witalis3/UA3REO-DDC-Transceiver/Schematic/Wolf-2/Altium_Designer/W2-M_BOARD/Registr.xlsx

Регистр на схеме | Общий БИТ № | Назначение | При = 0 | При = 1
U19 | 0 | Резерв
 | 1 | VHF_TX | Передача ТХ от 2m и выше
 | 2 | FM BAND | Включение FM диапазона |  | Управление ФНЧ
 | 3 | LNA | Включение LNA |  | HFAMP_B0 | HFAMP_B1 | HFAMP_B2 | HFAMP_B3 | BAND ФНЧ
 | 4 | 2.4G BAND | Включение диапазона 2.4G |  | 0 | 0 | 0 | 0 | 40m
 | 5 | 1.2G BAND | Включение диапазона 1.2G |  | 1 | 0 | 0 | 0 | 20m
 | 6 | 430 BAND | Включение диапазона 430 |  | 0 | 1 | 0 | 0 | 15m
 | 7 | 144 BAND | Включение диапазона 144 |  | 1 | 1 | 0 | 0 | 10m
U20 | 8 | HFAMP_B0 | Управление ФНЧ |  | 0 | 0 | 1 | 0 | 6m
 | 9 | HFAMP_B1 |  |  | 1 | 0 | 1 | 0 | 80m
 | 10 | HFAMP_B2 |  |  | 0 | 1 | 1 | 0 | 160m
 | 11 | HFAMP_B3 |  |  | 1 | 1 | 1 | 1 | Выключены
 | 12 | HF TX | Передача ТХ ниже 60МГц
 | 13 | Резерв
 | 14 | Резерв
 | 15 | FAN | Управление вентилятором | Выключен
U21 | 16 | ANT | Включение ANT2
 | 17 | TUNE T | Включение TUNE_T
 | 18 | Резерв | Резерв
 | 19 | Резерв
 | 20 | Резерв
 | 21 | Резерв
 | 22 | Резерв
 | 23 | Резерв
U23 | 24 | Резерв
 | 25 | EXT BAND0 | Внешнее управление УМ и т.д.
 | 26 | EXT BAND1
 | 27 | EXT BAND2
 | 28 | EXT BAND3
 | 29 | EXT TX |  | Всегда при TX
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
