witalis3/UA3REO-DDC-Transceiver/Schematic/Wolf-2/Altium_Designer/W2-HF_AMP/HFAmp_DN_v02.png

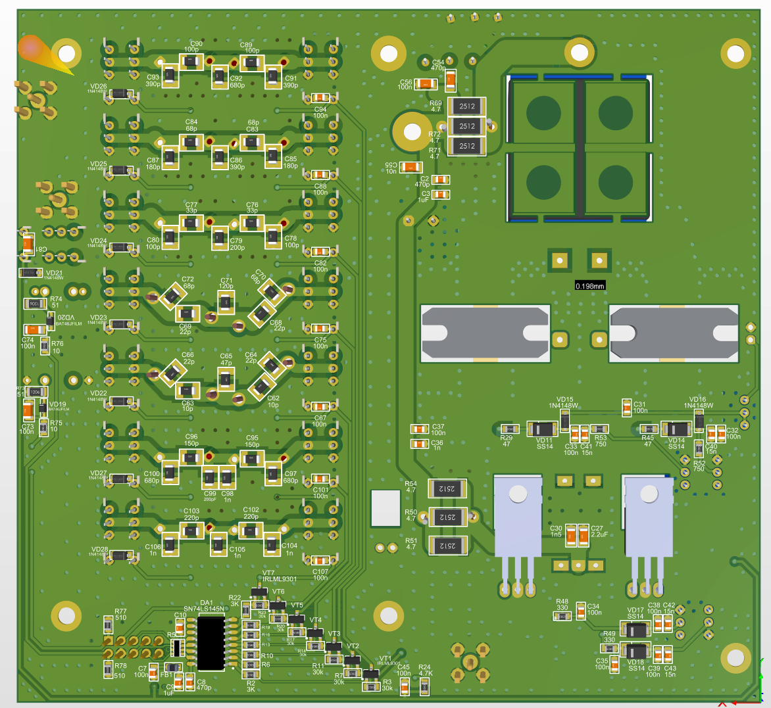
Schematic/Wolf-2/Altium_Designer/W2-HF_AMP/HFAmp_DN_v02.png
