witalis3/UA3REO-DDC-Transceiver/Schematic/Wolf-2/Altium_Designer/W2-Tuner_7x7/Tuner_UP_v01.png

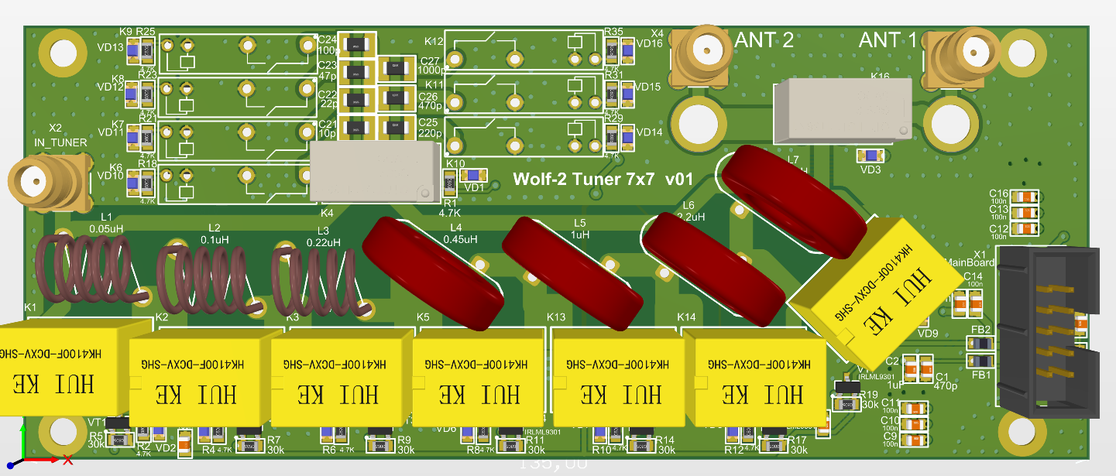
Schematic/Wolf-2/Altium_Designer/W2-Tuner_7x7/Tuner_UP_v01.png
