witalis3/UA3REO-DDC-Transceiver/Schematic/Wolf/Addons/PCB MIC MH-48/pcb4.jpg

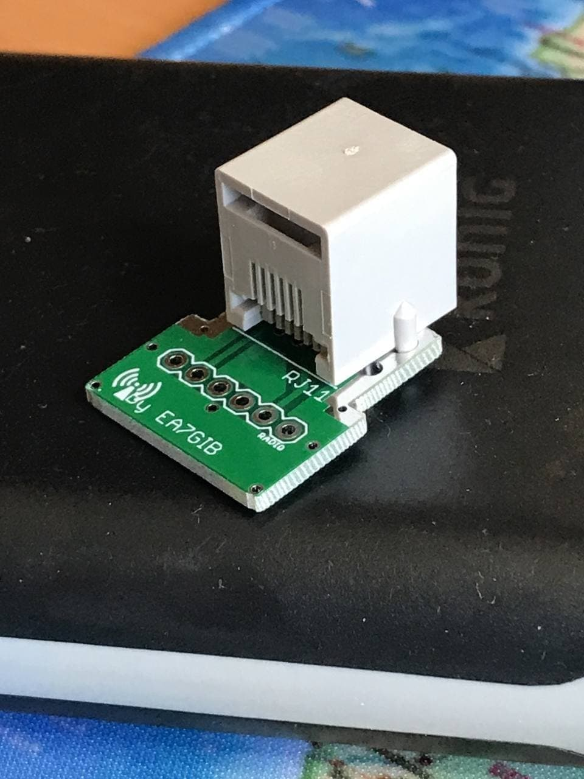
Schematic/Wolf/Addons/PCB MIC MH-48/pcb4.jpg
