witalis3/UA3REO-DDC-Transceiver/Schematic/Wolf/Assembly/SCHEMATIC-RF-UNIT-BIG-RU4PN-rev5.5_DN.png

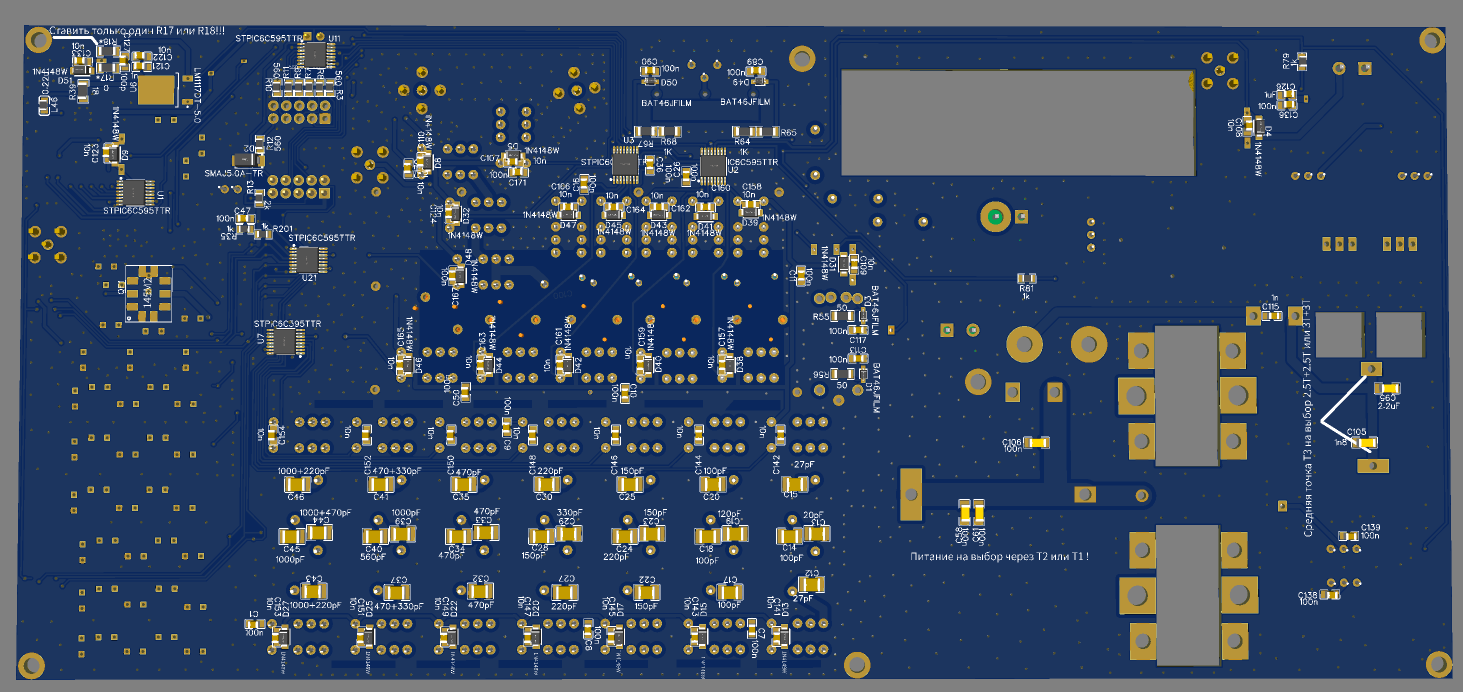
Schematic/Wolf/Assembly/SCHEMATIC-RF-UNIT-BIG-RU4PN-rev5.5_DN.png
