witalis3/UA3REO-DDC-Transceiver/Schematic/Wolf/CASE/3'2/FrontPanel/image.jpg

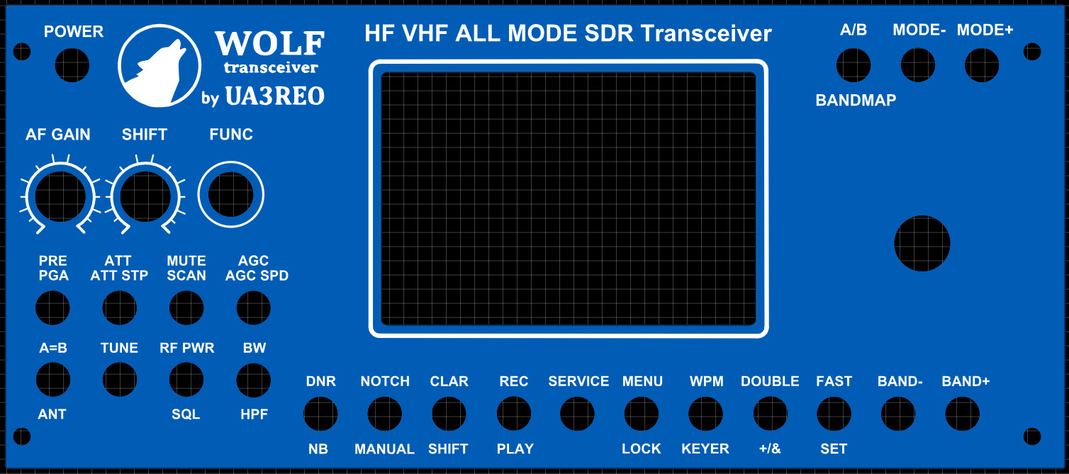
Schematic/Wolf/CASE/3'2/FrontPanel/image.jpg
