witalis3/UA3REO-DDC-Transceiver/Schematic/Wolf/BOM/BOM-RF-UNIT-BIG-rev5.xlsx

Comment | Description | Designator | Footprint | Quantity
 | Capacitor NP0 HiVolt | C96, C97, C98, C99, C100 | CAP_1206 | 5
0 | RES_0805 | R49, R50, R65, R67 | RES_0805 | 4
0.1uH | Inductor | L35 | IND_FERRITE_CORE_1 | 1
0.22uH | Inductor | L36 | IND_FERRITE_CORE_1 | 1
0.45uH | Inductor | L39 | IND_FERRITE_CORE_1 | 1
1:1 | 1:1 | T5 | TRANSF_ACORE2 | 1
1k | RES_0805 | R5, R6, R35, R42, R43, R64, R68 | RES_0805 | 7
1k | RES_0805 | R31, R33, R57, R69, R70, R71, R72 | RESC2013X60X40NL20T25 | 7
1n | CAP_0805 | C112, C115, C120 | CAP_0805 | 3
1n | CAP_0805 | C122 | 6-0805_M | 1
1n | CAP_1206 | C94, C104 | CAP_1206 | 2
1n8 | CAP_1206 | C105 | CAP_1206 | 1
1N4148 | 1N4148 | D4, D5, D6, D8, D9, D10, D11, D12, D13, D14, D15, D16, D17, D19, D20, D21, D22, D24, D25, D26, D27, D28, D29, D30, D31, D32, D38, D39, D40, D41, D42, D43, D44, D45, D46, D47, D48 | SS14 | 37
1uF | CAP_0805 | C62, C63, C79, C83, C126, C128 | CAP_0805 | 6
1uH | Inductor | L7, L8, L9, L41 | IND_FERRITE_CORE_1 | 4
1.2k | RES_0805 | R53 | RES_0805 | 1
1.2n 500V | CAP_1206 | C57 | CAP_1206 | 1
1.6uH | Inductor | L13, L14, L15, L16, L17, L18 | IND_FERRITE_CORE_1 | 6
2k | RES_0805 | R13 | RES_0805 | 1
2p | Capacitor NP0 HiVolt | C2, C3 | CAP_1206 | 2
2.2k | RES_0805 | R77, R78 | RES_0805 | 2
2.2n | Capacitor NP0 HiVolt | C48, C49 | CAP_1206 | 2
2.2p | Capacitor NP0 HiVolt | C7, C8 | CAP_1206 | 2
2.2uF | CAP_1206 | C95 | CAP_1206 | 1
2.2uH | Inductor | L42 | IND_FERRITE_CORE_1 | 1
2.7k | RES_0805 | R37 | RES_0805 | 1
2.7uH | Inductor | L19, L20, L21 | IND_FERRITE_CORE_1 | 3
4.7 | RES_1206 | R38, R47, R74, R76 | RES_1206 | 4
4.7n | CAP_0805 | C70, C75 | CAP_0805 | 2
4.7n | Capacitor NP0 HiVolt, CAP_1206 | C50, C53, C54 | CAP_1206 | 3
5p | Capacitor NP0 HiVolt | C4, C5, C6 | CAP_1206 | 3
5.1p | Capacitor NP0 HiVolt | C12, C13 | CAP_1206 | 2
6.5-30p | TZC3P300A110 | C65, C66 | 5025[2010] | 2
6.8k | RES_0805 | R32 | RES_0805 | 1
6.8n | Capacitor NP0 HiVolt | C1, C51 | CAP_1206 | 2
6.8uH | Inductor | L22, L23, L24 | IND_FERRITE_CORE_1 | 3
8.2nH | IND_0805 | L32, L33, L34 | IND_0805 | 3
10k | RES_1206 | R73 | RES_1206 | 1
10n | CAP_0805 | C121 | 6-0805_M | 1
10n | CAP_1206 | C69, C92, C102 | CAP_1206 | 3
10p | Capacitor | C84 | B32620A0682J000 | 1
10p | Capacitor NP0 HiVolt | C10 | CAP_1206 | 1
10uF 25V | CAPAE_5.3x5.3h6.1 | C129 | CAPAE_5.3x5.3h6.1 | 1
10uH | Inductor | L30, L43 | IND_FERRITE_CORE | 2
11uH | Inductor | L25, L26, L27 | IND_FERRITE_CORE_1 | 3
12p | Capacitor NP0 HiVolt | C9, C11 | CAP_1206 | 2
13.8V | JX2 | J8 | 1986717-2 | 1
15n | CAP_1206 | C81, C111 | CAP_1206 | 2
18 | RES_1206 | R39 | RES_1206 | 1
20 | RES_1206 | R23, R61 | RES_1206 | 2
22 2W | CFR200J100R | R1, R2 | RES-2W | 2
22nH | IND_0805 | L48 | IND_0805 | 1
22p | Capacitor | C85 | B32620A0682J000 | 1
22p | Capacitor NP0 HiVolt | C14, C15, C16, C17, C18, C22, C23 | CAP_1206 | 7
22uF | CAPAE_6.6x6.6h5.4 | C74, C77 | CAPAE_6.6x6.6h5.4 | 2
27pF | CAP_0805 | C55 | CAP_0805 | 1
30k | RES_0805 | R4, R41, R45, R48, R75 | RES_0805 | 5
33p | Capacitor NP0 HiVolt | C20 | CAP_1206 | 1
39p | Capacitor NP0 HiVolt | C19, C21 | CAP_1206 | 2
47p | Capacitor | C86 | B32620A0682J000 | 1
47p | Capacitor NP0 HiVolt | C25 | CAP_1206 | 1
47uF 25V | CAPAE_6.6x6.6h5.4 | C119 | CAPAE_6.6x6.6h5.4 | 1
50 | RES_1206 | R55, R56 | RES_1206 | 2
56 | RES_0805 | R15, R16, R26, R27, R44 | RES_0805 | 5
56p | Capacitor NP0 HiVolt | C24, C26, C27, C28, C32, C33 | CAP_1206 | 6
82p | Capacitor NP0 HiVolt | C30, C37, C39 | CAP_1206 | 3
100 | RES_0805 | R28, R29, R51 | RES_0805 | 3
100 | RES_1206 | R34 | RES_1206 | 1
100n | CAP_0805 | C38, C59, C64, C67, C71, C76, C78, C80, C82, C89, C90, C107, C108, C109, C110, C113, C114, C116, C117, C118, C123, C124, C125, C130, C133, C134, C135, C136, C137, C138, C139, C140, C141, C142, C143, C144, C145, C146, C147, C148, C149, C150, C151, C152, C153, C154, C155, C156, C157, C158, C159, C160, C161, C162, C163, C164, C165, C166, C167, C168, C169, C170, C171 | CAP_0805 | 63
100n | CAP_0805 | C131 | 6-0805_M | 1
100n | CAP_1206 | C58, C61, C106 | CAP_1206 | 3
100p | CAP_0805 | C72 | CAP_0805 | 1
100p | CAP_0805 | C127, C132 | 6-0805_M | 2
100p | Capacitor | C87 | B32620A0682J000 | 1
100p | Capacitor NP0 HiVolt, CAP_1206 | C29, C31, C91, C93, C103 | CAP_1206 | 5
100pF 500V | CAP_1206 | C52, C56 | CAP_1206 | 2
120p | CAP_0805 | C68, C73 | CAP_0805 | 2
120p | Capacitor NP0 HiVolt | C35 | CAP_1206 | 1
150p | Capacitor NP0 HiVolt | C34, C36 | CAP_1206 | 2
158uH | Inductor | L28, L29, L40 | IND_FERRITE_CORE_1 | 3
180p | Capacitor NP0 HiVolt | C41, C43, C44 | CAP_1206 | 3
200 | RES_0805 | R52 | RES_0805 | 1
200nH | Inductor | L1, L2, L3 | IND_FERRITE_CORE_1 | 3
200p | CAP_1206 | C101 | CAP_1206 | 1
200pF 500V | CAP_1206 | C60 | CAP_1206 | 1
220nH | IND_1206 | L31, L46 | IND_1206 | 2
220p | Capacitor | C88 | B32620A0682J000 | 1
220p | Capacitor NP0 HiVolt | C40, C42 | CAP_1206 | 2
300 | RES_1206 | R24, R25, R62, R63 | RES_1206 | 4
390p | Capacitor NP0 HiVolt | C46 | CAP_1206 | 1
430 | RES_1206 | R59, R60 | RES_1206 | 2
470 | RES_1206 | R22 | RES_1206 | 1
470p | Capacitor NP0 HiVolt | C45, C47 | CAP_1206 | 2
510 | RES_0805 | R36, R54 | RES_0805 | 2
560 | RES_0805 | R3, R7, R8, R9, R10, R11, R12 | RES_0805 | 7
620 | RES_0805 | R58 | RES_0805 | 1
680nH | Inductor | L4, L5, L6 | IND_FERRITE_CORE_1 | 3
750 | RES_1206 | R21 | RES_1206 | 1
820nH | Inductor | L10, L11, L12 | IND_FERRITE_CORE_1 | 3
2027-07-SM-RPLF | Undefined or Miscellaneous | U13 | 200307SMRPLF | 1
51022-0200 | 51022-0200 | FAN_OUT | 51022-0200 | 1
ADC | SMA | J2 | 31-5431 | 1
ADG918BRMZ | Integrated Circuit | U8, U10 | SOP65P490X110-8N | 2
ADJ-1k | 306J | R30, R40, R46 | 306J | 3
ADJ-10k | 3296W-1-103LF | R19, R20 | 3296W-1 | 2
ADJ-100 | 306J | R66 | 306J | 1
ANT1 | SMA | J1 | 31-5431 | 1
ANT2 | SMA | J5 | 31-5431 | 1
Axicom IM06 | Axicom IM06 | U4, U12 | IM06GR | 2
BAT46JFILM | Diode | D1, D3, D49, D50 | SOD2513X117N | 4
BAV99 | BAV99 | D7 | SOT23 | 1
BLM21 | BLM21 | FB1 | IND_0805 | 2
BSS123 | N-Channel Logic Level Enhancement Mode Field Effect Transistor, 1.7 V, -55 to 150 degC, 3-Pin SOT-23, RoHS, Tape and Reel | Q12 | FAIR-SOT23-3_V | 1
DAC | SMA | J9 | 31-5431 | 1
EXTERNAL | 2*5 PIN | J3 | 90131-0126 | 1
G6S-2-DC12 | Relay or Contactor | K1, K2, K3, K4, K5, K6, K7, K8, K9, K10, K11, K12, K13, K14, K15, K16, K17, K18, K19, K20, K21, K22, K23, K24, K25, K26, K27, K28, K29, K30, K31, K32, K33, K34, K35 | G6S2DC12 | 35
HiCurrent 13.8V | JX2 | J6, J7 | 1986717-2 | 2
IRLML9301 | MOSFET | Q2, Q7, Q10, Q11 | SOT23 | 4
KTY81/120 | Integrated Circuit | R14 | TO254P420X460X770-2P | 1
LM1117DT-5.0 | Integrated Circuit | U6 | TO228P991X238-3N | 1
LT1117IST-5.0 | LT1117IST-5.0 | U19 | LT1117IST-ADJ | 1
LT1117IST-ADJ | LT1117IST-ADJ | U5, U20 | LT1117IST-ADJ | 2
MOTHERBOARD | 2*5 PIN | J4 | 90131-0126 | 1
PE4302 | Integrated Circuit | U9 | QFN50P400X400X90-21N | 1
PGA-103+ / SPF5189Z | PGA-103+ / SPF5189Z | Q4 | SOT89 | 1
RA80H1415M1 | RA80H1415M1 | Q8 | RA80H1415M1 | 1
RD01MUS1 | RD01MUS1 | Q9 | SOT89 | 1
RD16HHF1 | RD16HHF1 | Q1, Q3 | RD16_V2 | 2
RD100HHF1 | RD100HHF1 | Q5, Q6 | RD100_V2 | 2
SMAJ5.0A-TR | Diode | D2 | SMBJ36CATR | 1
SS14 | SS14 | D18, D23, D35, D36, D37 | SS14 | 5
STPIC6C595TTR | Integrated Circuit | U1, U2, U3, U7, U11 | SOP65P640X120-16N | 5
SWR_TANDEM_MATCH | SWR_TANDEM_MATCH | TSWR | SWR_TANDEM_MATCH | 1
SWR_VHF | SWR_VHF | T6 | SWR_VHF | 1
TRANSF_HF1 | TRANSF_HF1 | T2 | TRANSF_HF1 | 1
TRANSF_HF2 | TRANSF_HF2 | T1 | TRANSF_HF2-3 | 1
TRANSF_HF3 | TRANSF_HF3 | T3 | TRANSF_HF3 | 1
