witalis3/UA3REO-DDC-Transceiver/Schematic/Wolf/CASE/VFO/VFO38WithExt.stl

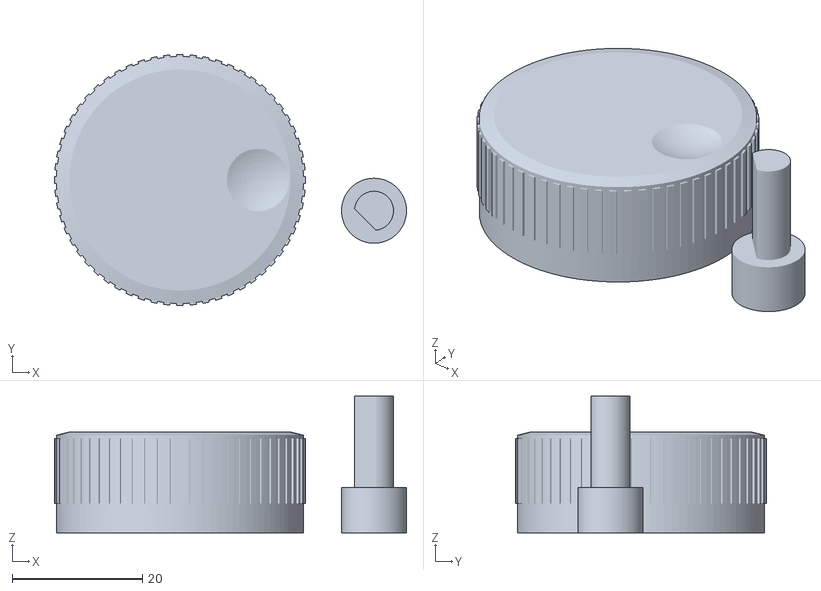
[picture p36: CAD file, 2021-11-08]
Schematic/Wolf/CASE/VFO/VFO38WithExt.stl
54.1 x 38.6 x 21.0
