witalis3/UA3REO-DDC-Transceiver/Schematic/Wolf-X1/Addons/20mm_Sec_Encoder.stl

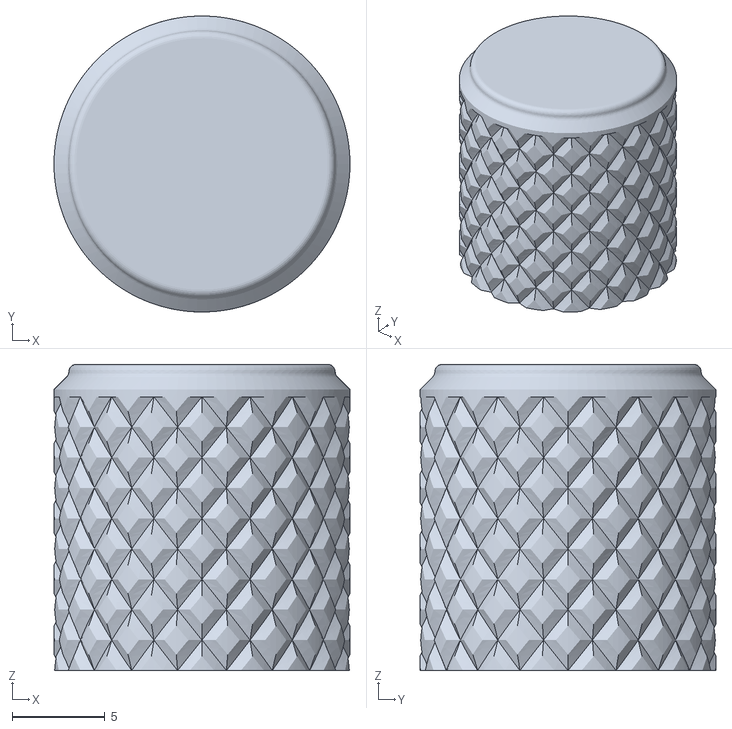
[picture p37: CAD file, 2022-07-16]
Schematic/Wolf-X1/Addons/20mm_Sec_Encoder.stl
16.0 x 16.0 x 16.6
