witalis3/UA3REO-DDC-Transceiver/Schematic/Wolf/CASE/3'2/3DPrinter/case/case_cooller.SLDPRT

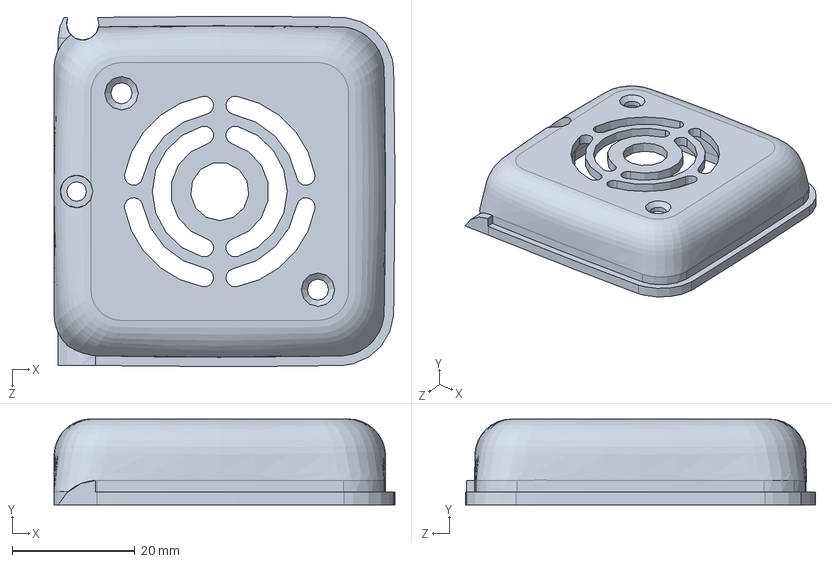
[picture p38: CAD file, 2020-11-11]
Schematic/Wolf/CASE/3'2/3DPrinter/case/case_cooller.SLDPRT
55.5 x 14.0 x 57.1 mm
