witalis3/UA3REO-DDC-Transceiver/Schematic/Wolf/CASE/3'2/3DPrinter/Potenciómetro.stp

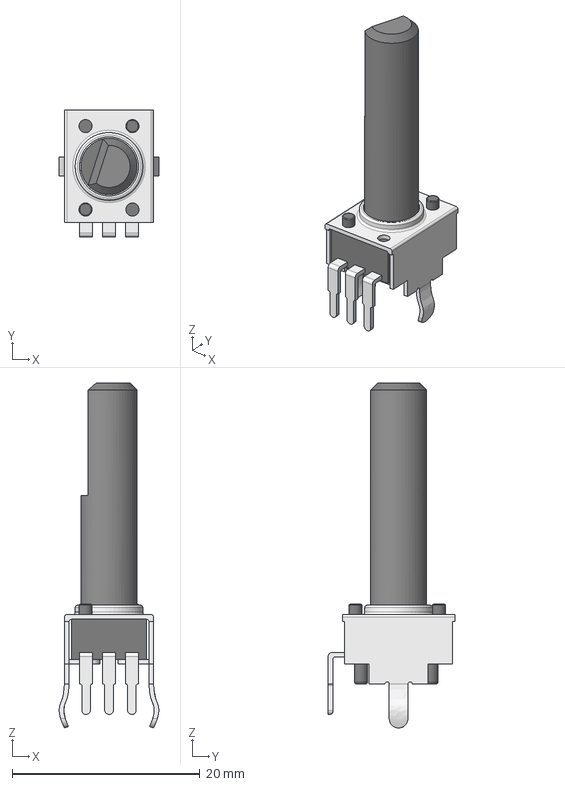
[picture p39: CAD file, 2021-01-28]
Schematic/Wolf/CASE/3'2/3DPrinter/Potenciómetro.stp
10.6 x 13.5 x 36.8 mm
