witalis3/UA3REO-DDC-Transceiver/Schematic/Wolf/CASE/7/Panel/верхняя планка волк7_2.stl

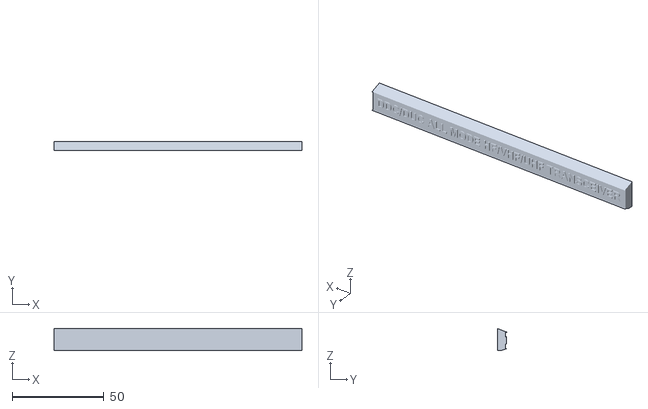
[picture p40: CAD file, 2023-04-02]
Schematic/Wolf/CASE/7/Panel/верхняя планка волк7_2.stl
135.0 x 5.00 x 12.0
