witalis3/UA3REO-DDC-Transceiver/Schematic/Wolf/CASE/VFO/ExtEncoder.stl

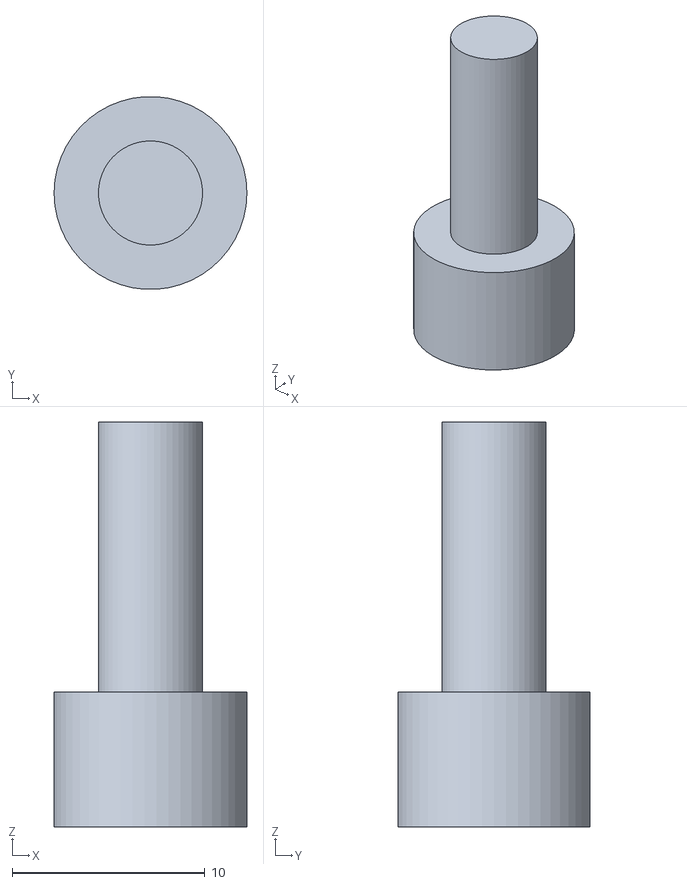
[picture p41: CAD file, 2021-11-08]
Schematic/Wolf/CASE/VFO/ExtEncoder.stl
10.0 x 9.98 x 21.0
