witalis3/UA3REO-DDC-Transceiver/Schematic/Wolf/CASE/3'2/3DPrinter/case/encoder_mount_front.SLDPRT

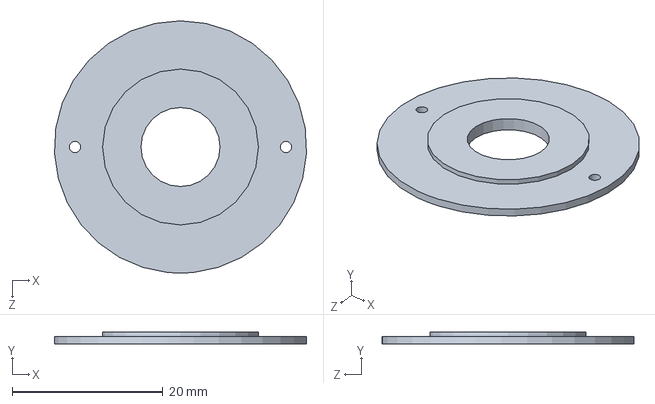
[picture p44: CAD file, 2020-11-11]
Schematic/Wolf/CASE/3'2/3DPrinter/case/encoder_mount_front.SLDPRT
33.5 x 1.65 x 33.5 mm
