witalis3/UA3REO-DDC-Transceiver/Schematic/Wolf/CASE/3'2/3DPrinter/pl-259_jack.stp

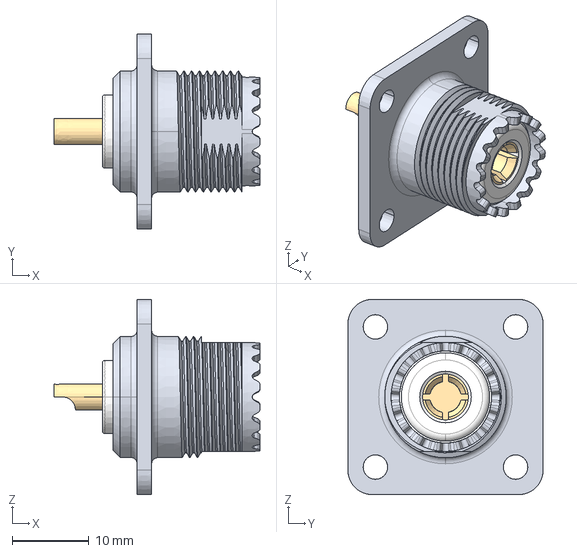
[picture p45: CAD file, 2021-01-28]
Schematic/Wolf/CASE/3'2/3DPrinter/pl-259_jack.stp
26.8 x 25.4 x 25.4 mm
