witalis3/UA3REO-DDC-Transceiver/Schematic/Wolf/CASE/7/Panel/рамка_низ_7_пр.stl

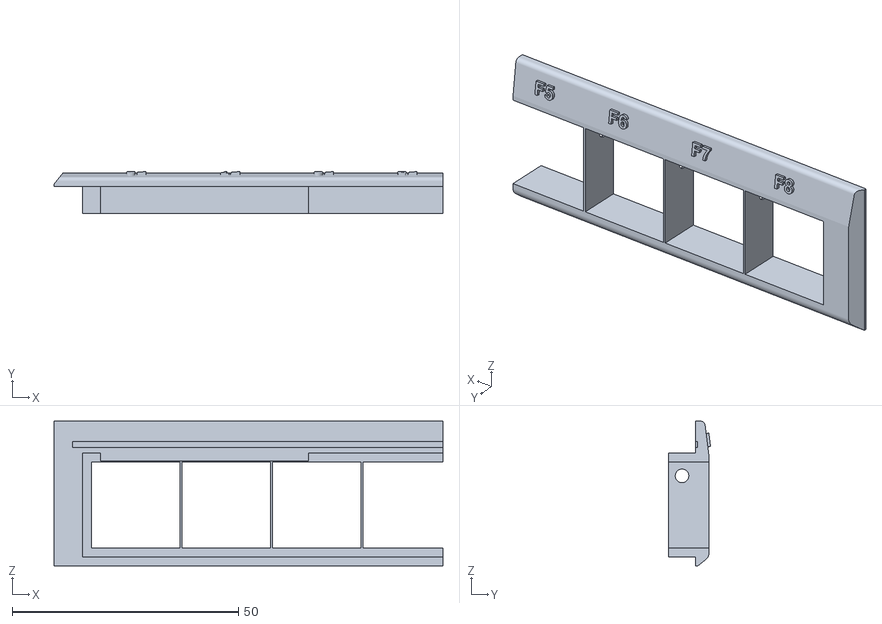
[picture p46: CAD file, 2023-04-02]
Schematic/Wolf/CASE/7/Panel/рамка_низ_7_пр.stl
86.0 x 9.31 x 32.0
