witalis3/UA3REO-DDC-Transceiver/Schematic/Wolf/CASE/3'2/3DPrinter/case/shuttle_knob_cap.SLDPRT

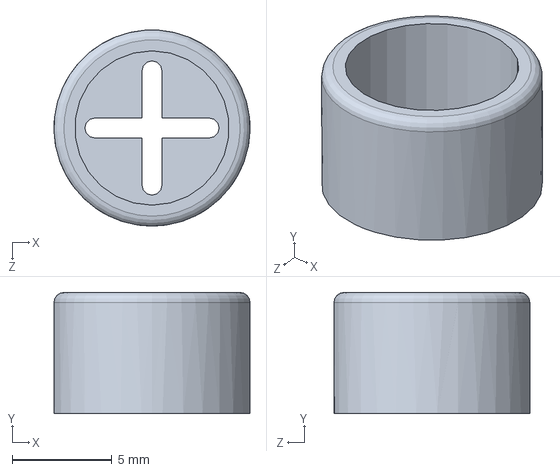
[picture p47: CAD file, 2020-11-11]
Schematic/Wolf/CASE/3'2/3DPrinter/case/shuttle_knob_cap.SLDPRT
9.84 x 6.08 x 9.85 mm
