witalis3/UA3REO-DDC-Transceiver/Schematic/Wolf/CASE/3'2/3DPrinter/GX16-8.stp

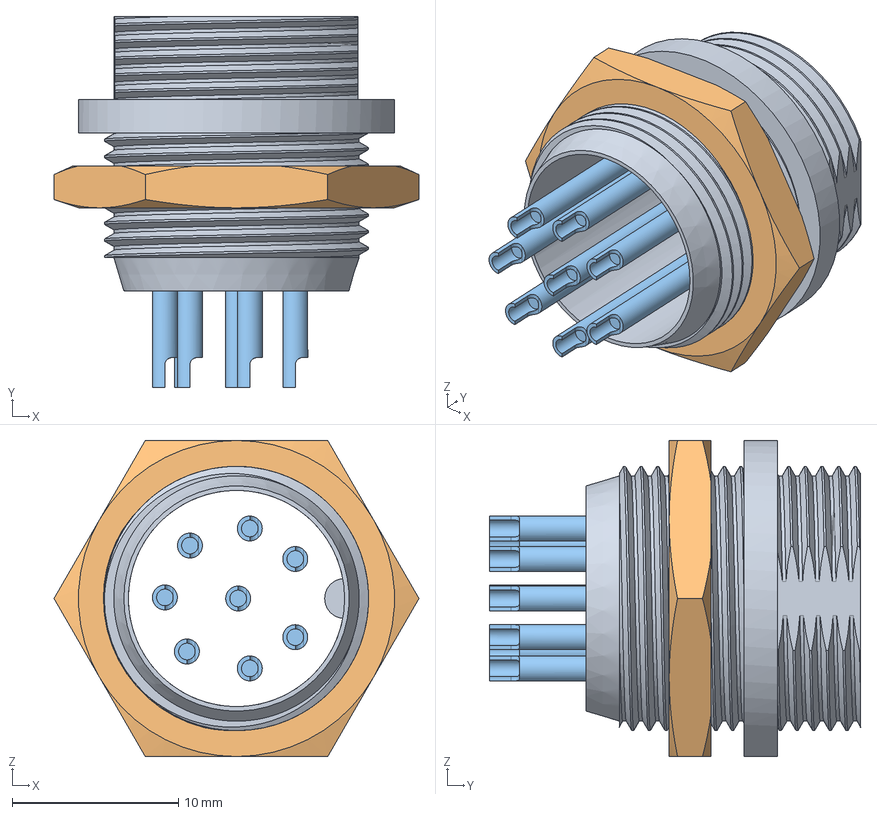
[picture p48: CAD file, 2021-01-28]
Schematic/Wolf/CASE/3'2/3DPrinter/GX16-8.stp
21.9 x 22.3 x 19.0 mm
