witalis3/UA3REO-DDC-Transceiver/Schematic/Wolf/CASE/7/Panel/рамка_низ_7_л.stl

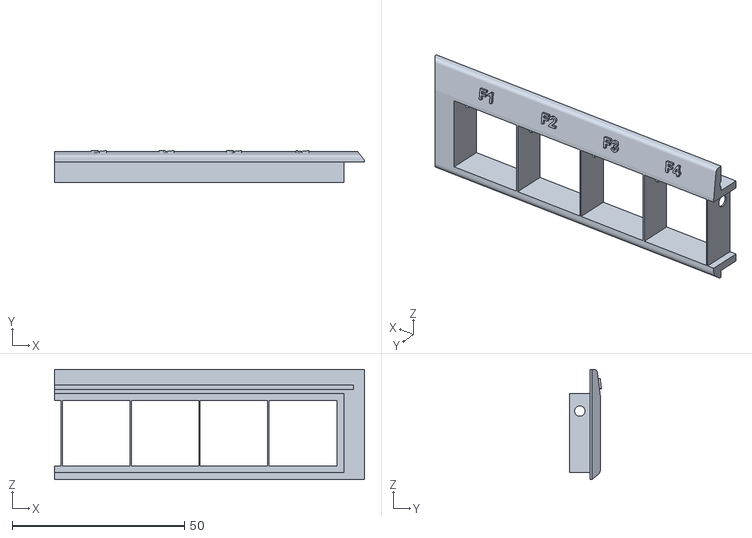
[picture p49: CAD file, 2023-04-02]
Schematic/Wolf/CASE/7/Panel/рамка_низ_7_л.stl
90.0 x 9.31 x 32.0
