witalis3/UA3REO-DDC-Transceiver/Schematic/Wolf/CASE/3'2/3DPrinter/40x40x10 DC Fan.SLDPRT

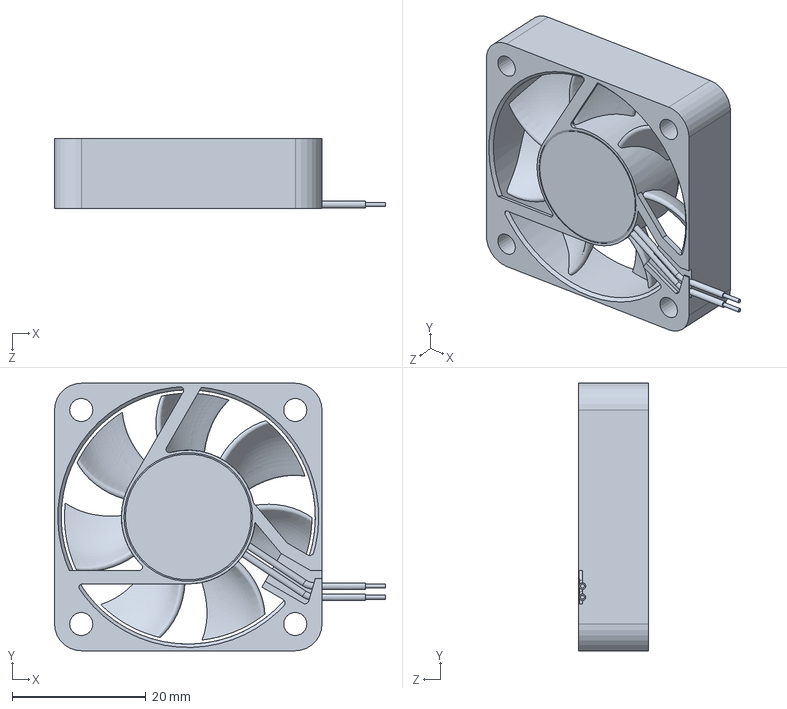
[picture p50: CAD file, 2020-11-11]
Schematic/Wolf/CASE/3'2/3DPrinter/40x40x10 DC Fan.SLDPRT
49.5 x 40.0 x 10.5 mm
