witalis3/UA3REO-DDC-Transceiver/Schematic/Wolf/CASE/3'2/3DPrinter/case/shuttle_knob.SLDPRT

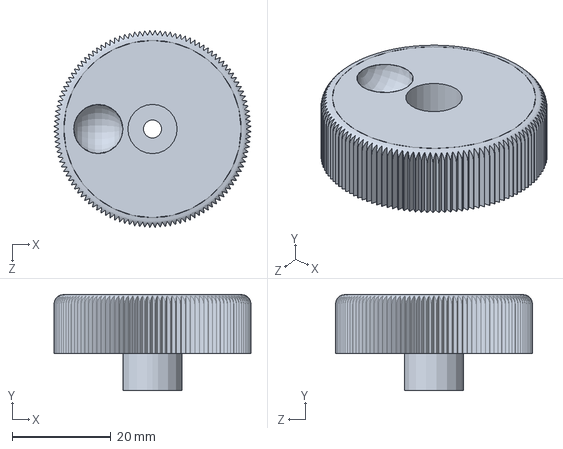
[picture p51: CAD file, 2020-11-11]
Schematic/Wolf/CASE/3'2/3DPrinter/case/shuttle_knob.SLDPRT
40.0 x 19.5 x 40.0 mm
