witalis3/UA3REO-DDC-Transceiver/Schematic/Wolf/CASE/7/Panel/кнопка_низ_7_новая.stl

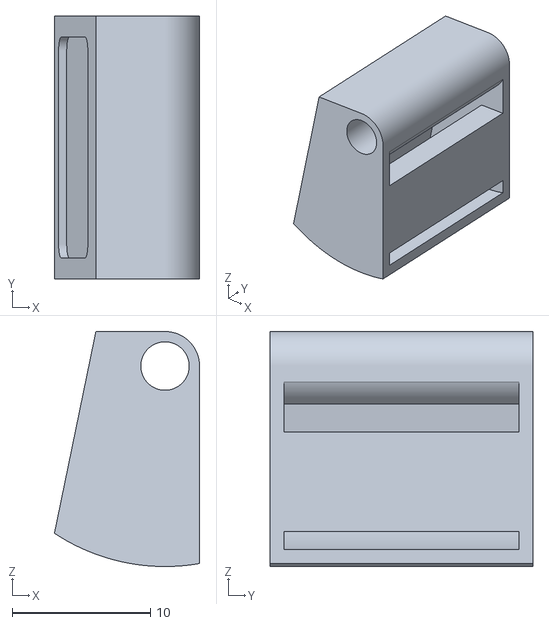
[picture p53: CAD file, 2023-04-02]
Schematic/Wolf/CASE/7/Panel/кнопка_низ_7_новая.stl
10.5 x 19.0 x 17.0
