witalis3/UA3REO-DDC-Transceiver/Schematic/Wolf/CASE/3'2/3DPrinter/FRONT.SLDPRT

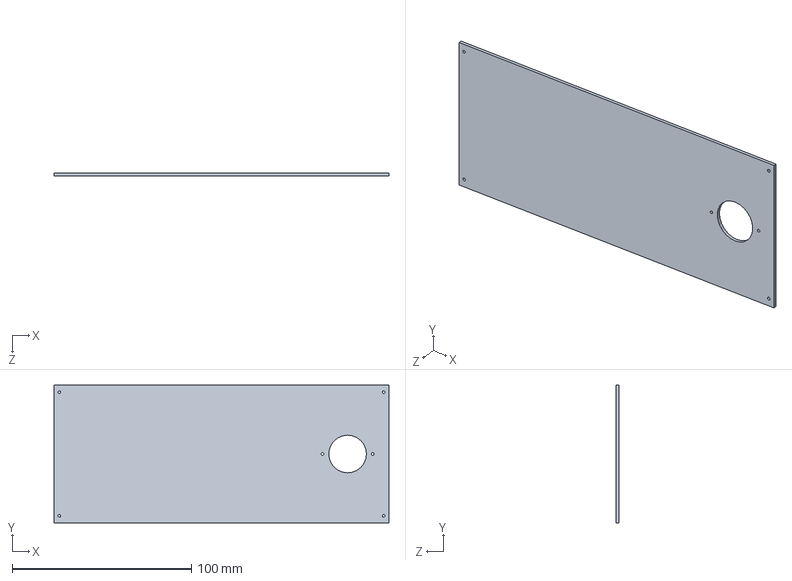
[picture p54: CAD file, 2020-11-11]
Schematic/Wolf/CASE/3'2/3DPrinter/FRONT.SLDPRT
187.0 x 77.0 x 1.60 mm
