witalis3/UA3REO-DDC-Transceiver/Schematic/Wolf/CASE/7/Panel/кнопка верх_7.stl

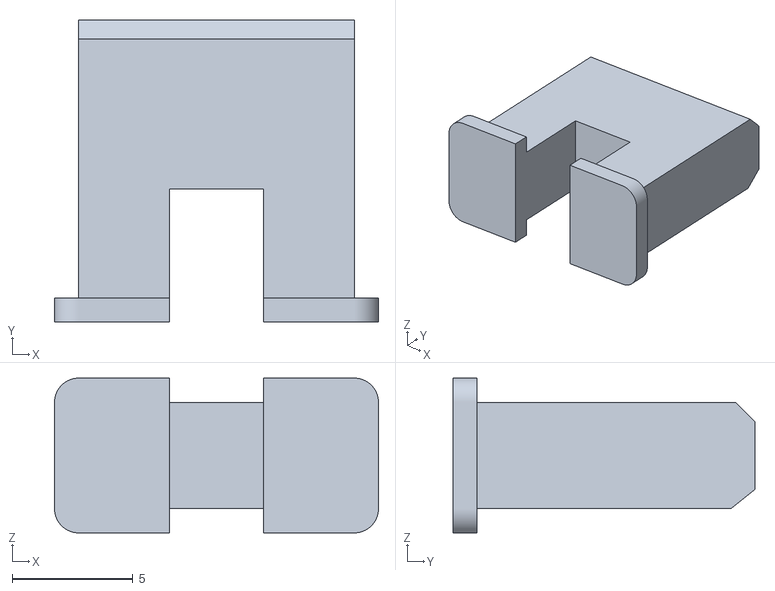
[picture p57: CAD file, 2023-04-02]
Schematic/Wolf/CASE/7/Panel/кнопка верх_7.stl
13.4 x 12.5 x 6.40
