witalis3/UA3REO-DDC-Transceiver/Schematic/Wolf/CASE/3'2/3DPrinter/speaker.SLDPRT

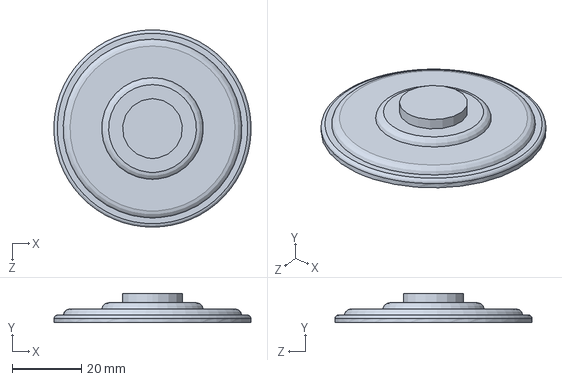
[picture p59: CAD file, 2020-11-11]
Schematic/Wolf/CASE/3'2/3DPrinter/speaker.SLDPRT
56.9 x 8.51 x 57.0 mm
