witalis3/UA3REO-DDC-Transceiver/Schematic/Wolf/CASE/3'2/3DPrinter/case/button.SLDPRT

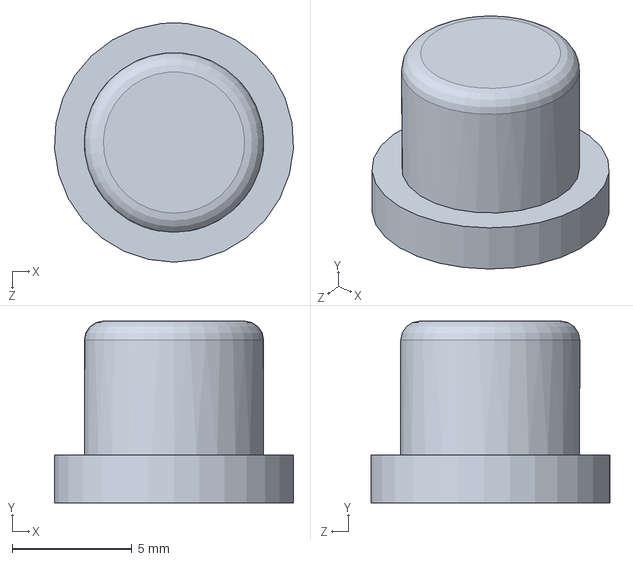
[picture p60: CAD file, 2020-11-11]
Schematic/Wolf/CASE/3'2/3DPrinter/case/button.SLDPRT
9.99 x 7.60 x 10.0 mm
