witalis3/UA3REO-DDC-Transceiver/Schematic/Wolf/CASE/3'2/3DPrinter/tactileswitch-long.SLDPRT

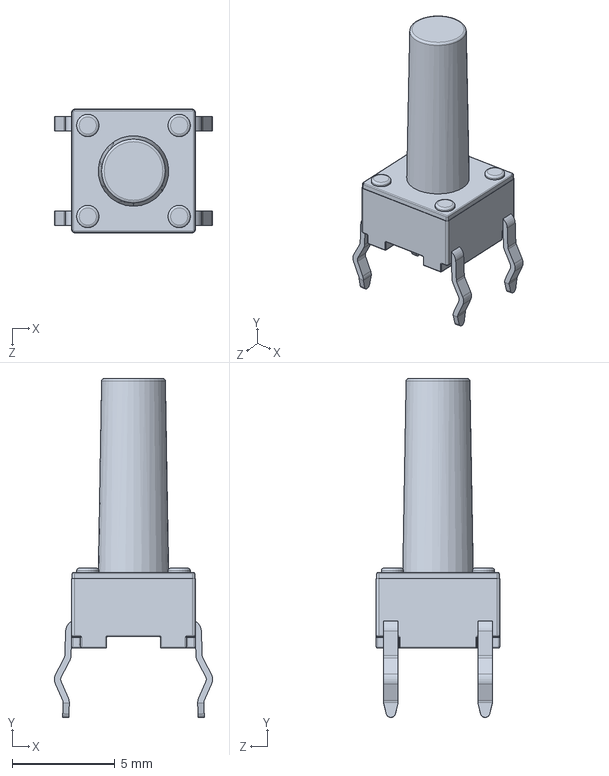
[picture p61: CAD file, 2020-11-11]
Schematic/Wolf/CASE/3'2/3DPrinter/tactileswitch-long.SLDPRT
7.69 x 16.5 x 6.01 mm
