witalis3/UA3REO-DDC-Transceiver/Schematic/Wolf/CASE/3'2/3DPrinter/case/case_back_2.SLDPRT

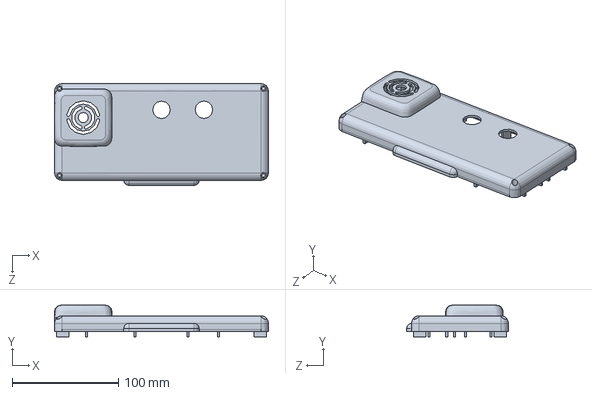
[picture p62: CAD file, 2020-11-11]
Schematic/Wolf/CASE/3'2/3DPrinter/case/case_back_2.SLDPRT
201.0 x 29.7 x 95.7 mm
