witalis3/UA3REO-DDC-Transceiver/Schematic/Wolf/CASE/3'2/3DPrinter/beam_long.SLDPRT

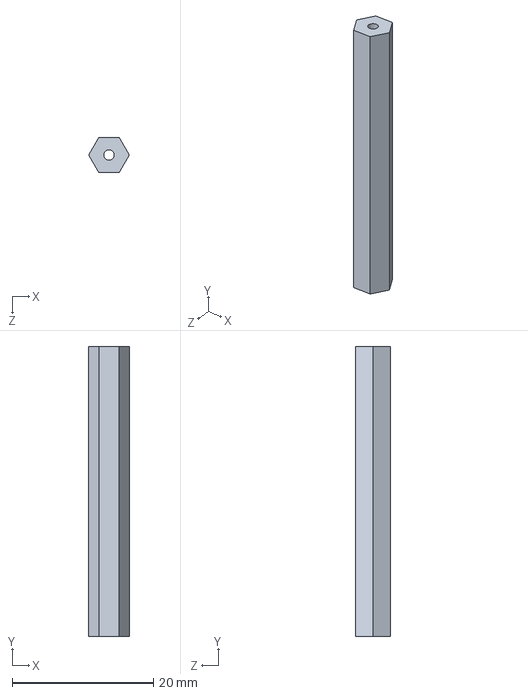
[picture p64: CAD file, 2020-11-11]
Schematic/Wolf/CASE/3'2/3DPrinter/beam_long.SLDPRT
5.77 x 41.1 x 5.00 mm
