witalis3/UA3REO-DDC-Transceiver/Schematic/Wolf/CASE/3'2/3DPrinter/case/case_speaker.SLDPRT

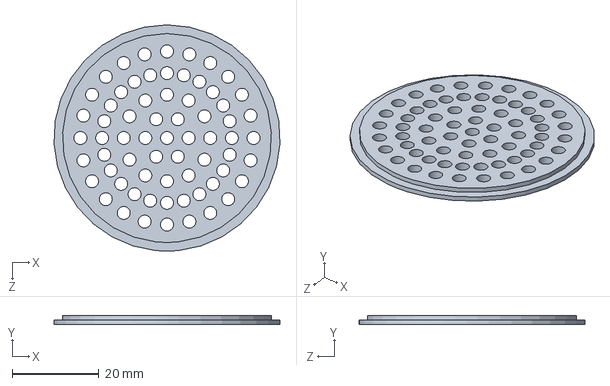
[picture p65: CAD file, 2020-11-11]
Schematic/Wolf/CASE/3'2/3DPrinter/case/case_speaker.SLDPRT
52.2 x 2.00 x 52.3 mm
