witalis3/UA3REO-DDC-Transceiver/Schematic/Wolf/CASE/3'2/3DPrinter/Mini USB.SLDPRT

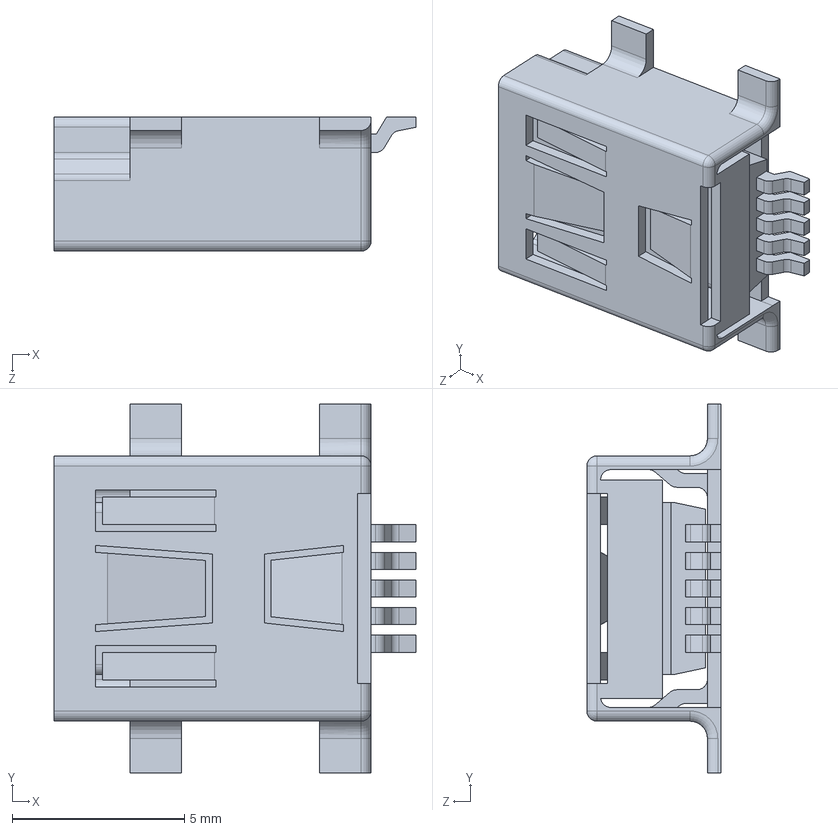
[picture p68: CAD file, 2020-11-11]
Schematic/Wolf/CASE/3'2/3DPrinter/Mini USB.SLDPRT
10.5 x 10.7 x 3.90 mm
