witalis3/UA3REO-DDC-Transceiver/Schematic/Wolf/CASE/3'2/3DPrinter/Encoder_Axis.SLDPRT

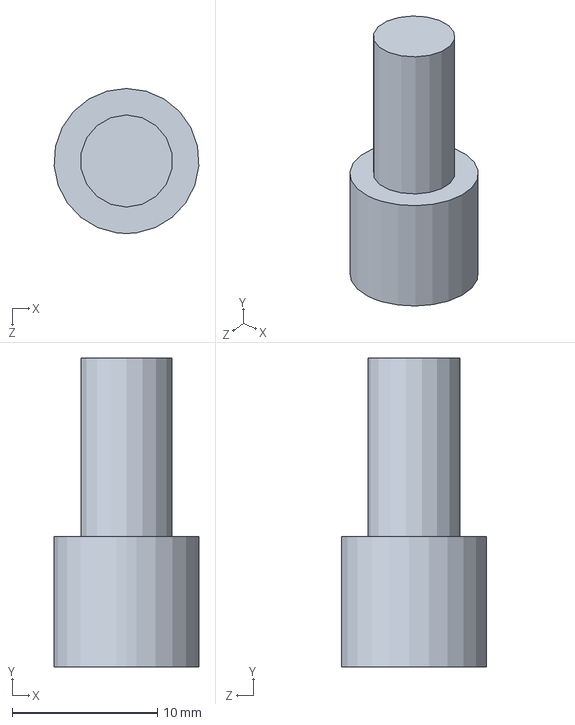
[picture p70: CAD file, 2020-11-11]
Schematic/Wolf/CASE/3'2/3DPrinter/Encoder_Axis.SLDPRT
9.98 x 21.3 x 10.0 mm
