witalis3/UA3REO-DDC-Transceiver/Schematic/Wolf/CASE/3'2/3DPrinter/Rotary Encoder.SLDPRT

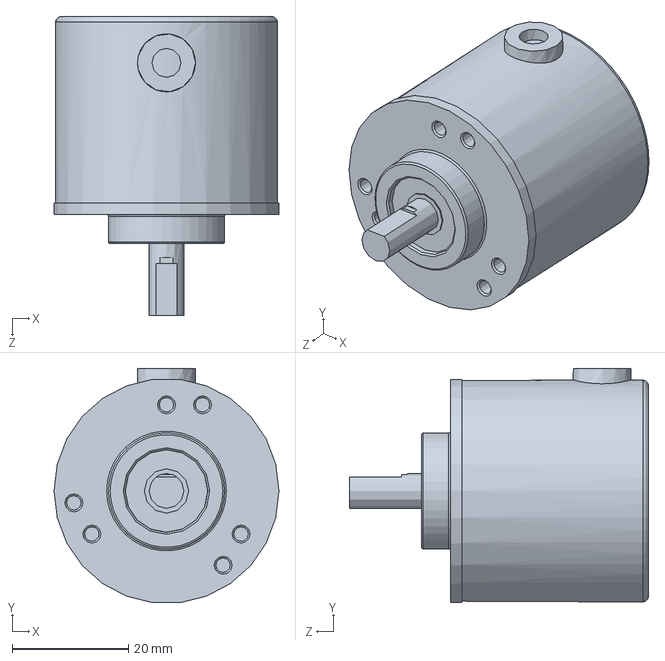
[picture p71: CAD file, 2020-05-22]
Schematic/Wolf/CASE/3'2/3DPrinter/Rotary Encoder.SLDPRT
38.7 x 40.3 x 51.5 mm
