witalis3/UA3REO-DDC-Transceiver/Stuff/Manuals/Front-Panel.xlsx

POWER
 |  |  |  |  | FRONT-3'2 |  |  |  |  |  |  | A/B BANDMAP | MODE- | MODE+
AF GAIN | SHIFT/GAIN | ENC 2
PRE PGA | ATT ATT STEP | MUTE SCAN | AGC AGC SPEED |  |  |  |  |  |  |  |  |  | MAIN ENCODER
A=B ANT | TUNE | RF POWER SQUELCH | BW HPF
 |  |  |  | DNR NB | NOTCH MANUAL | CLAR SHIFT | REC PLAY | SERVICES | MENU LOCK | WPM KEYER | DOUBLE + / & | FAST FAST SETT | BAND- | BAND+
POWER |  | FRONT-7 |  |  |  |  |  |  |  |  |  | SHIFT/GAIN | ENC 2 | AF GAIN
AUDIO 1 |  |  |  |  |  |  |  |  |  |  |  | A/B A=B | MODE+ MODE- | BAND+ BAND-
AUDIO 2
AUDIO 3
 |  |  |  |  |  |  |  |  |  |  |  |  | MAIN ENCODER
TANGENT
 |  | F1 | F2 | F3 | F4 | F5 | F6 | F7 | F8
