witalis3/UA3REO-DDC-Transceiver/Schematic/Wolf/Altium_Designer/RF-UNIT-QRP_20W/!AdditionalInfo/Consumption_Measurements.xlsx

Vin [V] | 13
TX Current Consumption without the RF Unit Board [A] | 0.4
RX Total Current Consumption [A] | 0.771
Band | Output Power (after the LPF) [W] | TX Total Consumption [A] | TX RF Unit Board Consumption [A] | RF_AMP Efficiency [-]
80m | 18.1 | 3.01 | 2.61 | 0.5334512231
40m | 20.4 | 3.83 | 3.43 | 0.457501682
30m | 19.9 | 3.14 | 2.74 | 0.5586749017
20m | 18.9 | 3.45 | 3.05 | 0.4766708701
17m | 20 | 3.25 | 2.85 | 0.5398110661
15m | 19.8 | 3.89 | 3.49 | 0.4364117258
10m | 14 | 2.99 | 2.59 | 0.4158004158
6m | 12.2 | 3.17 | 2.77 | 0.3387947792
2m | 7.1 | 2.74 | 2.34 | 0.2333990796
