witalis3/UA3REO-DDC-Transceiver/Schematic/Wolf-Lite/Scheme/Front-Unit-v2.2.pdf

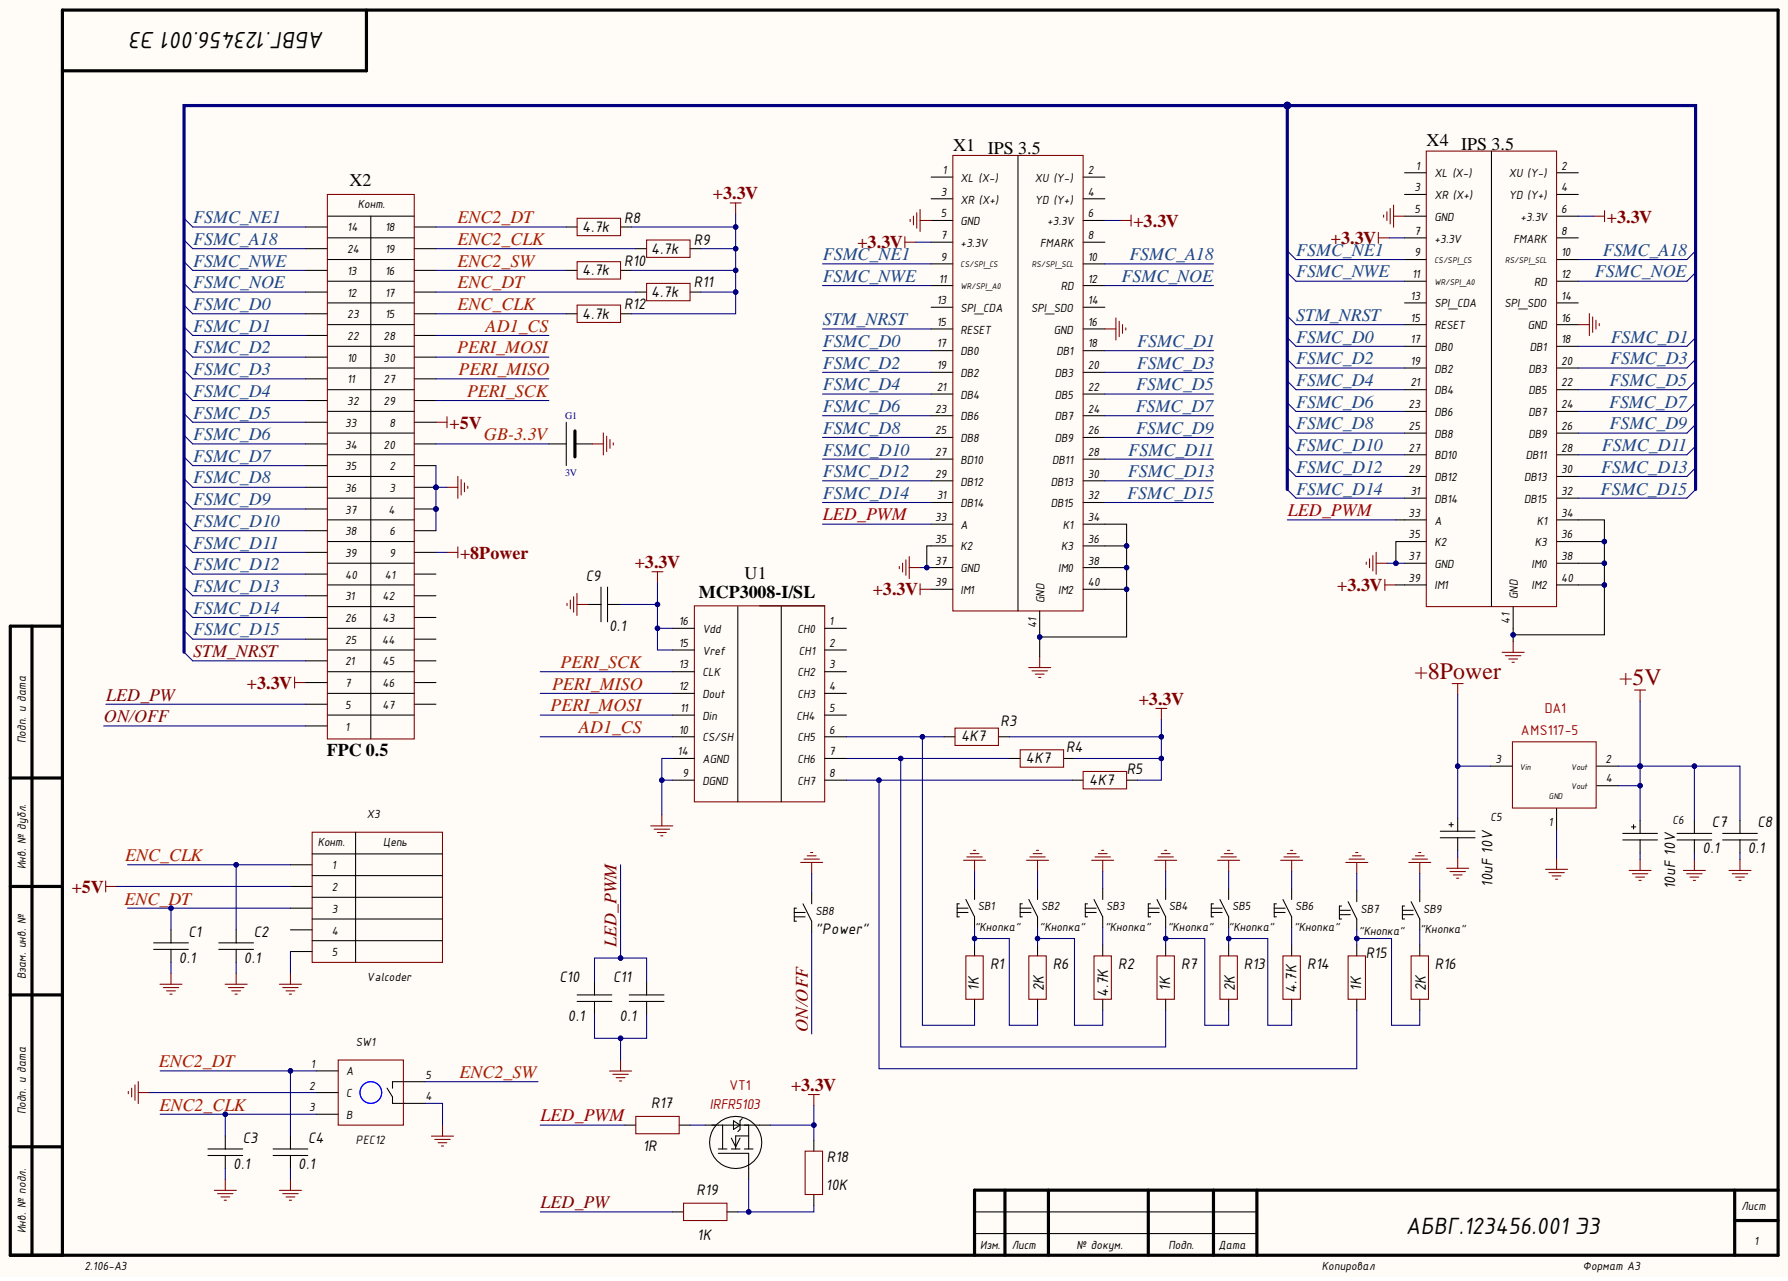
[picture p214: page 1]

Инв. № подл. Инв. № дубл. Подп. и дата Взам. инв. № Подп. и дата

Конт. | Цепь

Comment | Description | Designator | Footprint | LibRef | Quantity
0.1 | | C1, C2, C3, C4, C7, C8, C9, C10, C11 | CH0805C | Capacitor | 9
10uF 10V | | C5, C6 | TANTAL_B | TantalCap | 2
AMS117-5 | | DA1 | SOT223 | AMS117 | 1
3V | | G1 | BAT: CH224-2032 | POWER_BAT | 1
1K | | R1, R7, R15, R19 | CH0805R | Resistor | 4
4.7K | | R2, R8, R9, R10, R11, R12, R14 | CH0805R | Resistor | 7
4K7 | | R3, R4, R5 | CH0805R | Resistor | 3
2K | | R6, R13, R16 | CH0805R | Resistor | 3
1R | | R17 | CH0805R | Resistor | 1
10K | | R18 | CH0805R | Resistor | 1
"Кнопка" | 6x6mm | SB1, SB2, SB3, SB4, SB5, SB6, SB7, SB9 | BUT: 5X5 | Tactile switches | 8
"Power" | 6x6mm | SB8 | BUT: 5X5 | Tactile switches | 1
PEC12 | Encoder | SW1 | Valkoder-m2 | PEC12 | 1
MCP3008-I/SL | | U1 | 16-SOIC | MCP3008-I/SL | 1
IRFR5103 | | VT1 | SOT23_132 | N-KANAL | 1
IPS 3.5 | | X1 | FPC-40P 0.5mm | LCD-IPS 3.5 | 1
FPC 0.5 | | X2 | CON: PBD2x20 | FPC-45-0.5 | 1
Valcoder | | X3 | CON: PLS-5 | 5-Connector | 1
IPS 3.5 | | X4 | IPS 3.5 ILI9481 | LCD-IPS 3.5 | 1
