witalis3/UA3REO-DDC-Transceiver/Schematic/Wolf/Altium_Designer/RF-UNIT-QRP_20W/!AdditionalInfo/Heatsink_QRP++.pdf

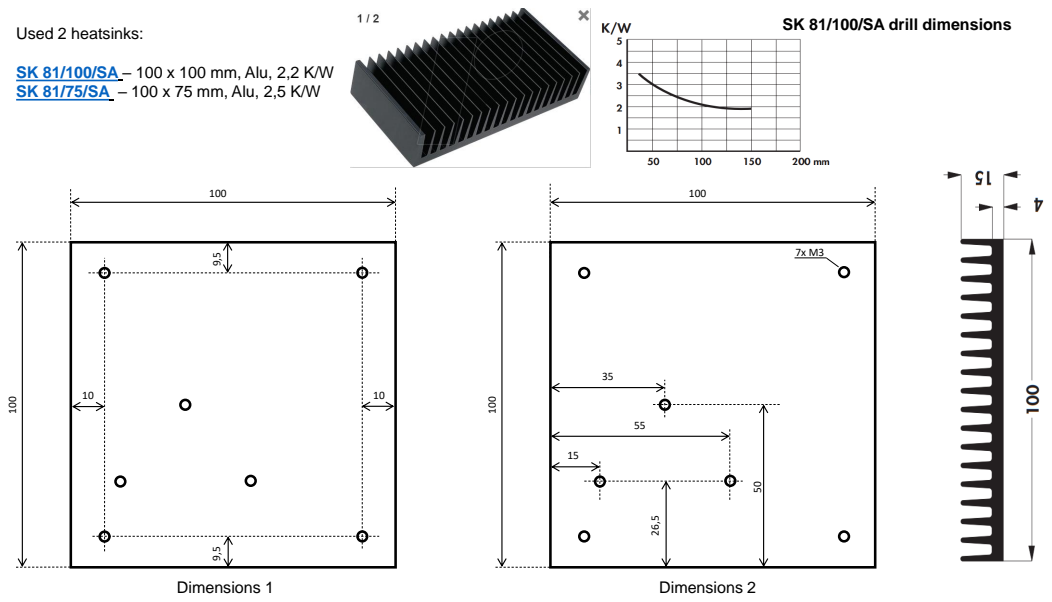
[picture p219: page 1]
Used 2 heatsinks:; Dimensions 1; Dimensions 2

SK 81/100/SA drill dimensions

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

SK 81/75/SA drill dimensions

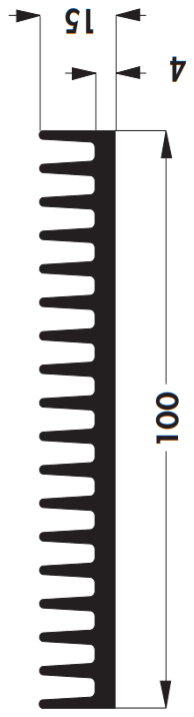
[picture p220: figure]
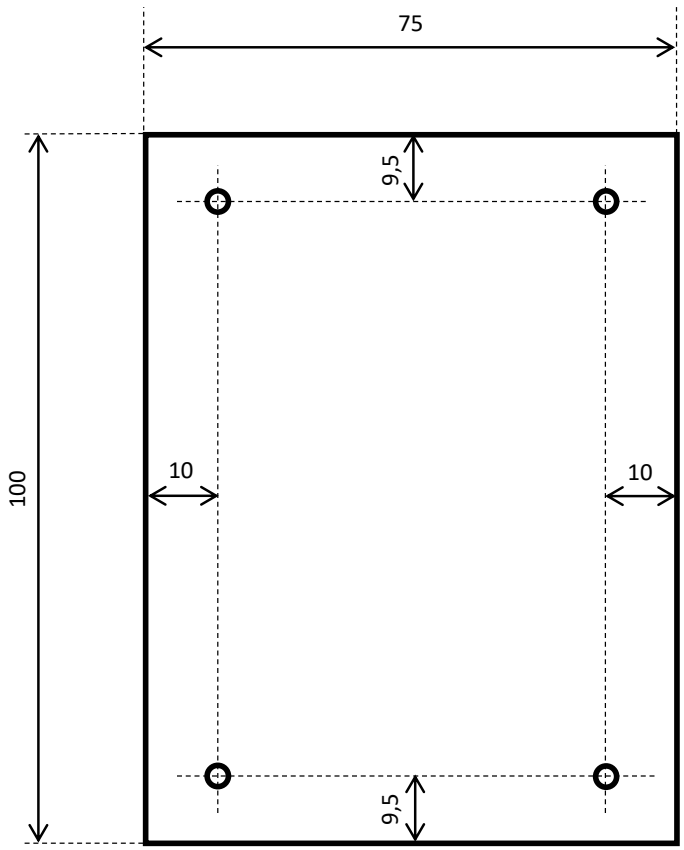
[picture p221: figure]
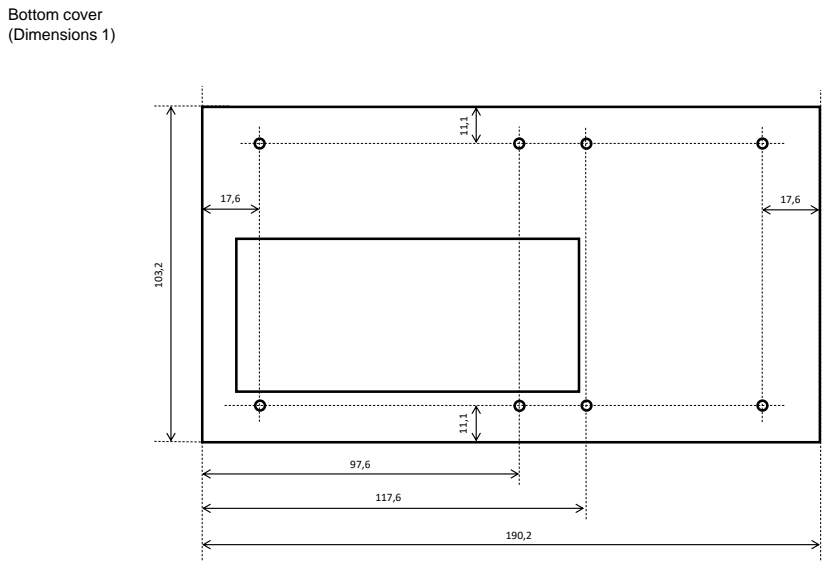
[picture p222: page 3]
Bottom cover (Dimensions 1)

Bottom cover
(Dimensions 2)

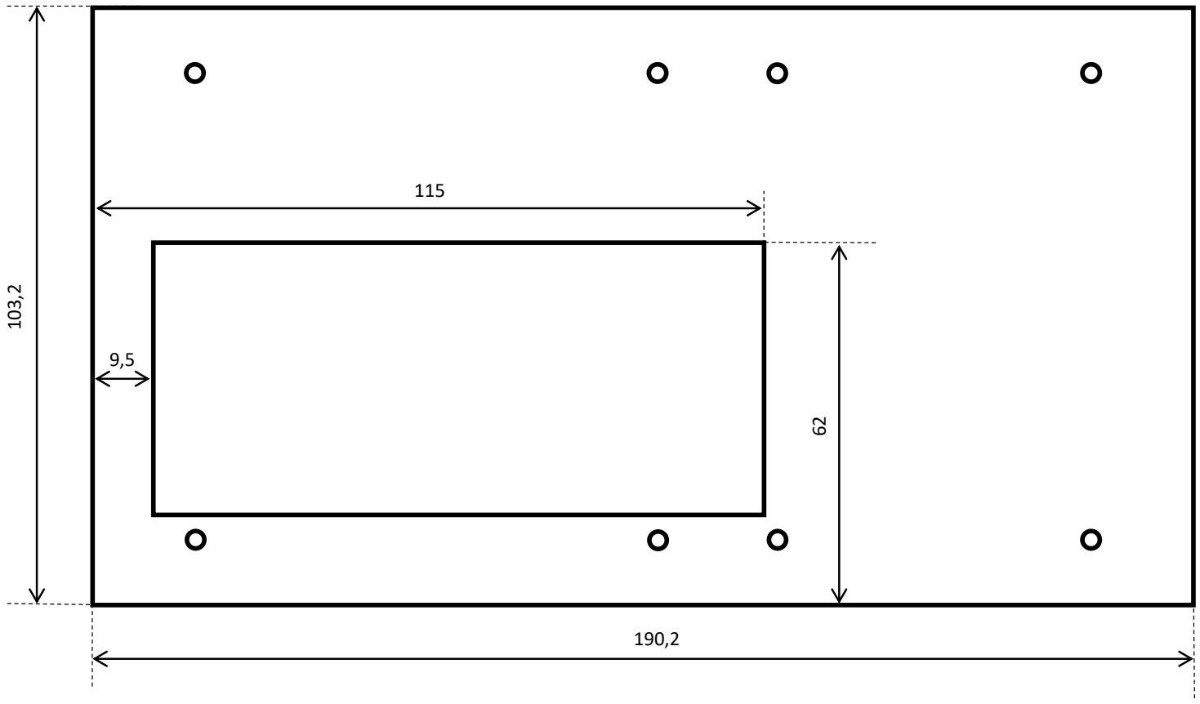
[picture p223: figure]
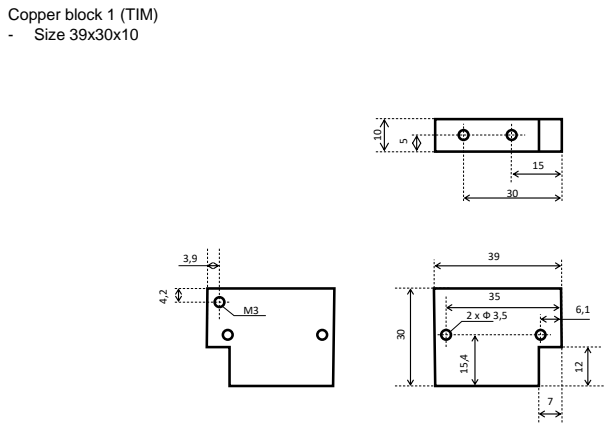
[picture p224: page 5]

Copper block 1 (TIM)
- Size 39x30x10

Copper block 1 (TIM)
- Size 39x20x8

8

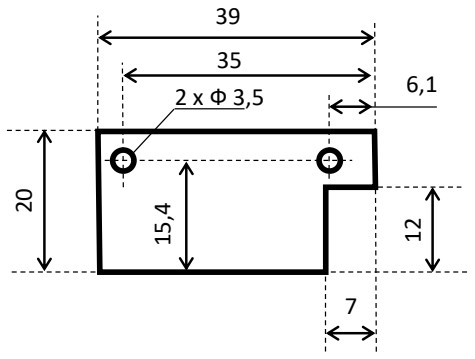
[picture p225: figure]
