witalis3/UA3REO-DDC-Transceiver/Schematic/Wolf/Addons/AD8307_Add_on_v3/_Print/AD8307_Add_on_v3.pdf

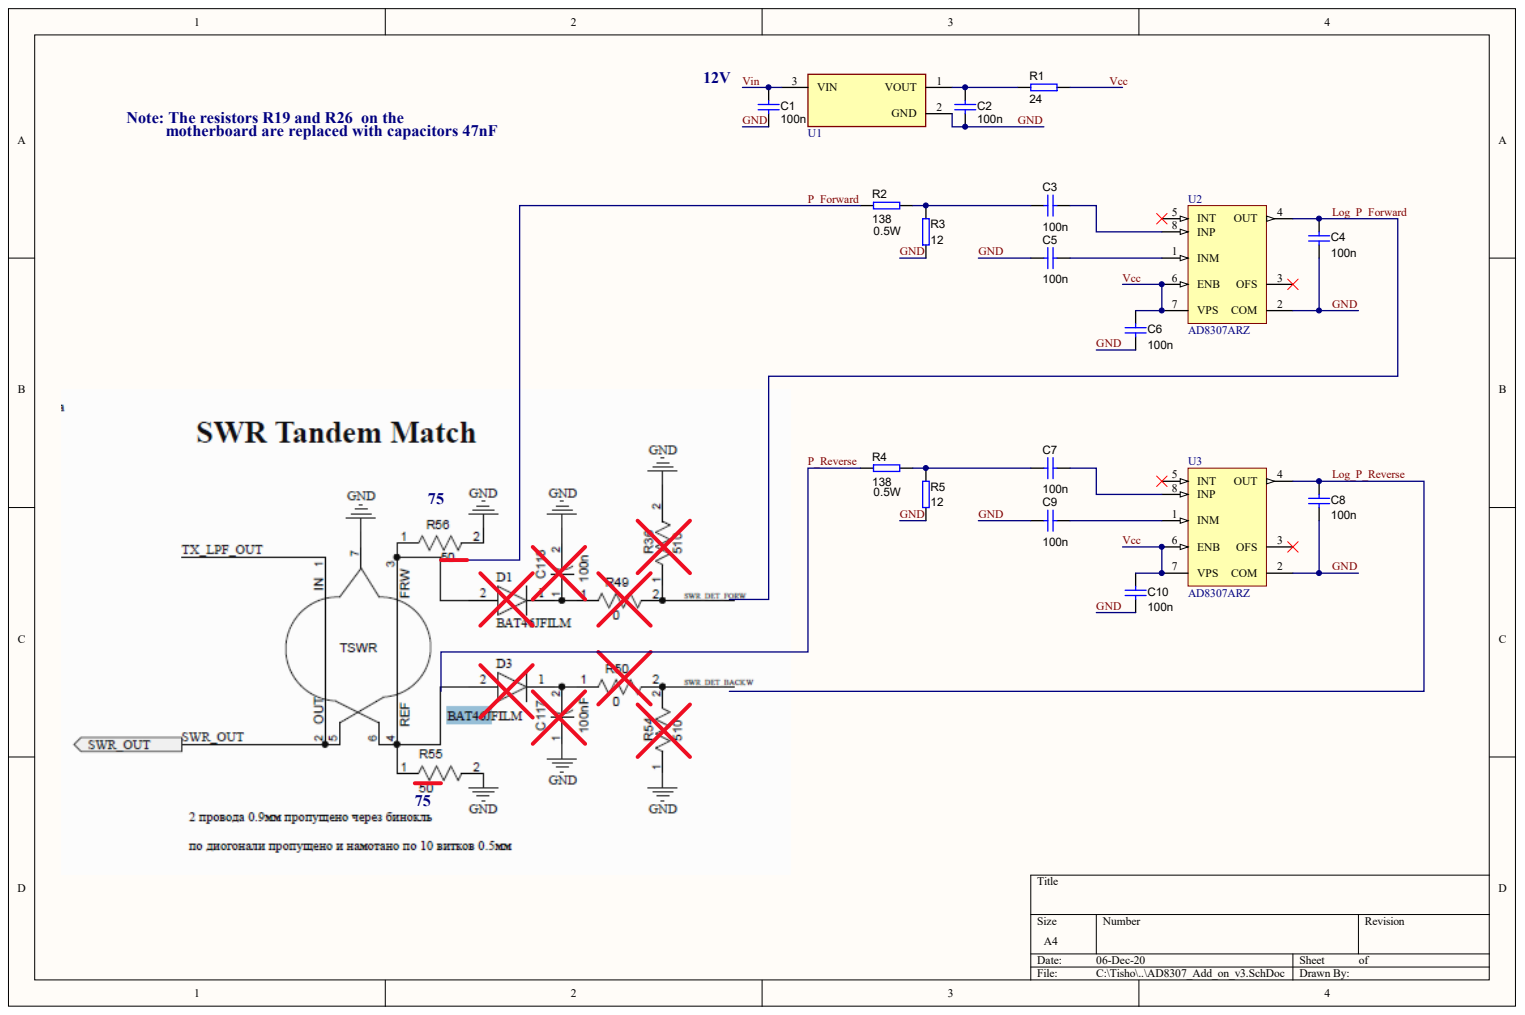
[picture p226: page 1]

Note: The resistors R19 and R26 on the motherboard are replaced with capacitors 47nF

Size A4 | Number | Revision

Date: 06-Dec-20 | Sheet of
File: C:\Tisho\..\AD8307_Add_on_v3.SchDoc | Drawn By:

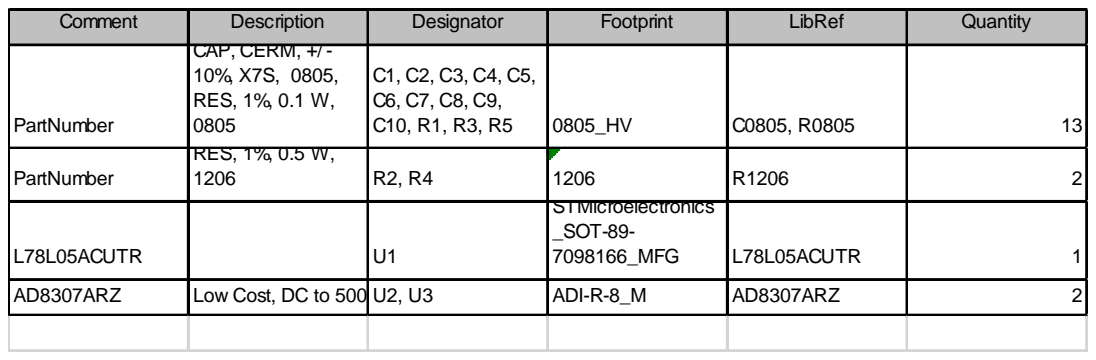
[picture p227: page 2]

Comment | Description | Designator | Footprint | LibRef | Quantity
PartNumber | CAP, CERM, +/ -10%, X7S, 0805, RES, 1%, 0.1 W, 0805 | C1, C2, C3, C4, C5, C6, C7, C8, C9, C10, R1, R3, R5 | 0805_HV | C0805, R0805 | 13

PartNumber | RES, 1%, 0.5 W, 1206 | R2, R4 | 1206 | R1206 | 2

L78L05ACUTR | | U1 | STMicroelectronics _SOT-89-7098166_MFG | L78L05ACUTR | 1

AD8307ARZ | Low Cost, DC to 500 U2, U3 | | ADI- R- 8_M | AD8307 ARZ | 2
