witalis3/UA3REO-DDC-Transceiver/STM32/Src/sd.c

#include "hardware.h"
#if HRDW_HAS_SD

#include "INA226_PWR_monitor.h"
#include "audio_filters.h"
#include "fatfs.h"
#include "filemanager.h"
#include "fpga.h"
#include "functions.h"
#include "lcd.h"
#include "main.h"
#include "satellite.h"
#include "sd.h"
#include "system_menu.h"
#include "user_diskio.h"
#include "vocoder.h"

SRAM FATFS SDFatFs = {0};
sd_info_ptr sdinfo = {
    .type = 0,
    .SECTOR_COUNT = 0,
    .BLOCK_SIZE = 512,
    .CAPACITY = 0,
};
bool SD_RecordInProcess = false;
bool SD_RecordingCQmessage = false;
TRX_MODE rec_cqmessage_old_mode;
bool SD_PlayInProcess = false;
bool SD_PlayCQMessageInProcess = false;
bool SD_CommandInProcess = false;
bool SD_underrun = false;
bool SD_NeedStopRecord = false;
bool SD_NeedStopPlay = false;
bool SD_Play_Buffer_Ready = false;
uint32_t SD_Play_Buffer_Size = false;
uint32_t SD_RecordBufferIndex = 0;
bool SD_Present = false;
bool SD_BusyByUSB = false;
bool SD_USBCardReader = false;
uint32_t SD_Present_tryTime = 0;
bool SD_Mounted = false;
static SD_COMMAND SD_currentCommand = SDCOMM_IDLE;
uint32_t SDCOMM_WRITE_TO_FILE_partsize = 0;
void (*SDCOMM_WRITE_TO_FILE_callback)(void);
void (*SDCOMM_GET_LINES_COUNT_callback)(uint32_t count);

SRAM FIL File = {0};
SRAM static FILINFO fileInfo = {0};
SRAM static DIR dir = {0};
SRAM BYTE SD_workbuffer_A[FF_MAX_SS] = {0};
SRAM BYTE SD_workbuffer_B[FF_MAX_SS] = {0};
SRAM static WAV_header wav_hdr = {0};
BYTE SD_workbuffer_current = false; // false - fill A save B, true - fill B save A

static void SDCOMM_CHECKSD_handler(void);
static void SDCOMM_LISTROOT_handler(void);
static void SDCOMM_MKFS_handler(void);
static void SDCOMM_EXPORT_SETTINGS_handler(void);
static void SDCOMM_EXPORT_CALIBRATIONS_handler(void);
static void SDCOMM_IMPORT_SETTINGS_handler(void);
static bool SD_WRITE_SETT_LINE(char *name, uint64_t *value, SystemMenuType type);
static bool SD_WRITE_SETT_STRING(char *name, char *value);
static void SDCOMM_PARSE_SETT_LINE(char *line);
static bool SDCOMM_CREATE_RECORD_FILE_handler(void);
static bool SDCOMM_OPEN_PLAY_FILE_handler(void);
static bool SDCOMM_WRITE_PACKET_RECORD_FILE_handler(void);
static void SDCOMM_LIST_DIRECTORY_handler(void);
static void SDCOMM_DELETE_FILE_handler(void);
static void SDCOMM_READ_PLAY_FILE_handler(void);
static void SDCOMM_WRITE_TO_FILE_handler(void);
static void SDCOMM_GET_LINES_COUNT_handler(void);
static bool SDCOMM_CREATE_RECORD_FILE_main(char *filename, bool audio_rec);
static bool SDCOMM_CREATE_CQ_MESSAGE_FILE_handler(void);
static void SDCOMM_IMPORT_TLE_SATNAMES_handler(void);
static void SDCOMM_IMPORT_TLE_INFO_handler(void);

bool SD_isIdle(void) {
	if (SD_currentCommand == SDCOMM_IDLE) {
		return true;
	} else {
		return false;
	}
}

bool SD_doCommand(SD_COMMAND command, bool force) {
	if (SD_Mounted) {
		if (SD_CommandInProcess && !force) {
			println("SD command ovverrun: ", SD_currentCommand);
			SD_underrun = true;
		} else {
			SD_CommandInProcess = true;
			SD_currentCommand = command;
			return true;
		}
		return false;
	} else {
		TRX_ptt_soft = false;
		TRX_ptt_change();

		if (LCD_systemMenuOpened) {
			LCD_showInfo("SD card not found", true);
		} else {
			LCD_showTooltip("SD card not found");
		}
		return false;
	}
}

void SD_Process(void) {
	if (SD_BusyByUSB) {
		return;
	}

	// Init card
	if (!SD_Present && (HAL_GetTick() - SD_Present_tryTime) > SD_CARD_SCAN_INTERVAL) {
		SD_Present_tryTime = HAL_GetTick();
		SD_Mounted = false;

		if (disk_initialize(SDFatFs.pdrv) == RES_OK) {
			println("[OK] SD Card Inserted: ", (uint32_t)(sdinfo.CAPACITY / (uint64_t)1024 / (uint64_t)1024), "Mb");
			SD_Present = true;
			LCD_UpdateQuery.StatusInfoGUI = true;
		}
	}
	// Mount volume
	if (SD_Present && !SD_Mounted) {
		uint8_t res = f_mount(&SDFatFs, (TCHAR const *)USERPath, 1);
		if (res != FR_OK && res != FR_NO_FILESYSTEM) {
			println("[ERR] SD cannot be mounted: code ", res);
			SD_Present = false;
		} else {
			// println("[OK] SD mounted");
			SD_Mounted = true;
		}
	}
	// Do actions
	if (SD_Mounted) {
		if (SD_currentCommand != SDCOMM_IDLE) {
			SD_Present_tryTime = HAL_GetTick();
		}
		switch (SD_currentCommand) {
		case SDCOMM_IDLE:
			// check SD card inserted if idle
			if ((SD_Present_tryTime < HAL_GetTick()) && (HAL_GetTick() - SD_Present_tryTime) > SD_CARD_SCAN_INTERVAL && !SD_RecordInProcess) {
				SD_doCommand(SDCOMM_CHECK_SD, false);
				return;
			}
			//
			break;
		case SDCOMM_CHECK_SD:
			SDCOMM_CHECKSD_handler();
			break;
		case SDCOMM_LIST_ROOT:
			SDCOMM_LISTROOT_handler();
			break;
		case SDCOMM_FORMAT:
			SDCOMM_MKFS_handler();
			break;
		case SDCOMM_EXPORT_SETTINGS:
			SDCOMM_EXPORT_SETTINGS_handler();
			break;
		case SDCOMM_EXPORT_CALIBRATIONS:
			SDCOMM_EXPORT_CALIBRATIONS_handler();
			break;
		case SDCOMM_IMPORT_SETTINGS:
			SDCOMM_IMPORT_SETTINGS_handler();
			break;
		case SDCOMM_START_RECORD:
			SDCOMM_CREATE_RECORD_FILE_handler();
			break;
		case SDCOMM_PROCESS_RECORD:
			SDCOMM_WRITE_PACKET_RECORD_FILE_handler();
			break;
		case SDCOMM_CREATE_CQ_MESSAGE_FILE:
			SDCOMM_CREATE_CQ_MESSAGE_FILE_handler();
			break;
		case SDCOMM_LIST_DIRECTORY:
			SDCOMM_LIST_DIRECTORY_handler();
			break;
		case SDCOMM_DELETE_FILE:
			SDCOMM_DELETE_FILE_handler();
			break;
		case SDCOMM_START_PLAY:
			SDCOMM_OPEN_PLAY_FILE_handler();
			break;
		case SDCOMM_PROCESS_PLAY:
			SDCOMM_READ_PLAY_FILE_handler();
			break;
		case SDCOMM_FLASH_BIN:
			SDCOMM_FLASH_BIN_handler();
			break;
		case SDCOMM_FLASH_JIC:
			SDCOMM_FLASH_JIC_handler(true);
			break;
		case SDCOMM_WRITE_TO_FILE:
			SDCOMM_WRITE_TO_FILE_handler();
			break;
		case SDCOMM_GET_LINES_COUNT:
			SDCOMM_GET_LINES_COUNT_handler();
			break;
		case SDCOMM_IMPORT_TLE_SATNAMES:
			SDCOMM_IMPORT_TLE_SATNAMES_handler();
			break;
		case SDCOMM_IMPORT_TLE_INFO:
			SDCOMM_IMPORT_TLE_INFO_handler();
			break;
		}
		SD_CommandInProcess = false;
		SD_currentCommand = SDCOMM_IDLE;
	}
}

static void SDCOMM_IMPORT_TLE_INFO_handler(void) {
	if (f_open(&File, "tle.txt", FA_READ | FA_OPEN_EXISTING) == FR_OK) {

		uint32_t bytesreaded;
		uint32_t linesCount = 0;
		uint32_t nameIndex = 0;
		uint32_t lastSeek = 0;
		memset(SAT_TLE_NAMES, 0x00, sizeof(SAT_TLE_NAMES));
		FRESULT res;
		do {
			f_read(&File, SD_workbuffer_B, sizeof(SD_workbuffer_B), (void *)&bytesreaded);
			uint32_t prevNpos = 0;
			for (uint32_t i = 0; i < bytesreaded; i++) {
				if (SD_workbuffer_B[i] == '\n') {
					if (linesCount % 3 == 0 && nameIndex < SAT_TLE_MAXCOUNT) {
						if (nameIndex == sysmenu_sat_selected_index) {
							uint32_t size = i - prevNpos;
							memset(TRX.SAT_Name, 0x00, sizeof(TRX.SAT_Name));
							strncpy(TRX.SAT_Name, (char *)(SD_workbuffer_B + prevNpos), size > SAT_NAME_MAXLEN ? SAT_NAME_MAXLEN : size);
						}

						nameIndex++;
					}
					if (linesCount % 3 == 1 && (nameIndex == sysmenu_sat_selected_index + 1)) {
						uint32_t size = i - prevNpos;
						memset(TRX.SAT_TLE_Line1, 0x00, sizeof(TRX.SAT_TLE_Line1));
						strncpy(TRX.SAT_TLE_Line1, (char *)(SD_workbuffer_B + prevNpos), size > SAT_TLE_LINE_MAXLEN ? SAT_TLE_LINE_MAXLEN : size);
					}
					if (linesCount % 3 == 2 && (nameIndex == sysmenu_sat_selected_index + 1)) {
						uint32_t size = i - prevNpos;
						memset(TRX.SAT_TLE_Line2, 0x00, sizeof(TRX.SAT_TLE_Line2));
						strncpy(TRX.SAT_TLE_Line2, (char *)(SD_workbuffer_B + prevNpos), size > SAT_TLE_LINE_MAXLEN ? SAT_TLE_LINE_MAXLEN : size);
					}

					linesCount++;
					prevNpos = i + 1;
				}
			}
			if (bytesreaded == sizeof(SD_workbuffer_B)) { // read new block from last line
				lastSeek += prevNpos;
				println("Seek: ", lastSeek);
				f_lseek(&File, lastSeek);
			}
		} while (bytesreaded > 0 && res == FR_OK);

		println(TRX.SAT_Name);
		println(TRX.SAT_TLE_Line1);
		println(TRX.SAT_TLE_Line2);
		NeedSaveSettings = true;

		f_close(&File);
		sysmenu_sat_selectsat_menu_opened = false;
		LCD_UpdateQuery.SystemMenuRedraw = true;

		SAT_init();
	} else {
		LCD_showTooltip("SD error");
		SD_PlayInProcess = false;
		SD_Present = false;
		LCD_UpdateQuery.StatusInfoGUI = true;
		LCD_UpdateQuery.StatusInfoBar = true;
	}
}

static void SDCOMM_IMPORT_TLE_SATNAMES_handler(void) {
	if (f_open(&File, "tle.txt", FA_READ | FA_OPEN_EXISTING) == FR_OK) {

		uint32_t bytesreaded;
		uint32_t linesCount = 0;
		uint32_t nameIndex = 0;
		uint32_t lastSeek = 0;
		memset(SAT_TLE_NAMES, 0x00, sizeof(SAT_TLE_NAMES));
		FRESULT res;
		do {
			f_read(&File, SD_workbuffer_B, sizeof(SD_workbuffer_B), (void *)&bytesreaded);
			uint32_t prevNpos = 0;
			for (uint32_t i = 0; i < bytesreaded; i++) {
				if (SD_workbuffer_B[i] == '\n') {
					if (linesCount % 3 == 0 && nameIndex < SAT_TLE_MAXCOUNT) {
						uint32_t size = i - prevNpos;
						strncpy(SAT_TLE_NAMES[nameIndex], (char *)(SD_workbuffer_B + prevNpos), size > SAT_NAME_MAXLEN ? SAT_NAME_MAXLEN : size);
						println(nameIndex, " ", SAT_TLE_NAMES[nameIndex], size);
						nameIndex++;
					}

					linesCount++;
					prevNpos = i + 1;
				}
			}
			if (bytesreaded == sizeof(SD_workbuffer_B)) { // read new block from last line
				lastSeek += prevNpos;
				println("Seek: ", lastSeek);
				f_lseek(&File, lastSeek);
			}
		} while (bytesreaded > 0 && res == FR_OK);

		f_close(&File);
		LCD_UpdateQuery.SystemMenuRedraw = true;
	} else {
		LCD_showTooltip("SD error");
		SD_PlayInProcess = false;
		SD_Present = false;
		LCD_UpdateQuery.StatusInfoGUI = true;
		LCD_UpdateQuery.StatusInfoBar = true;
	}
}

static void SDCOMM_GET_LINES_COUNT_handler(void) {
	if (f_open(&File, (TCHAR *)SD_workbuffer_A, FA_READ | FA_OPEN_ALWAYS) == FR_OK) {
		uint32_t bytesreaded;
		uint32_t linesCount = 0;
		FRESULT res;
		do {
			f_read(&File, SD_workbuffer_B, sizeof(SD_workbuffer_B), (void *)&bytesreaded);
			for (uint32_t i = 0; i < bytesreaded; i++) {
				if (SD_workbuffer_B[i] == '\n') {
					linesCount++;
				}
			}
		} while (bytesreaded > 0 && res == FR_OK);

		f_close(&File);
		SDCOMM_GET_LINES_COUNT_callback(linesCount);
	} else {
		LCD_showTooltip("SD error");
		SD_PlayInProcess = false;
		SD_Present = false;
		LCD_UpdateQuery.StatusInfoGUI = true;
		LCD_UpdateQuery.StatusInfoBar = true;
	}
}

static void SDCOMM_WRITE_TO_FILE_handler(void) {
	if (f_open(&File, (TCHAR *)SD_workbuffer_A, FA_WRITE | FA_OPEN_APPEND) == FR_OK) {
		uint32_t byteswritten;
		FRESULT res = f_write(&File, SD_workbuffer_B, SDCOMM_WRITE_TO_FILE_partsize, (void *)&byteswritten);
		f_close(&File);
		if (res != FR_OK || byteswritten == 0) {
			println("SD file append error");
		} else {
			println("SD file data appended ", byteswritten);
			SDCOMM_WRITE_TO_FILE_callback();
		}
	} else {
		LCD_showTooltip("SD error");
		SD_PlayInProcess = false;
		SD_Present = false;
		LCD_UpdateQuery.StatusInfoGUI = true;
		LCD_UpdateQuery.StatusInfoBar = true;
	}
}

static void SDCOMM_DELETE_FILE_handler(void) {
	if (f_unlink((TCHAR *)SD_workbuffer_A) || f_unlink((TCHAR *)SD_workbuffer_A)) // two try'es
	{
		println("File deleted: ", (char *)SD_workbuffer_A);
		SD_doCommand(SDCOMM_LIST_DIRECTORY, true);
		SD_Process();
	} else {
		println("File delete error: ", (char *)SD_workbuffer_A);
	}
	LCD_redraw(false);
}

static void SDCOMM_LIST_DIRECTORY_handler(void) {
	FILEMANAGER_files_count = 0;
	uint16_t FILEMANAGER_files_added = 0;
	dma_memset(FILEMANAGER_LISTING, 0, sizeof(FILEMANAGER_LISTING));
	if (f_opendir(&dir, FILEMANAGER_CurrentPath) == FR_OK) {
		while (f_readdir(&dir, &fileInfo) == FR_OK && fileInfo.fname[0]) {
			if (fileInfo.fattrib & AM_DIR) {
				println("[DIR] ", fileInfo.fname);

				if (FILEMANAGER_files_startindex <= FILEMANAGER_files_count && FILEMANAGER_files_added < FILEMANAGER_LISTING_MAX_FILES) {
					strcat(FILEMANAGER_LISTING[FILEMANAGER_files_added], " [DIR] ");
					strncat(FILEMANAGER_LISTING[FILEMANAGER_files_added], fileInfo.fname, (FILEMANAGER_LISTING_MAX_FILELEN - 7));
					FILEMANAGER_files_added++;
				}
				FILEMANAGER_files_count++;
			}
		}
		f_closedir(&dir);

		f_opendir(&dir, FILEMANAGER_CurrentPath);
		while (f_readdir(&dir, &fileInfo) == FR_OK && fileInfo.fname[0]) {
			if (!(fileInfo.fattrib & AM_DIR)) {
				println("[FILE] ", fileInfo.fname);
				if (FILEMANAGER_files_startindex <= FILEMANAGER_files_count && FILEMANAGER_files_added < FILEMANAGER_LISTING_MAX_FILES) {
					strncat(FILEMANAGER_LISTING[FILEMANAGER_files_added], fileInfo.fname, (FILEMANAGER_LISTING_MAX_FILELEN));
					FILEMANAGER_files_added++;
				}
				FILEMANAGER_files_count++;
			}
		}
		f_closedir(&dir);
		println("read complete");

		qsort(FILEMANAGER_LISTING, FILEMANAGER_files_added, FILEMANAGER_LISTING_MAX_FILELEN + 1, (int (*)(const void *, const void *))strcmp);
	} else {
		LCD_showInfo("SD error", true);
		SYSMENU_eventCloseAllSystemMenu();
		SD_Present = false;
	}
	LCD_UpdateQuery.SystemMenuRedraw = true;
}

static void SDCOMM_CHECKSD_handler(void) {
	if (f_mount(&SDFatFs, (TCHAR const *)USERPath, 1) == FR_OK) {
		// println("[OK] Check SD");
	} else {
		// println("[ERR] Check SD");
		SD_RecordInProcess = false;
		SD_Present = false;
		LCD_UpdateQuery.StatusInfoGUI = true;
	}
}

static bool SDCOMM_CREATE_RECORD_FILE_handler(void) {
	char filename[64] = {0};
	RTC_TimeTypeDef sTime = {0};
	RTC_DateTypeDef sDate = {0};
	getLocalDateTime(&sDate, &sTime);

	f_mkdir("Recordings");
	sprintf(filename, "Recordings/rec-%02d.%02d.%02d-%02d.%02d.%02d-%llu.wav", sDate.Date, sDate.Month, sDate.Year, sTime.Hours, sTime.Minutes, sTime.Seconds, CurrentVFO->Freq);
	println(filename);
	return SDCOMM_CREATE_RECORD_FILE_main(filename, true);
}

static bool SDCOMM_CREATE_CQ_MESSAGE_FILE_handler(void) { return SDCOMM_CREATE_RECORD_FILE_main(SD_CQ_MESSAGE_FILE, false); }

static bool SDCOMM_CREATE_RECORD_FILE_main(char *filename, bool audio_rec) {
	RTC_TimeTypeDef sTime = {0};
	RTC_DateTypeDef sDate = {0};
	getLocalDateTime(&sDate, &sTime);
	if (f_open(&File, filename, FA_CREATE_ALWAYS | FA_WRITE) == FR_OK) {
		dma_memset(SD_workbuffer_A, 0x00, sizeof(SD_workbuffer_A));
		dma_memset(&wav_hdr, 0x00, sizeof(wav_hdr));
		// RIFF header
		wav_hdr.riffsig = 0x46464952;
		wav_hdr.filesize = sizeof(wav_hdr);
		wav_hdr.wavesig = 0x45564157;

		// format chunk
		wav_hdr.fmtsig = 0x20746D66;
		// wav_hdr.fmtsize		= 16;  //PCM
		wav_hdr.fmtsize = 0x14; // IMA-ADPCM
		// wav_hdr.type			= 1; //PCM
		wav_hdr.type = 0x11; // IMA-ADPCM
		wav_hdr.nch = 1;     // Mono
		wav_hdr.freq = 48000;
		// wav_hdr.rate			= 96000; //PCM 16bit
		wav_hdr.rate = (wav_hdr.freq * wav_hdr.nch * 256 / 505); // IMA-ADPCM byte rate, 48000 * Nch * 256 / 505
		// wav_hdr.block			= 2; //PCM
		wav_hdr.block = 256; // IMA-ADPCM block align, mono 256, stereo 512 */
		// wav_hdr.bits			= 16; //PCM
		wav_hdr.bits = 4;             // IMA-ADPCM
		wav_hdr.bytes_extra_data = 2; // IMA-ADPCM bytes extra data
		wav_hdr.extra_data = 505;     // IMA-ADPCM extra data

		// data chunk
		wav_hdr.datasig = 0x61746164;
		wav_hdr.datasize = 0;

		uint32_t byteswritten;
		f_write(&File, &wav_hdr, sizeof(wav_hdr), &byteswritten);

		VOCODER_SecondsTotal = 0;
		VOCODER_ProcessedSamples = 0;
		VOCODER_SecondsElapsedPrev = 0;
		VOCODER_SecondsElapsed = 0;

		if (audio_rec) {
			SD_RecordInProcess = true;
			LCD_UpdateQuery.StatusInfoBar = true;
			LCD_UpdateQuery.TopButtons = true;

#ifdef LCD_SMALL_INTERFACE
			LCD_showTooltip("Start record");
#else
			LCD_showTooltip("Start recording");
#endif
		} else {
			LCD_UpdateQuery.SystemMenuRedraw = true;
		}
		return true;
	} else {
		LCD_showTooltip("SD error");
		SD_RecordInProcess = false;
		SD_Present = false;
		LCD_UpdateQuery.StatusInfoGUI = true;
		LCD_UpdateQuery.StatusInfoBar = true;
	}
	if (!audio_rec) {
		LCD_UpdateQuery.SystemMenuRedraw = true;
	}
	return false;
}

static bool SDCOMM_WRITE_PACKET_RECORD_FILE_handler(void) {
	// reopen cq message
	static bool need_cqmess_reopen = true;
	if (SD_RecordingCQmessage) {
		if (need_cqmess_reopen) {
			f_open(&File, SD_CQ_MESSAGE_FILE, FA_WRITE | FA_OPEN_EXISTING);
			f_lseek(&File, sizeof(wav_hdr));
			need_cqmess_reopen = false;
		}
	}
	// write to SD
	uint32_t byteswritten;
	FRESULT res;
	if (SD_workbuffer_current) {
		res = f_write(&File, SD_workbuffer_A, sizeof(SD_workbuffer_A), (void *)&byteswritten);
	} else {
		res = f_write(&File, SD_workbuffer_B, sizeof(SD_workbuffer_B), (void *)&byteswritten);
	}
	if ((byteswritten == 0) || (res != FR_OK)) {
		SD_Present = false;
		SD_NeedStopRecord = false;
		SD_RecordInProcess = false;
		if (SD_RecordingCQmessage) {
			TRX_setMode(rec_cqmessage_old_mode, CurrentVFO);
			SD_RecordingCQmessage = false;
		}
		LCD_UpdateQuery.StatusInfoGUI = true;
		LCD_UpdateQuery.StatusInfoBar = true;
		LCD_UpdateQuery.SystemMenuRedraw = true;
		need_cqmess_reopen = true;
		LCD_showTooltip("SD error");
		return false;
	} else {
		// store size
		wav_hdr.datasize += byteswritten;
	}

	// stop record
	if (SD_NeedStopRecord) {
		SD_RecordInProcess = false;
		if (SD_RecordingCQmessage) {
			TRX_setMode(rec_cqmessage_old_mode, CurrentVFO);
			SD_RecordingCQmessage = false;
		}
		LCD_UpdateQuery.StatusInfoBar = true;
		LCD_UpdateQuery.SystemMenuRedraw = true;
		LCD_UpdateQuery.TopButtons = true;
		need_cqmess_reopen = true;
		LCD_showTooltip("Stop recording");

		// update file size
		f_truncate(&File);

		// update wav length
		f_lseek(&File, 0);
		f_write(&File, &wav_hdr, sizeof(wav_hdr), &byteswritten);

		f_close(&File);
		SD_NeedStopRecord = false;
		return true;
	}
	return true;
}

void SDCOMM_FLASH_BIN_handler(void) {
	if (f_open(&File, (TCHAR *)SD_workbuffer_A, FA_READ | FA_OPEN_EXISTING) == FR_OK) {
		dma_memset(SD_workbuffer_B, 0x00, sizeof(SD_workbuffer_B));
		println("[FLASH] File Opened");
		TRX.Mute = true;
		CODEC_CleanBuffer();

		// SCB_DisableICache();
		// SCB_DisableDCache();
		HAL_FLASH_OB_Unlock();
		HAL_FLASH_Unlock();
		println("[FLASH] Unlocked");

		FLASH_OBProgramInitTypeDef OBInit;
		OBInit.OptionType = OPTIONBYTE_WRP;
		OBInit.Banks = FLASH_BANK_2;
		OBInit.WRPState = OB_WRPSTATE_DISABLE;
		OBInit.WRPSector = OB_WRP_SECTOR_ALL;
		HAL_FLASHEx_OBProgram(&OBInit);
		if (HAL_FLASH_OB_Launch() != HAL_OK) {
			println("[FLASH] WP disable error");
			return;
		}
		println("[FLASH] WP disabled");

		__HAL_FLASH_CLEAR_FLAG(FLASH_FLAG_EOP | FLASH_FLAG_OPERR | FLASH_FLAG_WRPERR | FLASH_FLAG_PGSERR);
		FLASH_EraseInitTypeDef EraseInitStruct;
		EraseInitStruct.VoltageRange = FLASH_VOLTAGE_RANGE_3;
		EraseInitStruct.Sector = 0;
		EraseInitStruct.NbSectors = 8;
		EraseInitStruct.Banks = FLASH_BANK_2;
		EraseInitStruct.TypeErase = FLASH_TYPEERASE_MASSERASE;
		uint32_t SectorError = 0;
		LCD_showInfo("Erasing...", false);
		if (HAL_FLASHEx_Erase(&EraseInitStruct, &SectorError) != HAL_OK) {
			HAL_FLASH_Lock();
			LCD_showInfo("Flash erase error", true);
			return;
		}
		println("[FLASH] Erased");

		LCD_showInfo("Programming...", false);
		bool read_flag = true;
		uint32_t bytesreaded = 0;
		uint32_t LastPGAddress = 0x08100000;    // second bank
		const uint32_t flash_word_size = 8 * 4; // 8x 32bits words
		while (read_flag == true) {
			if (f_read(&File, SD_workbuffer_B, sizeof(SD_workbuffer_B), (void *)&bytesreaded) != FR_OK) {
				LCD_showInfo("File read error", true);
				return;
			}

			if (bytesreaded > 0) {
				for (int32_t block_addr = 0; block_addr < bytesreaded; block_addr += flash_word_size) {
					// println("[FLASH] Programming: ", LastPGAddress);
					// print_flush();

					uint8_t res = HAL_FLASH_Program(0, LastPGAddress, (uint32_t)&SD_workbuffer_B[block_addr]);
					if (res != HAL_OK) {
						LCD_showInfo("Flashing error", true);
						println("[FLASH] Flashing error: ", res, " ", HAL_FLASH_GetError());
						print_flush();
						block_addr -= flash_word_size; // retry
						LCD_showInfo("Programming...", false);
						continue;
					}

					// Check the first written value
					if (*(uint32_t *)LastPGAddress != *(uint32_t *)(SD_workbuffer_B + block_addr)) {
						LCD_showInfo("Flash Verify error", true);
						block_addr -= flash_word_size; // retry
						LCD_showInfo("Programming...", false);
						continue;
					}

					// println("[FLASH] Block flashed: ", LastPGAddress);
					// print_flush();

					LastPGAddress += flash_word_size;
				}

				// println("[FLASH] Flashed: ", LastPGAddress);
				// print_flush();
			} else {
				read_flag = false;
			}
		}

		LCD_showInfo("Flashed", true);

		// First part finished, swap banks

		// Get the Dual boot configuration status
		HAL_FLASHEx_OBGetConfig(&OBInit);
		// Get FLASH_WRP_SECTORS write protection status
		OBInit.Banks = FLASH_BANK_1;
		HAL_FLASHEx_OBGetConfig(&OBInit);

		uint32_t i = 0;
		if ((OBInit.USERConfig & OB_SWAP_BANK_ENABLE) == OB_SWAP_BANK_DISABLE) {
			// Swap to bank2
			// Set OB SWAP_BANK_OPT to swap Bank2
			OBInit.OptionType = OPTIONBYTE_USER;
			OBInit.USERType = OB_USER_SWAP_BANK;
			OBInit.USERConfig = OB_SWAP_BANK_ENABLE;
			HAL_FLASHEx_OBProgram(&OBInit);
			// Launch Option bytes loading
			// HAL_FLASH_OB_Launch();
			HAL_SuspendTick();
			__disable_irq();   // Disable all interrupts
			SysTick->CTRL = 0; // Disable Systick timer
			SysTick->VAL = 0;
			SysTick->LOAD = 0;
			HAL_RCC_DeInit();       // Set the clock to the default state
			for (i = 0; i < 5; i++) // Clear Interrupt Enable Register & Interrupt Pending Register
			{
				NVIC->ICER[i] = 0xFFFFFFFF;
				NVIC->ICPR[i] = 0xFFFFFFFF;
			}
			SET_BIT(FLASH->OPTCR, FLASH_OPTCR_OPTSTART);
			while (READ_BIT(FLASH->OPTSR_CUR, FLASH_OPTSR_OPT_BUSY) != 0U) {
			}
			// FLASH_OB_WaitForLastOperation(100);
			// HAL_NVIC_SystemReset();
			SCB->AIRCR = 0x05FA0004; // software reset
		} else {
			// Swap to bank1
			// Set OB SWAP_BANK_OPT to swap Bank1
			OBInit.OptionType = OPTIONBYTE_USER;
			OBInit.USERType = OB_USER_SWAP_BANK;
			OBInit.USERConfig = OB_SWAP_BANK_DISABLE;
			HAL_FLASHEx_OBProgram(&OBInit);
			// Launch Option bytes loading
			// HAL_FLASH_OB_Launch();
			HAL_SuspendTick();
			__disable_irq();   // Disable all interrupts
			SysTick->CTRL = 0; // Disable Systick timer
			SysTick->VAL = 0;
			SysTick->LOAD = 0;
			HAL_RCC_DeInit();       // Set the clock to the default state
			for (i = 0; i < 5; i++) // Clear Interrupt Enable Register & Interrupt Pending Register
			{
				NVIC->ICER[i] = 0xFFFFFFFF;
				NVIC->ICPR[i] = 0xFFFFFFFF;
			}
			SET_BIT(FLASH->OPTCR, FLASH_OPTCR_OPTSTART);
			while (READ_BIT(FLASH->OPTSR_CUR, FLASH_OPTSR_OPT_BUSY) != 0U) {
			}
			// FLASH_OB_WaitForLastOperation(100);
			// HAL_NVIC_SystemReset();
			SCB->AIRCR = 0x05FA0004; // software reset
		}

		println("[FLASH] Banks swapped");
		LCD_showInfo("Finished...", true);
	} else {
		LCD_showInfo("SD error", true);
		SD_PlayInProcess = false;
		SD_Present = false;
		LCD_UpdateQuery.StatusInfoGUI = true;
		LCD_UpdateQuery.StatusInfoBar = true;
	}
}

void SDCOMM_FLASH_JIC_handler(bool restart) {
	if (f_open(&File, (TCHAR *)SD_workbuffer_A, FA_READ | FA_OPEN_EXISTING) == FR_OK) {
		dma_memset(SD_workbuffer_A, 0x00, sizeof(SD_workbuffer_A));
		println("[FLASH] File Opened");
		TRX.Mute = true;
		CODEC_CleanBuffer();

		FPGA_bus_stop = true;
		HAL_Delay(100);
		if (!FPGA_is_present()) {
			return;
		}

		bool verify_error = true;
		while (verify_error) {
			LCD_showInfo("Erasing...", false);
			FPGA_spi_flash_erase();

			LCD_showInfo("Programming...", false);
			f_lseek(&File, FPGA_flash_file_offset);
			uint32_t fpga_flash_pos = 0;
			uint32_t bytesreaded = 0;
			bool read_in_progress = true;
			while (read_in_progress) {
				if (f_read(&File, SD_workbuffer_A, sizeof(SD_workbuffer_A), (void *)&bytesreaded) != FR_OK) {
					LCD_showInfo("File read error...", true);
					return;
				}

				if (bytesreaded > 0) {
					FPGA_spi_flash_write(fpga_flash_pos, (uint8_t *)SD_workbuffer_A, bytesreaded);
					fpga_flash_pos += bytesreaded;
					if (fpga_flash_pos >= FPGA_flash_size) {
						break;
					}
				} else {
					read_in_progress = false;
				}
			}

			LCD_showInfo("Verify...", false);
			f_lseek(&File, FPGA_flash_file_offset);
			fpga_flash_pos = 0;
			bytesreaded = 0;
			read_in_progress = true;
			while (read_in_progress) {
				if (f_read(&File, SD_workbuffer_A, sizeof(SD_workbuffer_A), (void *)&bytesreaded) != FR_OK) {
					LCD_showInfo("File read error...", true);
					return;
				}

				if (bytesreaded > 0) {
					verify_error = !FPGA_spi_flash_verify(fpga_flash_pos, (uint8_t *)SD_workbuffer_A, bytesreaded);
					fpga_flash_pos += bytesreaded;
					if (fpga_flash_pos >= FPGA_flash_size) {
						break;
					}
					if (verify_error) {
						break;
					}
				} else {
					read_in_progress = false;
				}
			}
		}

		f_close(&File);
		LCD_showInfo("Finished...", true);
		// HAL_NVIC_SystemReset();
		if (restart) {
			SCB->AIRCR = 0x05FA0004; // software reset
		}
	} else {
		LCD_showInfo("SD error", true);
		SD_PlayInProcess = false;
		SD_Present = false;
		LCD_UpdateQuery.StatusInfoGUI = true;
		LCD_UpdateQuery.StatusInfoBar = true;
	}
}

static bool SDCOMM_OPEN_PLAY_FILE_handler(void) {
	if (f_open(&File, (TCHAR *)SD_workbuffer_A, FA_READ | FA_OPEN_EXISTING) == FR_OK) {
		dma_memset(SD_workbuffer_A, 0x00, sizeof(SD_workbuffer_A));
		dma_memset(&wav_hdr, 0x00, sizeof(wav_hdr));

		// read header
		uint32_t bytesreaded;
		FRESULT res = f_read(&File, &wav_hdr, sizeof(wav_hdr), &bytesreaded);
		// println((TCHAR*)SD_workbuffer_A);
		// println(bytesreaded, " ", res);

		VOCODER_SecondsTotal = wav_hdr.datasize / SIZE_ADPCM_COMPRESSED_BLOCK * SIZE_ADPCM_BLOCK / TRX_SAMPLERATE;
		VOCODER_ProcessedSamples = 0;
		VOCODER_SecondsElapsedPrev = 0;
		VOCODER_SecondsElapsed = 0;

		SD_PlayInProcess = true;
		LCD_UpdateQuery.SystemMenuRedraw = true;
		return true;
	} else {
		LCD_showTooltip("SD error");
		SD_PlayInProcess = false;
		SD_Present = false;
		TRX_ptt_soft = false;
		TRX_ptt_change();
		LCD_UpdateQuery.StatusInfoGUI = true;
		LCD_UpdateQuery.StatusInfoBar = true;
	}
	return false;
}

static void SDCOMM_READ_PLAY_FILE_handler(void) {
	// read from SD
	uint32_t bytesreaded;
	FRESULT res;
	if (SD_workbuffer_current) {
		res = f_read(&File, SD_workbuffer_A, sizeof(SD_workbuffer_A), (void *)&bytesreaded);
	} else {
		res = f_read(&File, SD_workbuffer_B, sizeof(SD_workbuffer_B), (void *)&bytesreaded);
	}
	if ((bytesreaded == 0) || (res != FR_OK) || SD_NeedStopPlay) {
		// println(bytesreaded, " ", res, " ", (uint8_t)SD_NeedStopPlay);
		SD_PlayInProcess = false;
		if (SD_PlayCQMessageInProcess) {
			TRX_ptt_soft = false;
			TRX_ptt_change();
			SD_PlayCQMessageInProcess = false;
		}
		LCD_UpdateQuery.SystemMenuRedraw = true;
		println("Stop WAV playing");
		f_close(&File);
		SD_NeedStopPlay = false;
	} else {
		SD_Play_Buffer_Ready = true;
		SD_Play_Buffer_Size = bytesreaded;
	}
}

static bool SD_WRITE_SETT_LINE(char *name, uint64_t *value, SystemMenuType type) {
	uint32_t byteswritten;
	char valbuff[64] = {0};
	float32_t tmp_float = 0;

	dma_memset(SD_workbuffer_A, 0x00, sizeof(SD_workbuffer_A));

	strcat((char *)SD_workbuffer_A, name);
	strcat((char *)SD_workbuffer_A, " = ");
	switch (type) {
	case SYSMENU_BOOLEAN:
		sprintf(valbuff, "%u", (uint8_t)*value);
		break;
	case SYSMENU_B4:
	case SYSMENU_UINT8:
	case SYSMENU_ATU_I:
	case SYSMENU_ATU_C:
		sprintf(valbuff, "%u", (uint8_t)*value);
		break;
	case SYSMENU_ENUM:
		sprintf(valbuff, "%u", (uint8_t)*value);
		break;
	case SYSMENU_ENUMR:
		sprintf(valbuff, "%u", (uint8_t)*value);
		break;
	case SYSMENU_UINT16:
		sprintf(valbuff, "%u", (uint16_t)*value);
		break;
	case SYSMENU_UINT32:
		sprintf(valbuff, "%u", (uint32_t)*value);
		break;
	case SYSMENU_UINT64:
		sprintf(valbuff, "%llu", (uint64_t)*value);
		break;
	case SYSMENU_INT8:
		sprintf(valbuff, "%d", (int8_t)*value);
		break;
	case SYSMENU_INT16:
		sprintf(valbuff, "%d", (int16_t)*value);
		break;
	case SYSMENU_INT32:
		sprintf(valbuff, "%d", (int32_t)*value);
		break;
	case SYSMENU_FLOAT32:
	case SYSMENU_TIMEZONE:
		dma_memcpy(&tmp_float, value, sizeof(float32_t));
		sprintf(valbuff, "%.6f", (double)tmp_float);
		break;
	case SYSMENU_FUNCBUTTON:
		sprintf(valbuff, "%u", (uint8_t)*value);
		break;
	case SYSMENU_RUN:
	case SYSMENU_UINT32R:
	case SYSMENU_MENU:
	case SYSMENU_INFOLINE:
	case SYSMENU_NAVBUTTON:
		break;
	}
	strcat((char *)SD_workbuffer_A, valbuff);
	strcat((char *)SD_workbuffer_A, "\r\n");

	FRESULT res = f_write(&File, SD_workbuffer_A, strlen((char *)SD_workbuffer_A), (void *)&byteswritten);
	if ((byteswritten == 0) || (res != FR_OK)) {
		SD_Present = false;
		return false;
	}
	return true;
}

static bool SD_WRITE_SETT_STRING(char *name, char *value) {
	uint32_t byteswritten;

	dma_memset(SD_workbuffer_A, 0x00, sizeof(SD_workbuffer_A));

	strcat((char *)SD_workbuffer_A, name);
	strcat((char *)SD_workbuffer_A, " = ");
	strcat((char *)SD_workbuffer_A, value);
	strcat((char *)SD_workbuffer_A, "\r\n");

	FRESULT res = f_write(&File, SD_workbuffer_A, strlen((char *)SD_workbuffer_A), (void *)&byteswritten);
	if ((byteswritten == 0) || (res != FR_OK)) {
		SD_Present = false;
		return false;
	}
	return true;
}

static void SDCOMM_EXPORT_SETTINGS_handler(void) {
	LCD_showInfo("Exporting...", false);
	if (f_open(&File, (char *)SD_workbuffer_A, FA_CREATE_ALWAYS | FA_WRITE) == FR_OK) {
		// TRX
		bool res = SD_WRITE_SETT_LINE("TRX.VFO_A.Freq", (uint64_t *)&TRX.VFO_A.Freq, SYSMENU_UINT64);
		if (res) {
			SD_WRITE_SETT_LINE("TRX.VFO_A.Mode", (uint64_t *)&TRX.VFO_A.Mode, SYSMENU_UINT32);
			SD_WRITE_SETT_LINE("TRX.VFO_A.LPF_RX_Filter_Width", (uint64_t *)&TRX.VFO_A.LPF_RX_Filter_Width, SYSMENU_UINT32);
			SD_WRITE_SETT_LINE("TRX.VFO_A.LPF_TX_Filter_Width", (uint64_t *)&TRX.VFO_A.LPF_TX_Filter_Width, SYSMENU_UINT32);
			SD_WRITE_SETT_LINE("TRX.VFO_A.HPF_RX_Filter_Width", (uint64_t *)&TRX.VFO_A.HPF_RX_Filter_Width, SYSMENU_UINT32);
			SD_WRITE_SETT_LINE("TRX.VFO_A.HPF_TX_Filter_Width", (uint64_t *)&TRX.VFO_A.HPF_TX_Filter_Width, SYSMENU_UINT32);
			SD_WRITE_SETT_LINE("TRX.VFO_A.ManualNotchFilter", (uint64_t *)&TRX.VFO_A.ManualNotchFilter, SYSMENU_BOOLEAN);
			SD_WRITE_SETT_LINE("TRX.VFO_A.AutoNotchFilter", (uint64_t *)&TRX.VFO_A.AutoNotchFilter, SYSMENU_BOOLEAN);
			SD_WRITE_SETT_LINE("TRX.VFO_A.NotchFC", (uint64_t *)&TRX.VFO_A.NotchFC, SYSMENU_UINT32);
			SD_WRITE_SETT_LINE("TRX.VFO_A.DNR_Type", (uint64_t *)&TRX.VFO_A.DNR_Type, SYSMENU_UINT8);
			SD_WRITE_SETT_LINE("TRX.VFO_A.AGC", (uint64_t *)&TRX.VFO_A.AGC, SYSMENU_BOOLEAN);
			SD_WRITE_SETT_LINE("TRX.VFO_A.SQL", (uint64_t *)&TRX.VFO_A.SQL, SYSMENU_BOOLEAN);
			SD_WRITE_SETT_LINE("TRX.VFO_A.FM_SQL_threshold_dBm", (uint64_t *)&TRX.VFO_A.FM_SQL_threshold_dBm, SYSMENU_INT16);
			SD_WRITE_SETT_LINE("TRX.VFO_A.RepeaterMode", (uint64_t *)&TRX.VFO_A.RepeaterMode, SYSMENU_BOOLEAN);
			SD_WRITE_SETT_LINE("TRX.VFO_A.CW_LPF_Filter", (uint64_t *)&TRX.VFO_A.CW_LPF_Filter, SYSMENU_UINT16);
			SD_WRITE_SETT_LINE("TRX.VFO_A.DIGI_LPF_Filter", (uint64_t *)&TRX.VFO_A.DIGI_LPF_Filter, SYSMENU_UINT16);
			SD_WRITE_SETT_LINE("TRX.VFO_A.DIGI_HPF_Filter", (uint64_t *)&TRX.VFO_A.DIGI_HPF_Filter, SYSMENU_UINT16);
			SD_WRITE_SETT_LINE("TRX.VFO_A.SSB_LPF_RX_Filter", (uint64_t *)&TRX.VFO_A.SSB_LPF_RX_Filter, SYSMENU_UINT16);
			SD_WRITE_SETT_LINE("TRX.VFO_A.SSB_LPF_TX_Filter", (uint64_t *)&TRX.VFO_A.SSB_LPF_TX_Filter, SYSMENU_UINT16);
			SD_WRITE_SETT_LINE("TRX.VFO_A.SSB_HPF_RX_Filter", (uint64_t *)&TRX.VFO_A.SSB_HPF_RX_Filter, SYSMENU_UINT16);
			SD_WRITE_SETT_LINE("TRX.VFO_A.SSB_HPF_TX_Filter", (uint64_t *)&TRX.VFO_A.SSB_HPF_TX_Filter, SYSMENU_UINT16);
			SD_WRITE_SETT_LINE("TRX.VFO_A.AM_LPF_RX_Filter", (uint64_t *)&TRX.VFO_A.AM_LPF_RX_Filter, SYSMENU_UINT16);
			SD_WRITE_SETT_LINE("TRX.VFO_A.AM_LPF_TX_Filter", (uint64_t *)&TRX.VFO_A.AM_LPF_TX_Filter, SYSMENU_UINT16);
			SD_WRITE_SETT_LINE("TRX.VFO_A.FM_LPF_RX_Filter", (uint64_t *)&TRX.VFO_A.FM_LPF_RX_Filter, SYSMENU_UINT16);
			SD_WRITE_SETT_LINE("TRX.VFO_A.FM_LPF_TX_Filter", (uint64_t *)&TRX.VFO_A.FM_LPF_TX_Filter, SYSMENU_UINT16);
			SD_WRITE_SETT_LINE("TRX.VFO_A.FM_HPF_RX_Filter", (uint64_t *)&TRX.VFO_A.FM_HPF_RX_Filter, SYSMENU_UINT16);
			SD_WRITE_SETT_LINE("TRX.VFO_B.Freq", (uint64_t *)&TRX.VFO_B.Freq, SYSMENU_UINT64);
			SD_WRITE_SETT_LINE("TRX.VFO_B.Mode", (uint64_t *)&TRX.VFO_B.Mode, SYSMENU_UINT32);
			SD_WRITE_SETT_LINE("TRX.VFO_B.LPF_RX_Filter_Width", (uint64_t *)&TRX.VFO_B.LPF_RX_Filter_Width, SYSMENU_UINT32);
			SD_WRITE_SETT_LINE("TRX.VFO_B.LPF_TX_Filter_Width", (uint64_t *)&TRX.VFO_B.LPF_TX_Filter_Width, SYSMENU_UINT32);
			SD_WRITE_SETT_LINE("TRX.VFO_B.HPF_RX_Filter_Width", (uint64_t *)&TRX.VFO_B.HPF_RX_Filter_Width, SYSMENU_UINT32);
			SD_WRITE_SETT_LINE("TRX.VFO_B.HPF_TX_Filter_Width", (uint64_t *)&TRX.VFO_B.HPF_TX_Filter_Width, SYSMENU_UINT32);
			SD_WRITE_SETT_LINE("TRX.VFO_B.ManualNotchFilter", (uint64_t *)&TRX.VFO_B.ManualNotchFilter, SYSMENU_BOOLEAN);
			SD_WRITE_SETT_LINE("TRX.VFO_B.AutoNotchFilter", (uint64_t *)&TRX.VFO_B.AutoNotchFilter, SYSMENU_BOOLEAN);
			SD_WRITE_SETT_LINE("TRX.VFO_B.NotchFC", (uint64_t *)&TRX.VFO_B.NotchFC, SYSMENU_UINT32);
			SD_WRITE_SETT_LINE("TRX.VFO_B.DNR_Type", (uint64_t *)&TRX.VFO_B.DNR_Type, SYSMENU_UINT8);
			SD_WRITE_SETT_LINE("TRX.VFO_B.AGC", (uint64_t *)&TRX.VFO_B.AGC, SYSMENU_BOOLEAN);
			SD_WRITE_SETT_LINE("TRX.VFO_B.SQL", (uint64_t *)&TRX.VFO_B.SQL, SYSMENU_BOOLEAN);
			SD_WRITE_SETT_LINE("TRX.VFO_B.FM_SQL_threshold_dBm", (uint64_t *)&TRX.VFO_B.FM_SQL_threshold_dBm, SYSMENU_INT16);
			SD_WRITE_SETT_LINE("TRX.VFO_B.RepeaterMode", (uint64_t *)&TRX.VFO_B.RepeaterMode, SYSMENU_BOOLEAN);
			SD_WRITE_SETT_LINE("TRX.VFO_B.CW_LPF_Filter", (uint64_t *)&TRX.VFO_B.CW_LPF_Filter, SYSMENU_UINT16);
			SD_WRITE_SETT_LINE("TRX.VFO_B.DIGI_LPF_Filter", (uint64_t *)&TRX.VFO_B.DIGI_LPF_Filter, SYSMENU_UINT16);
			SD_WRITE_SETT_LINE("TRX.VFO_B.DIGI_HPF_Filter", (uint64_t *)&TRX.VFO_B.DIGI_HPF_Filter, SYSMENU_UINT16);
			SD_WRITE_SETT_LINE("TRX.VFO_B.SSB_LPF_RX_Filter", (uint64_t *)&TRX.VFO_B.SSB_LPF_RX_Filter, SYSMENU_UINT16);
			SD_WRITE_SETT_LINE("TRX.VFO_B.SSB_LPF_TX_Filter", (uint64_t *)&TRX.VFO_B.SSB_LPF_TX_Filter, SYSMENU_UINT16);
			SD_WRITE_SETT_LINE("TRX.VFO_B.SSB_HPF_RX_Filter", (uint64_t *)&TRX.VFO_B.SSB_HPF_RX_Filter, SYSMENU_UINT16);
			SD_WRITE_SETT_LINE("TRX.VFO_B.SSB_HPF_TX_Filter", (uint64_t *)&TRX.VFO_B.SSB_HPF_TX_Filter, SYSMENU_UINT16);
			SD_WRITE_SETT_LINE("TRX.VFO_B.AM_LPF_RX_Filter", (uint64_t *)&TRX.VFO_B.AM_LPF_RX_Filter, SYSMENU_UINT16);
			SD_WRITE_SETT_LINE("TRX.VFO_B.AM_LPF_TX_Filter", (uint64_t *)&TRX.VFO_B.AM_LPF_TX_Filter, SYSMENU_UINT16);
			SD_WRITE_SETT_LINE("TRX.VFO_B.FM_LPF_RX_Filter", (uint64_t *)&TRX.VFO_B.FM_LPF_RX_Filter, SYSMENU_UINT16);
			SD_WRITE_SETT_LINE("TRX.VFO_B.FM_LPF_TX_Filter", (uint64_t *)&TRX.VFO_B.FM_LPF_TX_Filter, SYSMENU_UINT16);
			SD_WRITE_SETT_LINE("TRX.VFO_B.FM_HPF_RX_Filter", (uint64_t *)&TRX.VFO_B.FM_HPF_RX_Filter, SYSMENU_UINT16);
			SD_WRITE_SETT_LINE("TRX.selected_vfo", (uint64_t *)&TRX.selected_vfo, SYSMENU_BOOLEAN);
			SD_WRITE_SETT_LINE("TRX.ADC_Driver", (uint64_t *)&TRX.ADC_Driver, SYSMENU_BOOLEAN);
			SD_WRITE_SETT_LINE("TRX.LNA", (uint64_t *)&TRX.LNA, SYSMENU_BOOLEAN);
			SD_WRITE_SETT_LINE("TRX.ATT", (uint64_t *)&TRX.ATT, SYSMENU_BOOLEAN);
			SD_WRITE_SETT_LINE("TRX.ATT_DB", (uint64_t *)&TRX.ATT_DB, SYSMENU_FLOAT32);
			SD_WRITE_SETT_LINE("TRX.ATT_STEP", (uint64_t *)&TRX.ATT_STEP, SYSMENU_UINT8);
			SD_WRITE_SETT_LINE("TRX.Fast", (uint64_t *)&TRX.Fast, SYSMENU_BOOLEAN);
			SD_WRITE_SETT_LINE("TRX.ADC_PGA", (uint64_t *)&TRX.ADC_PGA, SYSMENU_BOOLEAN);
			SD_WRITE_SETT_LINE("TRX.ANT_RX", (uint64_t *)&TRX.ANT_RX, SYSMENU_UINT8);
			SD_WRITE_SETT_LINE("TRX.ANT_TX", (uint64_t *)&TRX.ANT_TX, SYSMENU_UINT8);
			SD_WRITE_SETT_LINE("TRX.RF_Filters", (uint64_t *)&TRX.RF_Filters, SYSMENU_BOOLEAN);
			SD_WRITE_SETT_LINE("TRX.RF_Gain", (uint64_t *)&TRX.RF_Gain, SYSMENU_UINT8);
			SD_WRITE_SETT_LINE("TRX.RF_Gain_For_Each_Band", (uint64_t *)&TRX.RF_Gain_For_Each_Band, SYSMENU_BOOLEAN);
			SD_WRITE_SETT_LINE("TRX.RF_Gain_For_Each_Mode", (uint64_t *)&TRX.RF_Gain_For_Each_Mode, SYSMENU_BOOLEAN);
			SD_WRITE_SETT_LINE("TRX.ChannelMode", (uint64_t *)&TRX.ChannelMode, SYSMENU_BOOLEAN);
			SD_WRITE_SETT_LINE("TRX.SatMode", (uint64_t *)&TRX.SatMode, SYSMENU_BOOLEAN);
			SD_WRITE_SETT_LINE("TRX.REPEATER_Offset", (uint64_t *)&TRX.REPEATER_Offset, SYSMENU_INT16);
			SD_WRITE_SETT_LINE("TRX.RIT_Enabled", (uint64_t *)&TRX.RIT_Enabled, SYSMENU_BOOLEAN);
			SD_WRITE_SETT_LINE("TRX.XIT_Enabled", (uint64_t *)&TRX.XIT_Enabled, SYSMENU_BOOLEAN);
			SD_WRITE_SETT_LINE("TRX.FineRITTune", (uint64_t *)&TRX.FineRITTune, SYSMENU_BOOLEAN);
			SD_WRITE_SETT_LINE("TRX.RIT_INTERVAL", (uint64_t *)&TRX.RIT_INTERVAL, SYSMENU_UINT16);
			SD_WRITE_SETT_LINE("TRX.XIT_INTERVAL", (uint64_t *)&TRX.XIT_INTERVAL, SYSMENU_UINT16);
			SD_WRITE_SETT_LINE("TRX.TWO_SIGNAL_TUNE", (uint64_t *)&TRX.TWO_SIGNAL_TUNE, SYSMENU_BOOLEAN);
			SD_WRITE_SETT_LINE("TRX.SAMPLERATE_MAIN", (uint64_t *)&TRX.SAMPLERATE_MAIN, SYSMENU_UINT8);
			SD_WRITE_SETT_LINE("TRX.SAMPLERATE_FM", (uint64_t *)&TRX.SAMPLERATE_FM, SYSMENU_UINT8);
			SD_WRITE_SETT_LINE("TRX.FRQ_STEP_CW_Hz", (uint64_t *)&TRX.FRQ_STEP_CW_Hz, SYSMENU_UINT32);
			SD_WRITE_SETT_LINE("TRX.FRQ_STEP_SSB_Hz", (uint64_t *)&TRX.FRQ_STEP_SSB_Hz, SYSMENU_UINT32);
			SD_WRITE_SETT_LINE("TRX.FRQ_STEP_DIGI_Hz", (uint64_t *)&TRX.FRQ_STEP_DIGI_Hz, SYSMENU_UINT32);
			SD_WRITE_SETT_LINE("TRX.FRQ_STEP_AM_Hz", (uint64_t *)&TRX.FRQ_STEP_AM_Hz, SYSMENU_UINT32);
			SD_WRITE_SETT_LINE("TRX.FRQ_STEP_FM_Hz", (uint64_t *)&TRX.FRQ_STEP_FM_Hz, SYSMENU_UINT32);
			SD_WRITE_SETT_LINE("TRX.FRQ_STEP_WFM_Hz", (uint64_t *)&TRX.FRQ_STEP_WFM_Hz, SYSMENU_UINT32);
			SD_WRITE_SETT_LINE("TRX.FAST_STEP_Multiplier", (uint64_t *)&TRX.FAST_STEP_Multiplier, SYSMENU_UINT8);
			SD_WRITE_SETT_LINE("TRX.ENC2_STEP_Multiplier", (uint64_t *)&TRX.ENC2_STEP_Multiplier, SYSMENU_UINT8);
			SD_WRITE_SETT_LINE("TRX.NOTCH_STEP_Hz", (uint64_t *)&TRX.NOTCH_STEP_Hz, SYSMENU_FLOAT32);
			SD_WRITE_SETT_LINE("TRX.Debug_Type", (uint64_t *)&TRX.Debug_Type, SYSMENU_UINT8);
			SD_WRITE_SETT_LINE("TRX.DXCluster_Type", (uint64_t *)&TRX.DXCluster_Type, SYSMENU_UINT8);
			SD_WRITE_SETT_LINE("TRX.BandMapEnabled", (uint64_t *)&TRX.BandMapEnabled, SYSMENU_BOOLEAN);
			SD_WRITE_SETT_LINE("TRX.InputType_MAIN", (uint64_t *)&TRX.InputType_MAIN, SYSMENU_UINT8);
			SD_WRITE_SETT_LINE("TRX.InputType_DIGI", (uint64_t *)&TRX.InputType_DIGI, SYSMENU_UINT8);
			SD_WRITE_SETT_LINE("TRX.AutoGain", (uint64_t *)&TRX.AutoGain, SYSMENU_BOOLEAN);
			SD_WRITE_SETT_LINE("TRX.SPLIT_Enabled", (uint64_t *)&TRX.SPLIT_Enabled, SYSMENU_BOOLEAN);
			SD_WRITE_SETT_LINE("TRX.Split_Mode_Sync_Freq", (uint64_t *)&TRX.Split_Mode_Sync_Freq, SYSMENU_BOOLEAN);
			SD_WRITE_SETT_LINE("TRX.WOLF_Cluster", (uint64_t *)&TRX.WOLF_Cluster, SYSMENU_BOOLEAN);
			SD_WRITE_SETT_LINE("TRX.FREE_Tune", (uint64_t *)&TRX.FREE_Tune, SYSMENU_BOOLEAN);
			SD_WRITE_SETT_LINE("TRX.FT8_Auto_CQ", (uint64_t *)&TRX.FT8_Auto_CQ, SYSMENU_BOOLEAN);
#if HRDW_HAS_DUAL_RX
			SD_WRITE_SETT_LINE("TRX.Dual_RX", (uint64_t *)&TRX.Dual_RX, SYSMENU_BOOLEAN);
			SD_WRITE_SETT_LINE("TRX.Dual_RX_Type", (uint64_t *)&TRX.Dual_RX_Type, SYSMENU_UINT8);
			SD_WRITE_SETT_LINE("TRX.Dual_RX_AB_Balance", (uint64_t *)&TRX.Dual_RX_AB_Balance, SYSMENU_INT8);
#endif
			SD_WRITE_SETT_LINE("TRX.Encoder_Accelerate", (uint64_t *)&TRX.Encoder_Accelerate, SYSMENU_BOOLEAN);
			SD_WRITE_SETT_STRING("TRX.CALLSIGN", TRX.CALLSIGN);
			SD_WRITE_SETT_STRING("TRX.LOCATOR", TRX.LOCATOR);
			SD_WRITE_SETT_STRING("TRX.URSI_CODE", TRX.URSI_CODE);
			SD_WRITE_SETT_STRING("TRX.SAT_Name", TRX.SAT_Name);
			SD_WRITE_SETT_STRING("TRX.SAT_TLE_Line1", TRX.SAT_TLE_Line1);
			SD_WRITE_SETT_STRING("TRX.SAT_TLE_Line2", TRX.SAT_TLE_Line2);
			SD_WRITE_SETT_STRING("TRX.SAT_QTH_Lat", TRX.SAT_QTH_Lat);
			SD_WRITE_SETT_STRING("TRX.SAT_QTH_Lon", TRX.SAT_QTH_Lon);
			SD_WRITE_SETT_STRING("TRX.SAT_QTH_Alt", TRX.SAT_QTH_Alt);
			SD_WRITE_SETT_LINE("TRX.Custom_Transverter_Enabled", (uint64_t *)&TRX.Custom_Transverter_Enabled, SYSMENU_BOOLEAN);
			SD_WRITE_SETT_LINE("TRX.ATU_Enabled", (uint64_t *)&TRX.ATU_Enabled, SYSMENU_BOOLEAN);
			SD_WRITE_SETT_LINE("TRX.TUNER_Enabled", (uint64_t *)&TRX.TUNER_Enabled, SYSMENU_BOOLEAN);
			SD_WRITE_SETT_LINE("TRX.ATU_MEM_STEP_KHZ", (uint64_t *)&TRX.TUNER_Enabled, SYSMENU_UINT16);
			SD_WRITE_SETT_LINE("TRX.Transverter_2m", (uint64_t *)&TRX.Transverter_2m, SYSMENU_BOOLEAN);
			SD_WRITE_SETT_LINE("TRX.Transverter_70cm", (uint64_t *)&TRX.Transverter_70cm, SYSMENU_BOOLEAN);
			SD_WRITE_SETT_LINE("TRX.Transverter_23cm", (uint64_t *)&TRX.Transverter_23cm, SYSMENU_BOOLEAN);
			SD_WRITE_SETT_LINE("TRX.Transverter_13cm", (uint64_t *)&TRX.Transverter_13cm, SYSMENU_BOOLEAN);
			SD_WRITE_SETT_LINE("TRX.Transverter_6cm", (uint64_t *)&TRX.Transverter_6cm, SYSMENU_BOOLEAN);
			SD_WRITE_SETT_LINE("TRX.Transverter_3cm", (uint64_t *)&TRX.Transverter_3cm, SYSMENU_BOOLEAN);
			SD_WRITE_SETT_LINE("TRX.Transverter_QO100", (uint64_t *)&TRX.Transverter_QO100, SYSMENU_BOOLEAN);
			SD_WRITE_SETT_LINE("TRX.Transverter_1_2cm", (uint64_t *)&TRX.Transverter_1_2cm, SYSMENU_BOOLEAN);
			SD_WRITE_SETT_LINE("TRX.Auto_Input_Switch", (uint64_t *)&TRX.Auto_Input_Switch, SYSMENU_BOOLEAN);
			SD_WRITE_SETT_LINE("TRX.Auto_Snap", (uint64_t *)&TRX.Auto_Snap, SYSMENU_BOOLEAN);
			SD_WRITE_SETT_LINE("TRX.Full_Duplex", (uint64_t *)&TRX.Full_Duplex, SYSMENU_BOOLEAN);
			SD_WRITE_SETT_LINE("TRX.Digital_Pre_Distortion", (uint64_t *)&TRX.Digital_Pre_Distortion, SYSMENU_BOOLEAN);
			// AUDIO
			SD_WRITE_SETT_LINE("TRX.Volume", (uint64_t *)&TRX.Volume, SYSMENU_UINT16);
			SD_WRITE_SETT_LINE("TRX.Volume_Step", (uint64_t *)&TRX.Volume_Step, SYSMENU_UINT8);
			SD_WRITE_SETT_LINE("TRX.IF_Gain", (uint64_t *)&TRX.IF_Gain, SYSMENU_UINT8);
			SD_WRITE_SETT_LINE("TRX.AGC_Gain_target_SSB", (uint64_t *)&TRX.AGC_Gain_target_SSB, SYSMENU_INT8);
			SD_WRITE_SETT_LINE("TRX.AGC_Gain_target_CW", (uint64_t *)&TRX.AGC_Gain_target_CW, SYSMENU_INT8);
			SD_WRITE_SETT_LINE("TRX.MIC_Gain_SSB_DB", (uint64_t *)&TRX.MIC_Gain_SSB_DB, SYSMENU_FLOAT32);
			SD_WRITE_SETT_LINE("TRX.MIC_Gain_AM_DB", (uint64_t *)&TRX.MIC_Gain_AM_DB, SYSMENU_FLOAT32);
			SD_WRITE_SETT_LINE("TRX.MIC_Gain_FM_DB", (uint64_t *)&TRX.MIC_Gain_FM_DB, SYSMENU_FLOAT32);
			SD_WRITE_SETT_LINE("TRX.MIC_Boost", (uint64_t *)&TRX.MIC_Boost, SYSMENU_BOOLEAN);
			SD_WRITE_SETT_LINE("TRX.LINE_Volume", (uint64_t *)&TRX.LINE_Volume, SYSMENU_UINT8);
			SD_WRITE_SETT_LINE("TRX.CODEC_Out_Volume", (uint64_t *)&TRX.CODEC_Out_Volume, SYSMENU_UINT8);
			SD_WRITE_SETT_LINE("TRX.BluetoothAudio_Enabled", (uint64_t *)&TRX.BluetoothAudio_Enabled, SYSMENU_BOOLEAN);
			SD_WRITE_SETT_LINE("TRX.MIC_NOISE_GATE", (uint64_t *)&TRX.MIC_NOISE_GATE, SYSMENU_INT8);
			SD_WRITE_SETT_LINE("TRX.RX_EQ_P1", (uint64_t *)&TRX.RX_EQ_P1, SYSMENU_INT8);
			SD_WRITE_SETT_LINE("TRX.RX_EQ_P2", (uint64_t *)&TRX.RX_EQ_P2, SYSMENU_INT8);
			SD_WRITE_SETT_LINE("TRX.RX_EQ_P3", (uint64_t *)&TRX.RX_EQ_P3, SYSMENU_INT8);
			SD_WRITE_SETT_LINE("TRX.RX_EQ_P4", (uint64_t *)&TRX.RX_EQ_P4, SYSMENU_INT8);
			SD_WRITE_SETT_LINE("TRX.RX_EQ_P5", (uint64_t *)&TRX.RX_EQ_P5, SYSMENU_INT8);
			SD_WRITE_SETT_LINE("TRX.RX_EQ_P6", (uint64_t *)&TRX.RX_EQ_P6, SYSMENU_INT8);
			SD_WRITE_SETT_LINE("TRX.RX_EQ_P1_WFM", (uint64_t *)&TRX.RX_EQ_P1_WFM, SYSMENU_INT8);
			SD_WRITE_SETT_LINE("TRX.RX_EQ_P2_WFM", (uint64_t *)&TRX.RX_EQ_P2_WFM, SYSMENU_INT8);
			SD_WRITE_SETT_LINE("TRX.RX_EQ_P3_WFM", (uint64_t *)&TRX.RX_EQ_P3_WFM, SYSMENU_INT8);
			SD_WRITE_SETT_LINE("TRX.RX_EQ_P4_WFM", (uint64_t *)&TRX.RX_EQ_P4_WFM, SYSMENU_INT8);
			SD_WRITE_SETT_LINE("TRX.RX_EQ_P5_WFM", (uint64_t *)&TRX.RX_EQ_P5_WFM, SYSMENU_INT8);
			SD_WRITE_SETT_LINE("TRX.RX_EQ_P6_WFM", (uint64_t *)&TRX.RX_EQ_P6_WFM, SYSMENU_INT8);
			SD_WRITE_SETT_LINE("TRX.MIC_EQ_P1_SSB", (uint64_t *)&TRX.MIC_EQ_P1_SSB, SYSMENU_INT8);
			SD_WRITE_SETT_LINE("TRX.MIC_EQ_P2_SSB", (uint64_t *)&TRX.MIC_EQ_P2_SSB, SYSMENU_INT8);
			SD_WRITE_SETT_LINE("TRX.MIC_EQ_P3_SSB", (uint64_t *)&TRX.MIC_EQ_P3_SSB, SYSMENU_INT8);
			SD_WRITE_SETT_LINE("TRX.MIC_EQ_P4_SSB", (uint64_t *)&TRX.MIC_EQ_P4_SSB, SYSMENU_INT8);
			SD_WRITE_SETT_LINE("TRX.MIC_EQ_P5_SSB", (uint64_t *)&TRX.MIC_EQ_P5_SSB, SYSMENU_INT8);
			SD_WRITE_SETT_LINE("TRX.MIC_EQ_P6_SSB", (uint64_t *)&TRX.MIC_EQ_P6_SSB, SYSMENU_INT8);
			SD_WRITE_SETT_LINE("TRX.MIC_EQ_P1_AMFM", (uint64_t *)&TRX.MIC_EQ_P1_AMFM, SYSMENU_INT8);
			SD_WRITE_SETT_LINE("TRX.MIC_EQ_P2_AMFM", (uint64_t *)&TRX.MIC_EQ_P2_AMFM, SYSMENU_INT8);
			SD_WRITE_SETT_LINE("TRX.MIC_EQ_P3_AMFM", (uint64_t *)&TRX.MIC_EQ_P3_AMFM, SYSMENU_INT8);
			SD_WRITE_SETT_LINE("TRX.MIC_EQ_P4_AMFM", (uint64_t *)&TRX.MIC_EQ_P4_AMFM, SYSMENU_INT8);
			SD_WRITE_SETT_LINE("TRX.MIC_EQ_P5_AMFM", (uint64_t *)&TRX.MIC_EQ_P5_AMFM, SYSMENU_INT8);
			SD_WRITE_SETT_LINE("TRX.MIC_EQ_P6_AMFM", (uint64_t *)&TRX.MIC_EQ_P6_AMFM, SYSMENU_INT8);
			SD_WRITE_SETT_LINE("TRX.MIC_REVERBER", (uint64_t *)&TRX.MIC_REVERBER, SYSMENU_UINT8);
			SD_WRITE_SETT_LINE("TRX.DNR1_SNR_THRESHOLD", (uint64_t *)&TRX.DNR1_SNR_THRESHOLD, SYSMENU_UINT8);
			SD_WRITE_SETT_LINE("TRX.DNR2_SNR_THRESHOLD", (uint64_t *)&TRX.DNR2_SNR_THRESHOLD, SYSMENU_UINT8);
			SD_WRITE_SETT_LINE("TRX.DNR_AVERAGE", (uint64_t *)&TRX.DNR_AVERAGE, SYSMENU_UINT8);
			SD_WRITE_SETT_LINE("TRX.DNR_MINIMAL", (uint64_t *)&TRX.DNR_MINIMAL, SYSMENU_UINT8);
			SD_WRITE_SETT_LINE("TRX.NOISE_BLANKER1_THRESHOLD", (uint64_t *)&TRX.NOISE_BLANKER1_THRESHOLD, SYSMENU_UINT8);
			SD_WRITE_SETT_LINE("TRX.NOISE_BLANKER2_THRESHOLD", (uint64_t *)&TRX.NOISE_BLANKER2_THRESHOLD, SYSMENU_UINT8);
			SD_WRITE_SETT_LINE("TRX.NOISE_BLANKER1", (uint64_t *)&TRX.NOISE_BLANKER1, SYSMENU_BOOLEAN);
			SD_WRITE_SETT_LINE("TRX.NOISE_BLANKER2", (uint64_t *)&TRX.NOISE_BLANKER2, SYSMENU_BOOLEAN);
			SD_WRITE_SETT_LINE("TRX.RX_AGC_SSB_speed", (uint64_t *)&TRX.RX_AGC_SSB_speed, SYSMENU_UINT8);
			SD_WRITE_SETT_LINE("TRX.RX_AGC_CW_speed", (uint64_t *)&TRX.RX_AGC_CW_speed, SYSMENU_UINT8);
			SD_WRITE_SETT_LINE("TRX.RX_AGC_Max_gain", (uint64_t *)&TRX.RX_AGC_Max_gain, SYSMENU_UINT8);
			SD_WRITE_SETT_LINE("TRX.RX_AGC_Hold_Time", (uint64_t *)&TRX.RX_AGC_Hold_Time, SYSMENU_UINT16);
			SD_WRITE_SETT_LINE("TRX.RX_AGC_Hold_Limiter", (uint64_t *)&TRX.RX_AGC_Hold_Limiter, SYSMENU_UINT16);
			SD_WRITE_SETT_LINE("TRX.RX_AGC_Hold_Step_Up", (uint64_t *)&TRX.RX_AGC_Hold_Step_Up, SYSMENU_UINT16);
			SD_WRITE_SETT_LINE("TRX.RX_AGC_Hold_Step_Down", (uint64_t *)&TRX.RX_AGC_Hold_Step_Down, SYSMENU_UINT16);
			SD_WRITE_SETT_LINE("TRX.TX_Compressor_speed_SSB", (uint64_t *)&TRX.TX_Compressor_speed_SSB, SYSMENU_UINT8);
			SD_WRITE_SETT_LINE("TRX.TX_Compressor_maxgain_SSB", (uint64_t *)&TRX.TX_Compressor_maxgain_SSB, SYSMENU_UINT8);
			SD_WRITE_SETT_LINE("TRX.TX_Compressor_speed_AMFM", (uint64_t *)&TRX.TX_Compressor_speed_AMFM, SYSMENU_UINT8);
			SD_WRITE_SETT_LINE("TRX.TX_Compressor_maxgain_AMFM", (uint64_t *)&TRX.TX_Compressor_maxgain_AMFM, SYSMENU_UINT8);
			SD_WRITE_SETT_LINE("TRX.CW_LPF_Stages", (uint64_t *)&TRX.CW_LPF_Stages, SYSMENU_UINT8);
			SD_WRITE_SETT_LINE("TRX.SSB_LPF_Stages", (uint64_t *)&TRX.SSB_LPF_Stages, SYSMENU_UINT8);
			SD_WRITE_SETT_LINE("TRX.AMFM_LPF_Stages", (uint64_t *)&TRX.AMFM_LPF_Stages, SYSMENU_UINT8);
			SD_WRITE_SETT_LINE("TRX.Beeper", (uint64_t *)&TRX.Beeper, SYSMENU_BOOLEAN);
			SD_WRITE_SETT_LINE("TRX.CTCSS_Freq", (uint64_t *)&TRX.CTCSS_Freq, SYSMENU_FLOAT32);
			SD_WRITE_SETT_LINE("TRX.SELFHEAR_Volume", (uint64_t *)&TRX.SELFHEAR_Volume, SYSMENU_UINT8);
			SD_WRITE_SETT_LINE("TRX.FM_Stereo", (uint64_t *)&TRX.FM_Stereo, SYSMENU_BOOLEAN);
			SD_WRITE_SETT_LINE("TRX.FM_Stereo_Modulation", (uint64_t *)&TRX.FM_Stereo_Modulation, SYSMENU_UINT8);
			SD_WRITE_SETT_LINE("TRX.AGC_Spectral", (uint64_t *)&TRX.AGC_Spectral, SYSMENU_BOOLEAN);
			SD_WRITE_SETT_LINE("TRX.AGC_Threshold", (uint64_t *)&TRX.AGC_Threshold, SYSMENU_BOOLEAN);
			SD_WRITE_SETT_LINE("TRX.TX_CESSB", (uint64_t *)&TRX.TX_CESSB, SYSMENU_BOOLEAN);
			SD_WRITE_SETT_LINE("TRX.TX_CESSB_COMPRESS_DB", (uint64_t *)&TRX.TX_CESSB_COMPRESS_DB, SYSMENU_FLOAT32);
			SD_WRITE_SETT_LINE("TRX.VAD_THRESHOLD", (uint64_t *)&TRX.VAD_THRESHOLD, SYSMENU_UINT8);
			SD_WRITE_SETT_LINE("TRX.VOX", (uint64_t *)&TRX.VOX, SYSMENU_BOOLEAN);
			SD_WRITE_SETT_LINE("TRX.VOX_TIMEOUT", (uint64_t *)&TRX.VOX_TIMEOUT, SYSMENU_UINT16);
			SD_WRITE_SETT_LINE("TRX.VOX_THRESHOLD", (uint64_t *)&TRX.VOX_THRESHOLD, SYSMENU_INT8);
			SD_WRITE_SETT_LINE("TRX.RX_AUDIO_MODE", (uint64_t *)&TRX.RX_AUDIO_MODE, SYSMENU_UINT8);
			SD_WRITE_SETT_LINE("TRX.NOTCH_Filter_width", (uint64_t *)&TRX.NOTCH_Filter_width, SYSMENU_UINT16);
			// CW
			SD_WRITE_SETT_LINE("TRX.CW_Pitch", (uint64_t *)&TRX.CW_Pitch, SYSMENU_UINT16);
			SD_WRITE_SETT_LINE("TRX.CW_Key_timeout", (uint64_t *)&TRX.CW_Key_timeout, SYSMENU_UINT16);
			SD_WRITE_SETT_LINE("TRX.CW_SelfHear", (uint64_t *)&TRX.CW_SelfHear, SYSMENU_BOOLEAN);
			SD_WRITE_SETT_LINE("TRX.CW_KEYER", (uint64_t *)&TRX.CW_KEYER, SYSMENU_BOOLEAN);
			SD_WRITE_SETT_LINE("TRX.CW_OneSymbolMemory", (uint64_t *)&TRX.CW_OneSymbolMemory, SYSMENU_BOOLEAN);
			SD_WRITE_SETT_LINE("TRX.CW_KEYER_WPM", (uint64_t *)&TRX.CW_KEYER_WPM, SYSMENU_UINT16);
			SD_WRITE_SETT_LINE("TRX.CW_GaussFilter", (uint64_t *)&TRX.CW_GaussFilter, SYSMENU_BOOLEAN);
			SD_WRITE_SETT_LINE("TRX.CW_DotToDashRate", (uint64_t *)&TRX.CW_DotToDashRate, SYSMENU_FLOAT32);
			SD_WRITE_SETT_LINE("TRX.CW_Iambic", (uint64_t *)&TRX.CW_Iambic, SYSMENU_BOOLEAN);
			SD_WRITE_SETT_LINE("TRX.CW_Iambic_Type", (uint64_t *)&TRX.CW_Iambic_Type, SYSMENU_UINT8);
			SD_WRITE_SETT_LINE("TRX.CW_Invert", (uint64_t *)&TRX.CW_Invert, SYSMENU_BOOLEAN);
			SD_WRITE_SETT_LINE("TRX.Auto_CW_Mode", (uint64_t *)&TRX.Auto_CW_Mode, SYSMENU_BOOLEAN);
			SD_WRITE_SETT_LINE("TRX.CW_In_SSB", (uint64_t *)&TRX.CW_In_SSB, SYSMENU_BOOLEAN);
			SD_WRITE_SETT_LINE("TRX.CW_PTT_Type", (uint64_t *)&TRX.CW_PTT_Type, SYSMENU_UINT8);
			SD_WRITE_SETT_LINE("TRX.CW_EDGES_SMOOTH_MS", (uint64_t *)&TRX.CW_EDGES_SMOOTH_MS, SYSMENU_UINT8);
			SD_WRITE_SETT_STRING("TRX.CW_Macros_1", TRX.CW_Macros_1);
			SD_WRITE_SETT_STRING("TRX.CW_Macros_2", TRX.CW_Macros_2);
			SD_WRITE_SETT_STRING("TRX.CW_Macros_3", TRX.CW_Macros_3);
			SD_WRITE_SETT_STRING("TRX.CW_Macros_4", TRX.CW_Macros_4);
			SD_WRITE_SETT_STRING("TRX.CW_Macros_5", TRX.CW_Macros_5);
			SD_WRITE_SETT_STRING("TRX.CW_Macros_Name_1", TRX.CW_Macros_Name_1);
			SD_WRITE_SETT_STRING("TRX.CW_Macros_Name_2", TRX.CW_Macros_Name_2);
			SD_WRITE_SETT_STRING("TRX.CW_Macros_Name_3", TRX.CW_Macros_Name_3);
			SD_WRITE_SETT_STRING("TRX.CW_Macros_Name_4", TRX.CW_Macros_Name_4);
			SD_WRITE_SETT_STRING("TRX.CW_Macros_Name_5", TRX.CW_Macros_Name_5);
			// SCREEN
			SD_WRITE_SETT_LINE("TRX.ColorThemeId", (uint64_t *)&TRX.ColorThemeId, SYSMENU_UINT8);
			SD_WRITE_SETT_LINE("TRX.LayoutThemeId", (uint64_t *)&TRX.LayoutThemeId, SYSMENU_UINT8);
			SD_WRITE_SETT_LINE("TRX.FFT_Enabled", (uint64_t *)&TRX.FFT_Enabled, SYSMENU_BOOLEAN);
			SD_WRITE_SETT_LINE("TRX.FFT_Zoom", (uint64_t *)&TRX.FFT_Zoom, SYSMENU_UINT8);
			SD_WRITE_SETT_LINE("TRX.FFT_ZoomCW", (uint64_t *)&TRX.FFT_ZoomCW, SYSMENU_UINT8);
			SD_WRITE_SETT_LINE("TRX.LCD_Brightness", (uint64_t *)&TRX.LCD_Brightness, SYSMENU_UINT8);
			SD_WRITE_SETT_LINE("TRX.LCD_SleepTimeout", (uint64_t *)&TRX.LCD_SleepTimeout, SYSMENU_UINT16);
			SD_WRITE_SETT_LINE("TRX.FFT_Speed", (uint64_t *)&TRX.FFT_Speed, SYSMENU_UINT8);
			SD_WRITE_SETT_LINE("TRX.FFT_Sensitivity", (uint64_t *)&TRX.FFT_Sensitivity, SYSMENU_UINT8);
			SD_WRITE_SETT_LINE("TRX.FFT_Averaging", (uint64_t *)&TRX.FFT_Averaging, SYSMENU_UINT8);
			SD_WRITE_SETT_LINE("TRX.FFT_Window", (uint64_t *)&TRX.FFT_Window, SYSMENU_UINT8);
			SD_WRITE_SETT_LINE("TRX.FFT_Height", (uint64_t *)&TRX.FFT_Height, SYSMENU_UINT8);
			SD_WRITE_SETT_LINE("TRX.FFT_Style", (uint64_t *)&TRX.FFT_Style, SYSMENU_UINT8);
			SD_WRITE_SETT_LINE("TRX.FFT_BW_Style", (uint64_t *)&TRX.FFT_BW_Style, SYSMENU_UINT8);
			SD_WRITE_SETT_LINE("TRX.FFT_BW_Position", (uint64_t *)&TRX.FFT_BW_Position, SYSMENU_UINT8);
			SD_WRITE_SETT_LINE("TRX.FFT_Color", (uint64_t *)&TRX.FFT_Color, SYSMENU_UINT8);
			SD_WRITE_SETT_LINE("TRX.WTF_Color", (uint64_t *)&TRX.WTF_Color, SYSMENU_UINT8);
			SD_WRITE_SETT_LINE("TRX.FFT_Compressor", (uint64_t *)&TRX.FFT_Compressor, SYSMENU_BOOLEAN);
			SD_WRITE_SETT_LINE("TRX.WTF_Moving", (uint64_t *)&TRX.WTF_Moving, SYSMENU_BOOLEAN);
			SD_WRITE_SETT_LINE("TRX.FFT_FreqGrid", (uint64_t *)&TRX.FFT_FreqGrid, SYSMENU_INT8);
			SD_WRITE_SETT_LINE("TRX.FFT_dBmGrid", (uint64_t *)&TRX.FFT_dBmGrid, SYSMENU_BOOLEAN);
			SD_WRITE_SETT_LINE("TRX.FFT_Background", (uint64_t *)&TRX.FFT_Background, SYSMENU_BOOLEAN);
			SD_WRITE_SETT_LINE("TRX.FFT_Lens", (uint64_t *)&TRX.FFT_Lens, SYSMENU_BOOLEAN);
			SD_WRITE_SETT_LINE("TRX.FFT_HoldPeaks", (uint64_t *)&TRX.FFT_HoldPeaks, SYSMENU_BOOLEAN);
			SD_WRITE_SETT_LINE("TRX.FFT_3D", (uint64_t *)&TRX.FFT_3D, SYSMENU_UINT8);
			SD_WRITE_SETT_LINE("TRX.FFT_Automatic_Type", (uint64_t *)&TRX.FFT_Automatic_Type, SYSMENU_UINT8);
			SD_WRITE_SETT_LINE("TRX.FFT_ManualBottom", (uint64_t *)&TRX.FFT_ManualBottom, SYSMENU_INT16);
			SD_WRITE_SETT_LINE("TRX.FFT_ManualTop", (uint64_t *)&TRX.FFT_ManualTop, SYSMENU_INT16);
			SD_WRITE_SETT_LINE("TRX.FFT_DXCluster", (uint64_t *)&TRX.FFT_DXCluster, SYSMENU_BOOLEAN);
			SD_WRITE_SETT_LINE("TRX.FFT_DXCluster_Azimuth", (uint64_t *)&TRX.FFT_DXCluster_Azimuth, SYSMENU_BOOLEAN);
			SD_WRITE_SETT_LINE("TRX.FFT_DXCluster_Timeout", (uint64_t *)&TRX.FFT_DXCluster_Timeout, SYSMENU_UINT8);
			SD_WRITE_SETT_LINE("TRX.CenterSpectrumAfterIdle", (uint64_t *)&TRX.CenterSpectrumAfterIdle, SYSMENU_BOOLEAN);
			SD_WRITE_SETT_LINE("TRX.Show_Sec_VFO", (uint64_t *)&TRX.Show_Sec_VFO, SYSMENU_BOOLEAN);
			SD_WRITE_SETT_LINE("TRX.FFT_Scale_Type", (uint64_t *)&TRX.FFT_Scale_Type, SYSMENU_UINT8);
			SD_WRITE_SETT_LINE("TRX.EnableBottomNavigationButtons", (uint64_t *)&TRX.EnableBottomNavigationButtons, SYSMENU_BOOLEAN);
			// DECODER
			SD_WRITE_SETT_LINE("TRX.CW_Decoder", (uint64_t *)&TRX.CW_Decoder, SYSMENU_BOOLEAN);
			SD_WRITE_SETT_LINE("TRX.CW_Decoder_Threshold", (uint64_t *)&TRX.CW_Decoder_Threshold, SYSMENU_UINT8);
			SD_WRITE_SETT_LINE("TRX.RDS_Decoder", (uint64_t *)&TRX.RDS_Decoder, SYSMENU_BOOLEAN);
			SD_WRITE_SETT_LINE("TRX.RTTY_Speed", (uint64_t *)&TRX.RTTY_Speed, SYSMENU_UINT16);
			SD_WRITE_SETT_LINE("TRX.RTTY_Shift", (uint64_t *)&TRX.RTTY_Shift, SYSMENU_UINT16);
			SD_WRITE_SETT_LINE("TRX.RTTY_Freq", (uint64_t *)&TRX.RTTY_Freq, SYSMENU_UINT16);
			SD_WRITE_SETT_LINE("TRX.RTTY_StopBits", (uint64_t *)&TRX.RTTY_StopBits, SYSMENU_UINT8);
			SD_WRITE_SETT_LINE("TRX.RTTY_InvertBits", (uint64_t *)&TRX.RTTY_InvertBits, SYSMENU_BOOLEAN);
			// ADC
			SD_WRITE_SETT_LINE("TRX.ADC_Driver", (uint64_t *)&TRX.ADC_Driver, SYSMENU_BOOLEAN);
			SD_WRITE_SETT_LINE("TRX.ADC_PGA", (uint64_t *)&TRX.ADC_PGA, SYSMENU_BOOLEAN);
			SD_WRITE_SETT_LINE("TRX.ADC_RAND", (uint64_t *)&TRX.ADC_RAND, SYSMENU_BOOLEAN);
			SD_WRITE_SETT_LINE("TRX.ADC_SHDN", (uint64_t *)&TRX.ADC_SHDN, SYSMENU_BOOLEAN);
			SD_WRITE_SETT_LINE("TRX.ADC_DITH", (uint64_t *)&TRX.ADC_DITH, SYSMENU_BOOLEAN);
			// WIFI
			SD_WRITE_SETT_LINE("WIFI.Enabled", (uint64_t *)&WIFI.Enabled, SYSMENU_BOOLEAN);
			SD_WRITE_SETT_LINE("WIFI.CAT_Server", (uint64_t *)&WIFI.CAT_Server, SYSMENU_BOOLEAN);
			SD_WRITE_SETT_LINE("WIFI.Timezone", (uint64_t *)&WIFI.Timezone, SYSMENU_FLOAT32);
			SD_WRITE_SETT_STRING("WIFI.AP_1", WIFI.AP_1);
			SD_WRITE_SETT_STRING("WIFI.AP_2", WIFI.AP_2);
			SD_WRITE_SETT_STRING("WIFI.AP_3", WIFI.AP_3);
			SD_WRITE_SETT_STRING("WIFI.Password_1", WIFI.Password_1);
			SD_WRITE_SETT_STRING("WIFI.Password_2", WIFI.Password_2);
			SD_WRITE_SETT_STRING("WIFI.Password_3", WIFI.Password_3);
			SD_WRITE_SETT_STRING("WIFI.ALLQSO_TOKEN", WIFI.ALLQSO_TOKEN);
			SD_WRITE_SETT_STRING("WIFI.ALLQSO_LOGID", WIFI.ALLQSO_LOGID);
			// SERVICES
			SD_WRITE_SETT_LINE("TRX.SWR_CUSTOM_Begin", (uint64_t *)&TRX.SWR_CUSTOM_Begin, SYSMENU_UINT32);
			SD_WRITE_SETT_LINE("TRX.SWR_CUSTOM_End", (uint64_t *)&TRX.SWR_CUSTOM_End, SYSMENU_UINT32);
			SD_WRITE_SETT_LINE("TRX.SPEC_Begin", (uint64_t *)&TRX.SPEC_Begin, SYSMENU_UINT32);
			SD_WRITE_SETT_LINE("TRX.SPEC_End", (uint64_t *)&TRX.SPEC_End, SYSMENU_UINT32);
			SD_WRITE_SETT_LINE("TRX.SPEC_TopDBM", (uint64_t *)&TRX.SPEC_TopDBM, SYSMENU_INT16);
			SD_WRITE_SETT_LINE("TRX.SPEC_BottomDBM", (uint64_t *)&TRX.SPEC_BottomDBM, SYSMENU_INT16);
			SD_WRITE_SETT_LINE("TRX.WSPR_FREQ_OFFSET", (uint64_t *)&TRX.WSPR_FREQ_OFFSET, SYSMENU_INT16);
			SD_WRITE_SETT_LINE("TRX.WSPR_BANDS_160", (uint64_t *)&TRX.WSPR_BANDS_160, SYSMENU_BOOLEAN);
			SD_WRITE_SETT_LINE("TRX.WSPR_BANDS_80", (uint64_t *)&TRX.WSPR_BANDS_80, SYSMENU_BOOLEAN);
			SD_WRITE_SETT_LINE("TRX.WSPR_BANDS_40", (uint64_t *)&TRX.WSPR_BANDS_40, SYSMENU_BOOLEAN);
			SD_WRITE_SETT_LINE("TRX.WSPR_BANDS_30", (uint64_t *)&TRX.WSPR_BANDS_30, SYSMENU_BOOLEAN);
			SD_WRITE_SETT_LINE("TRX.WSPR_BANDS_20", (uint64_t *)&TRX.WSPR_BANDS_20, SYSMENU_BOOLEAN);
			SD_WRITE_SETT_LINE("TRX.WSPR_BANDS_17", (uint64_t *)&TRX.WSPR_BANDS_17, SYSMENU_BOOLEAN);
			SD_WRITE_SETT_LINE("TRX.WSPR_BANDS_15", (uint64_t *)&TRX.WSPR_BANDS_15, SYSMENU_BOOLEAN);
			SD_WRITE_SETT_LINE("TRX.WSPR_BANDS_12", (uint64_t *)&TRX.WSPR_BANDS_12, SYSMENU_BOOLEAN);
			SD_WRITE_SETT_LINE("TRX.WSPR_BANDS_10", (uint64_t *)&TRX.WSPR_BANDS_10, SYSMENU_BOOLEAN);
			SD_WRITE_SETT_LINE("TRX.WSPR_BANDS_6", (uint64_t *)&TRX.WSPR_BANDS_6, SYSMENU_BOOLEAN);
			SD_WRITE_SETT_LINE("TRX.WSPR_BANDS_2", (uint64_t *)&TRX.WSPR_BANDS_2, SYSMENU_BOOLEAN);

			// Func buttons settings
			char buff[64] = {0};
			for (uint8_t i = 0; i < (FUNCBUTTONS_PAGES * FUNCBUTTONS_ON_PAGE); i++) {
				sprintf(buff, "TRX.FuncButtons[%d]", i);
				SD_WRITE_SETT_LINE(buff, (uint64_t *)&TRX.FuncButtons[i], SYSMENU_UINT8);
			}

			// Bands settings
			for (uint8_t i = 0; i < BANDS_COUNT; i++) {
				sprintf(buff, "TRX.BANDS_SAVED_SETTINGS[%d].Freq", i);
				SD_WRITE_SETT_LINE(buff, (uint64_t *)&TRX.BANDS_SAVED_SETTINGS[i].Freq, SYSMENU_UINT64);
				sprintf(buff, "TRX.BANDS_SAVED_SETTINGS[%d].Mode", i);
				SD_WRITE_SETT_LINE(buff, (uint64_t *)&TRX.BANDS_SAVED_SETTINGS[i].Mode, SYSMENU_UINT8);
				sprintf(buff, "TRX.BANDS_SAVED_SETTINGS[%d].LNA", i);
				SD_WRITE_SETT_LINE(buff, (uint64_t *)&TRX.BANDS_SAVED_SETTINGS[i].LNA, SYSMENU_BOOLEAN);
				sprintf(buff, "TRX.BANDS_SAVED_SETTINGS[%d].ATT", i);
				SD_WRITE_SETT_LINE(buff, (uint64_t *)&TRX.BANDS_SAVED_SETTINGS[i].ATT, SYSMENU_BOOLEAN);
				sprintf(buff, "TRX.BANDS_SAVED_SETTINGS[%d].ATT_DB", i);
				SD_WRITE_SETT_LINE(buff, (uint64_t *)&TRX.BANDS_SAVED_SETTINGS[i].ATT_DB, SYSMENU_FLOAT32);
				sprintf(buff, "TRX.BANDS_SAVED_SETTINGS[%d].ANT_RX", i);
				SD_WRITE_SETT_LINE(buff, (uint64_t *)&TRX.BANDS_SAVED_SETTINGS[i].ANT_RX, SYSMENU_UINT8);
				sprintf(buff, "TRX.BANDS_SAVED_SETTINGS[%d].ANT_TX", i);
				SD_WRITE_SETT_LINE(buff, (uint64_t *)&TRX.BANDS_SAVED_SETTINGS[i].ANT_TX, SYSMENU_UINT8);
				sprintf(buff, "TRX.BANDS_SAVED_SETTINGS[%d].ADC_Driver", i);
				SD_WRITE_SETT_LINE(buff, (uint64_t *)&TRX.BANDS_SAVED_SETTINGS[i].ADC_Driver, SYSMENU_BOOLEAN);
				sprintf(buff, "TRX.BANDS_SAVED_SETTINGS[%d].SQL", i);
				SD_WRITE_SETT_LINE(buff, (uint64_t *)&TRX.BANDS_SAVED_SETTINGS[i].SQL, SYSMENU_BOOLEAN);
				sprintf(buff, "TRX.BANDS_SAVED_SETTINGS[%d].FM_SQL_threshold_dBm", i);
				SD_WRITE_SETT_LINE(buff, (uint64_t *)&TRX.BANDS_SAVED_SETTINGS[i].FM_SQL_threshold_dBm, SYSMENU_INT16);
				sprintf(buff, "TRX.BANDS_SAVED_SETTINGS[%d].ADC_PGA", i);
				SD_WRITE_SETT_LINE(buff, (uint64_t *)&TRX.BANDS_SAVED_SETTINGS[i].ADC_PGA, SYSMENU_BOOLEAN);
				sprintf(buff, "TRX.BANDS_SAVED_SETTINGS[%d].Fast", i);
				SD_WRITE_SETT_LINE(buff, (uint64_t *)&TRX.BANDS_SAVED_SETTINGS[i].Fast, SYSMENU_BOOLEAN);
				sprintf(buff, "TRX.BANDS_SAVED_SETTINGS[%d].DNR_Type", i);
				SD_WRITE_SETT_LINE(buff, (uint64_t *)&TRX.BANDS_SAVED_SETTINGS[i].DNR_Type, SYSMENU_UINT8);
				sprintf(buff, "TRX.BANDS_SAVED_SETTINGS[%d].AGC", i);
				SD_WRITE_SETT_LINE(buff, (uint64_t *)&TRX.BANDS_SAVED_SETTINGS[i].AGC, SYSMENU_BOOLEAN);
				sprintf(buff, "TRX.BANDS_SAVED_SETTINGS[%d].RepeaterMode", i);
				SD_WRITE_SETT_LINE(buff, (uint64_t *)&TRX.BANDS_SAVED_SETTINGS[i].RepeaterMode, SYSMENU_BOOLEAN);
				sprintf(buff, "TRX.BANDS_SAVED_SETTINGS[%d].SAMPLERATE", i);
				SD_WRITE_SETT_LINE(buff, (uint64_t *)&TRX.BANDS_SAVED_SETTINGS[i].SAMPLERATE, SYSMENU_UINT8);
				sprintf(buff, "TRX.BANDS_SAVED_SETTINGS[%d].VFO_A_CW_LPF_Filter", i);
				SD_WRITE_SETT_LINE(buff, (uint64_t *)&TRX.BANDS_SAVED_SETTINGS[i].VFO_A_CW_LPF_Filter, SYSMENU_UINT16);
				sprintf(buff, "TRX.BANDS_SAVED_SETTINGS[%d].VFO_A_SSB_LPF_RX_Filter", i);
				SD_WRITE_SETT_LINE(buff, (uint64_t *)&TRX.BANDS_SAVED_SETTINGS[i].VFO_A_SSB_LPF_RX_Filter, SYSMENU_UINT16);
				sprintf(buff, "TRX.BANDS_SAVED_SETTINGS[%d].VFO_A_AM_LPF_RX_Filter", i);
				SD_WRITE_SETT_LINE(buff, (uint64_t *)&TRX.BANDS_SAVED_SETTINGS[i].VFO_A_AM_LPF_RX_Filter, SYSMENU_UINT16);
				sprintf(buff, "TRX.BANDS_SAVED_SETTINGS[%d].VFO_A_FM_LPF_RX_Filter", i);
				SD_WRITE_SETT_LINE(buff, (uint64_t *)&TRX.BANDS_SAVED_SETTINGS[i].VFO_A_FM_LPF_RX_Filter, SYSMENU_UINT16);
				sprintf(buff, "TRX.BANDS_SAVED_SETTINGS[%d].VFO_B_CW_LPF_Filter", i);
				SD_WRITE_SETT_LINE(buff, (uint64_t *)&TRX.BANDS_SAVED_SETTINGS[i].VFO_B_CW_LPF_Filter, SYSMENU_UINT16);
				sprintf(buff, "TRX.BANDS_SAVED_SETTINGS[%d].VFO_B_SSB_LPF_RX_Filter", i);
				SD_WRITE_SETT_LINE(buff, (uint64_t *)&TRX.BANDS_SAVED_SETTINGS[i].VFO_B_SSB_LPF_RX_Filter, SYSMENU_UINT16);
				sprintf(buff, "TRX.BANDS_SAVED_SETTINGS[%d].VFO_B_AM_LPF_RX_Filter", i);
				SD_WRITE_SETT_LINE(buff, (uint64_t *)&TRX.BANDS_SAVED_SETTINGS[i].VFO_B_AM_LPF_RX_Filter, SYSMENU_UINT16);
				sprintf(buff, "TRX.BANDS_SAVED_SETTINGS[%d].VFO_B_FM_LPF_RX_Filter", i);
				SD_WRITE_SETT_LINE(buff, (uint64_t *)&TRX.BANDS_SAVED_SETTINGS[i].VFO_B_FM_LPF_RX_Filter, SYSMENU_UINT16);
			}

			// Memory channels settings
			for (uint8_t i = 0; i < MEMORY_CHANNELS_COUNT; i++) {
				sprintf(buff, "TRX.MEMORY_CHANNELS[%d].freq", i);
				SD_WRITE_SETT_LINE(buff, (uint64_t *)&CALIBRATE.MEMORY_CHANNELS[i].freq, SYSMENU_UINT64);
				sprintf(buff, "TRX.MEMORY_CHANNELS[%d].mode", i);
				SD_WRITE_SETT_LINE(buff, (uint64_t *)&CALIBRATE.MEMORY_CHANNELS[i].mode, SYSMENU_UINT8);
				sprintf(buff, "TRX.MEMORY_CHANNELS[%d].CTCSS_Freq", i);
				SD_WRITE_SETT_LINE(buff, (uint64_t *)&CALIBRATE.MEMORY_CHANNELS[i].CTCSS_Freq, SYSMENU_FLOAT32);
				sprintf(buff, "TRX.MEMORY_CHANNELS[%d].RepeaterMode", i);
				SD_WRITE_SETT_LINE(buff, (uint64_t *)&CALIBRATE.MEMORY_CHANNELS[i].RepeaterMode, SYSMENU_BOOLEAN);
				sprintf(buff, "TRX.MEMORY_CHANNELS[%d].name", i);
				SD_WRITE_SETT_STRING(buff, CALIBRATE.MEMORY_CHANNELS[i].name);
			}
		}

		if (!res) {
			LCD_showInfo("SD error", true);
		} else {
			LCD_showInfo("Settings export complete", true);
		}
	} else {
		LCD_showInfo("SD error", true);
		SD_Present = false;
	}
	f_close(&File);
}

static void SDCOMM_EXPORT_CALIBRATIONS_handler(void) {
	LCD_showInfo("Exporting...", false);
	if (f_open(&File, (char *)SD_workbuffer_A, FA_CREATE_ALWAYS | FA_WRITE) == FR_OK) {
		// TRX
		bool res = SD_WRITE_SETT_LINE("CALIBRATE.ENCODER_INVERT", (uint64_t *)&CALIBRATE.ENCODER_INVERT, SYSMENU_BOOLEAN);
		if (res) {
			// CALIBRATION
			SD_WRITE_SETT_LINE("CALIBRATE.ENCODER2_INVERT", (uint64_t *)&CALIBRATE.ENCODER2_INVERT, SYSMENU_BOOLEAN);
			SD_WRITE_SETT_LINE("CALIBRATE.ENCODER_DEBOUNCE", (uint64_t *)&CALIBRATE.ENCODER_DEBOUNCE, SYSMENU_UINT8);
			SD_WRITE_SETT_LINE("CALIBRATE.ENCODER2_DEBOUNCE", (uint64_t *)&CALIBRATE.ENCODER2_DEBOUNCE, SYSMENU_UINT8);
			SD_WRITE_SETT_LINE("CALIBRATE.ENCODER2_ON_FALLING", (uint64_t *)&CALIBRATE.ENCODER2_ON_FALLING, SYSMENU_BOOLEAN);
			SD_WRITE_SETT_LINE("CALIBRATE.ENCODER_SLOW_RATE", (uint64_t *)&CALIBRATE.ENCODER_SLOW_RATE, SYSMENU_UINT8);
			SD_WRITE_SETT_LINE("CALIBRATE.ENCODER_ACCELERATION", (uint64_t *)&CALIBRATE.ENCODER_ACCELERATION, SYSMENU_UINT8);
			SD_WRITE_SETT_LINE("CALIBRATE.RF_unit_type_2", (uint64_t *)&CALIBRATE.RF_unit_type, SYSMENU_UINT8);
			SD_WRITE_SETT_LINE("CALIBRATE.TangentType", (uint64_t *)&CALIBRATE.TangentType, SYSMENU_UINT8);
			SD_WRITE_SETT_LINE("CALIBRATE.CICFIR_GAINER_48K_3", (uint64_t *)&CALIBRATE.CICFIR_GAINER_48K_val, SYSMENU_UINT8);
			SD_WRITE_SETT_LINE("CALIBRATE.CICFIR_GAINER_96K_3", (uint64_t *)&CALIBRATE.CICFIR_GAINER_96K_val, SYSMENU_UINT8);
			SD_WRITE_SETT_LINE("CALIBRATE.CICFIR_GAINER_192K_3", (uint64_t *)&CALIBRATE.CICFIR_GAINER_192K_val, SYSMENU_UINT8);
			SD_WRITE_SETT_LINE("CALIBRATE.CICFIR_GAINER_384K_3", (uint64_t *)&CALIBRATE.CICFIR_GAINER_384K_val, SYSMENU_UINT8);
			SD_WRITE_SETT_LINE("CALIBRATE.DAC_GAINER_3", (uint64_t *)&CALIBRATE.DAC_GAINER_val, SYSMENU_UINT8);
			SD_WRITE_SETT_LINE("CALIBRATE.TXCICFIR_GAINER_3", (uint64_t *)&CALIBRATE.TXCICFIR_GAINER_val, SYSMENU_UINT8);
			SD_WRITE_SETT_LINE("CALIBRATE.DAC_driver_mode", (uint64_t *)&CALIBRATE.DAC_driver_mode, SYSMENU_UINT8);
			SD_WRITE_SETT_LINE("CALIBRATE.rf_out_power_2200m", (uint64_t *)&CALIBRATE.rf_out_power_2200m, SYSMENU_UINT8);
			SD_WRITE_SETT_LINE("CALIBRATE.rf_out_power_630m", (uint64_t *)&CALIBRATE.rf_out_power_630m, SYSMENU_UINT8);
			SD_WRITE_SETT_LINE("CALIBRATE.rf_out_power_160m", (uint64_t *)&CALIBRATE.rf_out_power_160m, SYSMENU_UINT8);
			SD_WRITE_SETT_LINE("CALIBRATE.rf_out_power_80m", (uint64_t *)&CALIBRATE.rf_out_power_80m, SYSMENU_UINT8);
			SD_WRITE_SETT_LINE("CALIBRATE.rf_out_power_60m", (uint64_t *)&CALIBRATE.rf_out_power_60m, SYSMENU_UINT8);
			SD_WRITE_SETT_LINE("CALIBRATE.rf_out_power_40m", (uint64_t *)&CALIBRATE.rf_out_power_40m, SYSMENU_UINT8);
			SD_WRITE_SETT_LINE("CALIBRATE.rf_out_power_30m", (uint64_t *)&CALIBRATE.rf_out_power_30m, SYSMENU_UINT8);
			SD_WRITE_SETT_LINE("CALIBRATE.rf_out_power_20m", (uint64_t *)&CALIBRATE.rf_out_power_20m, SYSMENU_UINT8);
			SD_WRITE_SETT_LINE("CALIBRATE.rf_out_power_17m", (uint64_t *)&CALIBRATE.rf_out_power_17m, SYSMENU_UINT8);
			SD_WRITE_SETT_LINE("CALIBRATE.rf_out_power_15m", (uint64_t *)&CALIBRATE.rf_out_power_15m, SYSMENU_UINT8);
			SD_WRITE_SETT_LINE("CALIBRATE.rf_out_power_12m", (uint64_t *)&CALIBRATE.rf_out_power_12m, SYSMENU_UINT8);
			SD_WRITE_SETT_LINE("CALIBRATE.rf_out_power_cb", (uint64_t *)&CALIBRATE.rf_out_power_cb, SYSMENU_UINT8);
			SD_WRITE_SETT_LINE("CALIBRATE.rf_out_power_10m", (uint64_t *)&CALIBRATE.rf_out_power_10m, SYSMENU_UINT8);
			SD_WRITE_SETT_LINE("CALIBRATE.rf_out_power_6m", (uint64_t *)&CALIBRATE.rf_out_power_6m, SYSMENU_UINT8);
			SD_WRITE_SETT_LINE("CALIBRATE.rf_out_power_4m", (uint64_t *)&CALIBRATE.rf_out_power_4m, SYSMENU_UINT8);
			SD_WRITE_SETT_LINE("CALIBRATE.rf_out_power_2m", (uint64_t *)&CALIBRATE.rf_out_power_2m, SYSMENU_UINT8);
			SD_WRITE_SETT_LINE("CALIBRATE.rf_out_power_70cm", (uint64_t *)&CALIBRATE.rf_out_power_70cm, SYSMENU_UINT8);
			SD_WRITE_SETT_LINE("CALIBRATE.rf_out_power_23cm", (uint64_t *)&CALIBRATE.rf_out_power_23cm, SYSMENU_UINT8);
			SD_WRITE_SETT_LINE("CALIBRATE.rf_out_power_13cm", (uint64_t *)&CALIBRATE.rf_out_power_13cm, SYSMENU_UINT8);
			SD_WRITE_SETT_LINE("CALIBRATE.rf_out_power_6cm", (uint64_t *)&CALIBRATE.rf_out_power_6cm, SYSMENU_UINT8);
			SD_WRITE_SETT_LINE("CALIBRATE.rf_out_power_3cm", (uint64_t *)&CALIBRATE.rf_out_power_3cm, SYSMENU_UINT8);
			SD_WRITE_SETT_LINE("CALIBRATE.rf_out_power_QO100", (uint64_t *)&CALIBRATE.rf_out_power_QO100, SYSMENU_UINT8);
			SD_WRITE_SETT_LINE("CALIBRATE.rf_out_power_1_2cm", (uint64_t *)&CALIBRATE.rf_out_power_1_2cm, SYSMENU_UINT8);
			SD_WRITE_SETT_LINE("CALIBRATE.smeter_calibration_hf", (uint64_t *)&CALIBRATE.smeter_calibration_hf, SYSMENU_INT16);
			SD_WRITE_SETT_LINE("CALIBRATE.smeter_calibration_vhf", (uint64_t *)&CALIBRATE.smeter_calibration_vhf, SYSMENU_INT16);
			SD_WRITE_SETT_LINE("CALIBRATE.RFU_LPF_END", (uint64_t *)&CALIBRATE.RFU_LPF_END, SYSMENU_UINT32);
			SD_WRITE_SETT_LINE("CALIBRATE.RFU_BPF_0_START", (uint64_t *)&CALIBRATE.RFU_BPF_0_START, SYSMENU_UINT32);
			SD_WRITE_SETT_LINE("CALIBRATE.RFU_BPF_0_END", (uint64_t *)&CALIBRATE.RFU_BPF_0_END, SYSMENU_UINT32);
			SD_WRITE_SETT_LINE("CALIBRATE.RFU_BPF_1_START", (uint64_t *)&CALIBRATE.RFU_BPF_1_START, SYSMENU_UINT32);
			SD_WRITE_SETT_LINE("CALIBRATE.RFU_BPF_1_END", (uint64_t *)&CALIBRATE.RFU_BPF_1_END, SYSMENU_UINT32);
			SD_WRITE_SETT_LINE("CALIBRATE.RFU_BPF_2_START", (uint64_t *)&CALIBRATE.RFU_BPF_2_START, SYSMENU_UINT32);
			SD_WRITE_SETT_LINE("CALIBRATE.RFU_BPF_2_END", (uint64_t *)&CALIBRATE.RFU_BPF_2_END, SYSMENU_UINT32);
			SD_WRITE_SETT_LINE("CALIBRATE.RFU_BPF_3_START", (uint64_t *)&CALIBRATE.RFU_BPF_3_START, SYSMENU_UINT32);
			SD_WRITE_SETT_LINE("CALIBRATE.RFU_BPF_3_END", (uint64_t *)&CALIBRATE.RFU_BPF_3_END, SYSMENU_UINT32);
			SD_WRITE_SETT_LINE("CALIBRATE.RFU_BPF_4_START", (uint64_t *)&CALIBRATE.RFU_BPF_4_START, SYSMENU_UINT32);
			SD_WRITE_SETT_LINE("CALIBRATE.RFU_BPF_4_END", (uint64_t *)&CALIBRATE.RFU_BPF_4_END, SYSMENU_UINT32);
			SD_WRITE_SETT_LINE("CALIBRATE.RFU_BPF_5_START", (uint64_t *)&CALIBRATE.RFU_BPF_5_START, SYSMENU_UINT32);
			SD_WRITE_SETT_LINE("CALIBRATE.RFU_BPF_5_END", (uint64_t *)&CALIBRATE.RFU_BPF_5_END, SYSMENU_UINT32);
			SD_WRITE_SETT_LINE("CALIBRATE.RFU_BPF_6_START", (uint64_t *)&CALIBRATE.RFU_BPF_6_START, SYSMENU_UINT32);
			SD_WRITE_SETT_LINE("CALIBRATE.RFU_BPF_6_END", (uint64_t *)&CALIBRATE.RFU_BPF_6_END, SYSMENU_UINT32);
			SD_WRITE_SETT_LINE("CALIBRATE.RFU_BPF_7_START", (uint64_t *)&CALIBRATE.RFU_BPF_7_START, SYSMENU_UINT32);
			SD_WRITE_SETT_LINE("CALIBRATE.RFU_BPF_7_END", (uint64_t *)&CALIBRATE.RFU_BPF_7_END, SYSMENU_UINT32);
			SD_WRITE_SETT_LINE("CALIBRATE.RFU_BPF_8_START", (uint64_t *)&CALIBRATE.RFU_BPF_8_START, SYSMENU_UINT32);
			SD_WRITE_SETT_LINE("CALIBRATE.RFU_BPF_8_END", (uint64_t *)&CALIBRATE.RFU_BPF_8_END, SYSMENU_UINT32);
			SD_WRITE_SETT_LINE("CALIBRATE.RFU_HPF_START", (uint64_t *)&CALIBRATE.RFU_HPF_START, SYSMENU_UINT32);
			SD_WRITE_SETT_LINE("CALIBRATE.SWR_FWD_Calibration_HF", (uint64_t *)&CALIBRATE.SWR_FWD_Calibration_HF, SYSMENU_FLOAT32);
			SD_WRITE_SETT_LINE("CALIBRATE.SWR_BWD_Calibration_HF", (uint64_t *)&CALIBRATE.SWR_BWD_Calibration_HF, SYSMENU_FLOAT32);
			SD_WRITE_SETT_LINE("CALIBRATE.SWR_FWD_Calibration_6M", (uint64_t *)&CALIBRATE.SWR_FWD_Calibration_6M, SYSMENU_FLOAT32);
			SD_WRITE_SETT_LINE("CALIBRATE.SWR_BWD_Calibration_6M", (uint64_t *)&CALIBRATE.SWR_BWD_Calibration_6M, SYSMENU_FLOAT32);
			SD_WRITE_SETT_LINE("CALIBRATE.SWR_FWD_Calibration_VHF", (uint64_t *)&CALIBRATE.SWR_FWD_Calibration_VHF, SYSMENU_FLOAT32);
			SD_WRITE_SETT_LINE("CALIBRATE.SWR_BWD_Calibration_VHF", (uint64_t *)&CALIBRATE.SWR_BWD_Calibration_VHF, SYSMENU_FLOAT32);
			SD_WRITE_SETT_LINE("CALIBRATE.TCXO_frequency", (uint64_t *)&CALIBRATE.TCXO_frequency, SYSMENU_UINT16);
			SD_WRITE_SETT_LINE("CALIBRATE.VCXO_correction", (uint64_t *)&CALIBRATE.VCXO_correction, SYSMENU_INT16);
			SD_WRITE_SETT_LINE("CALIBRATE.MAX_ChargePump_Freq", (uint64_t *)&CALIBRATE.MAX_ChargePump_Freq, SYSMENU_UINT16);
			SD_WRITE_SETT_LINE("CALIBRATE.FAN_MEDIUM_START", (uint64_t *)&CALIBRATE.FAN_MEDIUM_START, SYSMENU_UINT8);
			SD_WRITE_SETT_LINE("CALIBRATE.FAN_MEDIUM_STOP", (uint64_t *)&CALIBRATE.FAN_MEDIUM_STOP, SYSMENU_UINT8);
			SD_WRITE_SETT_LINE("CALIBRATE.FAN_FULL_START", (uint64_t *)&CALIBRATE.FAN_FULL_START, SYSMENU_UINT8);
			SD_WRITE_SETT_LINE("CALIBRATE.FAN_Medium_speed", (uint64_t *)&CALIBRATE.FAN_Medium_speed, SYSMENU_UINT8);
			SD_WRITE_SETT_LINE("CALIBRATE.TRX_MAX_RF_TEMP", (uint64_t *)&CALIBRATE.TRX_MAX_RF_TEMP, SYSMENU_UINT8);
			SD_WRITE_SETT_LINE("CALIBRATE.TRX_MAX_SWR", (uint64_t *)&CALIBRATE.TRX_MAX_SWR, SYSMENU_UINT8);
			SD_WRITE_SETT_LINE("CALIBRATE.FM_DEVIATION_SCALE", (uint64_t *)&CALIBRATE.FM_DEVIATION_SCALE, SYSMENU_UINT8);
			SD_WRITE_SETT_LINE("CALIBRATE.SSB_POWER_ADDITION", (uint64_t *)&CALIBRATE.SSB_POWER_ADDITION, SYSMENU_UINT8);
			SD_WRITE_SETT_LINE("CALIBRATE.AM_MODULATION_INDEX", (uint64_t *)&CALIBRATE.AM_MODULATION_INDEX, SYSMENU_UINT8);
			SD_WRITE_SETT_LINE("CALIBRATE.MAX_RF_POWER_ON_METER", (uint64_t *)&CALIBRATE.MAX_RF_POWER_ON_METER, SYSMENU_UINT8);
			SD_WRITE_SETT_LINE("CALIBRATE.TUNE_MAX_POWER", (uint64_t *)&CALIBRATE.TUNE_MAX_POWER, SYSMENU_UINT8);
			SD_WRITE_SETT_LINE("CALIBRATE.RTC_Coarse_Calibration", (uint64_t *)&CALIBRATE.RTC_Coarse_Calibration, SYSMENU_UINT8);
			SD_WRITE_SETT_LINE("CALIBRATE.RTC_Calibration", (uint64_t *)&CALIBRATE.RTC_Calibration, SYSMENU_INT16);
			SD_WRITE_SETT_LINE("CALIBRATE.EXT_2200m", (uint64_t *)&CALIBRATE.EXT_2200m, SYSMENU_UINT8);
			SD_WRITE_SETT_LINE("CALIBRATE.EXT_630m", (uint64_t *)&CALIBRATE.EXT_630m, SYSMENU_UINT8);
			SD_WRITE_SETT_LINE("CALIBRATE.EXT_160m", (uint64_t *)&CALIBRATE.EXT_160m, SYSMENU_UINT8);
			SD_WRITE_SETT_LINE("CALIBRATE.EXT_80m", (uint64_t *)&CALIBRATE.EXT_80m, SYSMENU_UINT8);
			SD_WRITE_SETT_LINE("CALIBRATE.EXT_60m", (uint64_t *)&CALIBRATE.EXT_60m, SYSMENU_UINT8);
			SD_WRITE_SETT_LINE("CALIBRATE.EXT_40m", (uint64_t *)&CALIBRATE.EXT_40m, SYSMENU_UINT8);
			SD_WRITE_SETT_LINE("CALIBRATE.EXT_30m", (uint64_t *)&CALIBRATE.EXT_30m, SYSMENU_UINT8);
			SD_WRITE_SETT_LINE("CALIBRATE.EXT_20m", (uint64_t *)&CALIBRATE.EXT_20m, SYSMENU_UINT8);
			SD_WRITE_SETT_LINE("CALIBRATE.EXT_17m", (uint64_t *)&CALIBRATE.EXT_17m, SYSMENU_UINT8);
			SD_WRITE_SETT_LINE("CALIBRATE.EXT_15m", (uint64_t *)&CALIBRATE.EXT_15m, SYSMENU_UINT8);
			SD_WRITE_SETT_LINE("CALIBRATE.EXT_12m", (uint64_t *)&CALIBRATE.EXT_12m, SYSMENU_UINT8);
			SD_WRITE_SETT_LINE("CALIBRATE.EXT_CB", (uint64_t *)&CALIBRATE.EXT_CB, SYSMENU_UINT8);
			SD_WRITE_SETT_LINE("CALIBRATE.EXT_10m", (uint64_t *)&CALIBRATE.EXT_10m, SYSMENU_UINT8);
			SD_WRITE_SETT_LINE("CALIBRATE.EXT_6m", (uint64_t *)&CALIBRATE.EXT_6m, SYSMENU_UINT8);
			SD_WRITE_SETT_LINE("CALIBRATE.EXT_4m", (uint64_t *)&CALIBRATE.EXT_4m, SYSMENU_UINT8);
			SD_WRITE_SETT_LINE("CALIBRATE.EXT_FM", (uint64_t *)&CALIBRATE.EXT_FM, SYSMENU_UINT8);
			SD_WRITE_SETT_LINE("CALIBRATE.EXT_2m", (uint64_t *)&CALIBRATE.EXT_2m, SYSMENU_UINT8);
			SD_WRITE_SETT_LINE("CALIBRATE.EXT_70cm", (uint64_t *)&CALIBRATE.EXT_70cm, SYSMENU_UINT8);
			SD_WRITE_SETT_LINE("CALIBRATE.EXT_23cm", (uint64_t *)&CALIBRATE.EXT_23cm, SYSMENU_UINT8);
			SD_WRITE_SETT_LINE("CALIBRATE.EXT_13cm", (uint64_t *)&CALIBRATE.EXT_13cm, SYSMENU_UINT8);
			SD_WRITE_SETT_LINE("CALIBRATE.EXT_6cm", (uint64_t *)&CALIBRATE.EXT_6cm, SYSMENU_UINT8);
			SD_WRITE_SETT_LINE("CALIBRATE.EXT_3cm", (uint64_t *)&CALIBRATE.EXT_3cm, SYSMENU_UINT8);
			SD_WRITE_SETT_LINE("CALIBRATE.EXT_QO100", (uint64_t *)&CALIBRATE.EXT_QO100, SYSMENU_UINT8);
			SD_WRITE_SETT_LINE("CALIBRATE.EXT_1_2cm", (uint64_t *)&CALIBRATE.EXT_1_2cm, SYSMENU_UINT8);
			SD_WRITE_SETT_LINE("CALIBRATE.NOTX_NOTHAM", (uint64_t *)&CALIBRATE.NOTX_NOTHAM, SYSMENU_BOOLEAN);
			SD_WRITE_SETT_LINE("CALIBRATE.NOTX_2200m", (uint64_t *)&CALIBRATE.NOTX_2200m, SYSMENU_BOOLEAN);
			SD_WRITE_SETT_LINE("CALIBRATE.NOTX_630m", (uint64_t *)&CALIBRATE.NOTX_630m, SYSMENU_BOOLEAN);
			SD_WRITE_SETT_LINE("CALIBRATE.NOTX_160m", (uint64_t *)&CALIBRATE.NOTX_160m, SYSMENU_BOOLEAN);
			SD_WRITE_SETT_LINE("CALIBRATE.NOTX_80m", (uint64_t *)&CALIBRATE.NOTX_80m, SYSMENU_BOOLEAN);
			SD_WRITE_SETT_LINE("CALIBRATE.NOTX_60m", (uint64_t *)&CALIBRATE.NOTX_60m, SYSMENU_BOOLEAN);
			SD_WRITE_SETT_LINE("CALIBRATE.NOTX_40m", (uint64_t *)&CALIBRATE.NOTX_40m, SYSMENU_BOOLEAN);
			SD_WRITE_SETT_LINE("CALIBRATE.NOTX_30m", (uint64_t *)&CALIBRATE.NOTX_30m, SYSMENU_BOOLEAN);
			SD_WRITE_SETT_LINE("CALIBRATE.NOTX_20m", (uint64_t *)&CALIBRATE.NOTX_20m, SYSMENU_BOOLEAN);
			SD_WRITE_SETT_LINE("CALIBRATE.NOTX_17m", (uint64_t *)&CALIBRATE.NOTX_17m, SYSMENU_BOOLEAN);
			SD_WRITE_SETT_LINE("CALIBRATE.NOTX_15m", (uint64_t *)&CALIBRATE.NOTX_15m, SYSMENU_BOOLEAN);
			SD_WRITE_SETT_LINE("CALIBRATE.NOTX_12m", (uint64_t *)&CALIBRATE.NOTX_12m, SYSMENU_BOOLEAN);
			SD_WRITE_SETT_LINE("CALIBRATE.NOTX_CB", (uint64_t *)&CALIBRATE.NOTX_CB, SYSMENU_BOOLEAN);
			SD_WRITE_SETT_LINE("CALIBRATE.NOTX_10m", (uint64_t *)&CALIBRATE.NOTX_10m, SYSMENU_BOOLEAN);
			SD_WRITE_SETT_LINE("CALIBRATE.NOTX_6m", (uint64_t *)&CALIBRATE.NOTX_6m, SYSMENU_BOOLEAN);
			SD_WRITE_SETT_LINE("CALIBRATE.NOTX_4m", (uint64_t *)&CALIBRATE.NOTX_4m, SYSMENU_BOOLEAN);
			SD_WRITE_SETT_LINE("CALIBRATE.NOTX_FM", (uint64_t *)&CALIBRATE.NOTX_FM, SYSMENU_BOOLEAN);
			SD_WRITE_SETT_LINE("CALIBRATE.NOTX_2m", (uint64_t *)&CALIBRATE.NOTX_2m, SYSMENU_BOOLEAN);
			SD_WRITE_SETT_LINE("CALIBRATE.NOTX_70cm", (uint64_t *)&CALIBRATE.NOTX_70cm, SYSMENU_BOOLEAN);
			SD_WRITE_SETT_LINE("CALIBRATE.NOTX_23cm", (uint64_t *)&CALIBRATE.NOTX_23cm, SYSMENU_BOOLEAN);
			SD_WRITE_SETT_LINE("CALIBRATE.ENABLE_2200m_band", (uint64_t *)&CALIBRATE.ENABLE_2200m_band, SYSMENU_BOOLEAN);
			SD_WRITE_SETT_LINE("CALIBRATE.ENABLE_630m_band", (uint64_t *)&CALIBRATE.ENABLE_630m_band, SYSMENU_BOOLEAN);
			SD_WRITE_SETT_LINE("CALIBRATE.ENABLE_60m_band", (uint64_t *)&CALIBRATE.ENABLE_60m_band, SYSMENU_BOOLEAN);
			SD_WRITE_SETT_LINE("CALIBRATE.ENABLE_6m_band", (uint64_t *)&CALIBRATE.ENABLE_6m_band, SYSMENU_BOOLEAN);
			SD_WRITE_SETT_LINE("CALIBRATE.ENABLE_4m_band", (uint64_t *)&CALIBRATE.ENABLE_4m_band, SYSMENU_BOOLEAN);
			SD_WRITE_SETT_LINE("CALIBRATE.ENABLE_FM_band", (uint64_t *)&CALIBRATE.ENABLE_FM_band, SYSMENU_BOOLEAN);
			SD_WRITE_SETT_LINE("CALIBRATE.ENABLE_2m_band", (uint64_t *)&CALIBRATE.ENABLE_2m_band, SYSMENU_BOOLEAN);
			SD_WRITE_SETT_LINE("CALIBRATE.ENABLE_AIR_band", (uint64_t *)&CALIBRATE.ENABLE_AIR_band, SYSMENU_BOOLEAN);
			SD_WRITE_SETT_LINE("CALIBRATE.ENABLE_marine_band", (uint64_t *)&CALIBRATE.ENABLE_marine_band, SYSMENU_BOOLEAN);
			SD_WRITE_SETT_LINE("CALIBRATE.ENABLE_70cm_band", (uint64_t *)&CALIBRATE.ENABLE_70cm_band, SYSMENU_BOOLEAN);
			SD_WRITE_SETT_LINE("CALIBRATE.ENABLE_23cm_band", (uint64_t *)&CALIBRATE.ENABLE_23cm_band, SYSMENU_BOOLEAN);
			SD_WRITE_SETT_LINE("CALIBRATE.Transverter_Custom_Offset_MHz", (uint64_t *)&CALIBRATE.Transverter_Custom_Offset_MHz, SYSMENU_UINT16);
			SD_WRITE_SETT_LINE("CALIBRATE.Transverter_2m_RF_MHz", (uint64_t *)&CALIBRATE.Transverter_2m_RF_MHz, SYSMENU_UINT16);
			SD_WRITE_SETT_LINE("CALIBRATE.Transverter_2m_IF_MHz", (uint64_t *)&CALIBRATE.Transverter_2m_IF_MHz, SYSMENU_UINT16);
			SD_WRITE_SETT_LINE("CALIBRATE.Transverter_70cm_RF_MHz", (uint64_t *)&CALIBRATE.Transverter_70cm_RF_MHz, SYSMENU_UINT16);
			SD_WRITE_SETT_LINE("CALIBRATE.Transverter_70cm_IF_MHz", (uint64_t *)&CALIBRATE.Transverter_70cm_IF_MHz, SYSMENU_UINT16);
			SD_WRITE_SETT_LINE("CALIBRATE.Transverter_23cm_RF_MHz", (uint64_t *)&CALIBRATE.Transverter_23cm_RF_MHz, SYSMENU_UINT16);
			SD_WRITE_SETT_LINE("CALIBRATE.Transverter_23cm_IF_MHz", (uint64_t *)&CALIBRATE.Transverter_23cm_IF_MHz, SYSMENU_UINT16);
			SD_WRITE_SETT_LINE("CALIBRATE.Transverter_13cm_RF_MHz", (uint64_t *)&CALIBRATE.Transverter_13cm_RF_MHz, SYSMENU_UINT16);
			SD_WRITE_SETT_LINE("CALIBRATE.Transverter_13cm_IF_MHz", (uint64_t *)&CALIBRATE.Transverter_13cm_IF_MHz, SYSMENU_UINT16);
			SD_WRITE_SETT_LINE("CALIBRATE.Transverter_6cm_RF_MHz", (uint64_t *)&CALIBRATE.Transverter_6cm_RF_MHz, SYSMENU_UINT16);
			SD_WRITE_SETT_LINE("CALIBRATE.Transverter_6cm_IF_MHz", (uint64_t *)&CALIBRATE.Transverter_6cm_IF_MHz, SYSMENU_UINT16);
			SD_WRITE_SETT_LINE("CALIBRATE.Transverter_3cm_RF_MHz", (uint64_t *)&CALIBRATE.Transverter_3cm_RF_MHz, SYSMENU_UINT16);
			SD_WRITE_SETT_LINE("CALIBRATE.Transverter_3cm_IF_MHz", (uint64_t *)&CALIBRATE.Transverter_3cm_IF_MHz, SYSMENU_UINT16);
			SD_WRITE_SETT_LINE("CALIBRATE.Transverter_QO100_RF_kHz", (uint64_t *)&CALIBRATE.Transverter_QO100_RF_kHz, SYSMENU_UINT32);
			SD_WRITE_SETT_LINE("CALIBRATE.Transverter_QO100_IF_RX_kHz", (uint64_t *)&CALIBRATE.Transverter_QO100_IF_RX_kHz, SYSMENU_UINT32);
			SD_WRITE_SETT_LINE("CALIBRATE.Transverter_QO100_IF_TX_MHz", (uint64_t *)&CALIBRATE.Transverter_QO100_IF_TX_MHz, SYSMENU_UINT16);
			SD_WRITE_SETT_LINE("CALIBRATE.Transverter_1_2cm_RF_MHz", (uint64_t *)&CALIBRATE.Transverter_1_2cm_RF_MHz, SYSMENU_UINT16);
			SD_WRITE_SETT_LINE("CALIBRATE.Transverter_1_2cm_IF_MHz", (uint64_t *)&CALIBRATE.Transverter_1_2cm_IF_MHz, SYSMENU_UINT16);
			SD_WRITE_SETT_LINE("CALIBRATE.KTY81_Calibration", (uint64_t *)&CALIBRATE.KTY81_Calibration, SYSMENU_UINT16);
			SD_WRITE_SETT_LINE("CALIBRATE.OTA_update", (uint64_t *)&CALIBRATE.OTA_update, SYSMENU_BOOLEAN);
			SD_WRITE_SETT_LINE("CALIBRATE.TX_StartDelay", (uint64_t *)&CALIBRATE.TX_StartDelay, SYSMENU_UINT16);
			SD_WRITE_SETT_LINE("CALIBRATE.LCD_Rotate", (uint64_t *)&CALIBRATE.LCD_Rotate, SYSMENU_BOOLEAN);
			SD_WRITE_SETT_LINE("CALIBRATE.TOUCHPAD_horizontal_flip", (uint64_t *)&CALIBRATE.TOUCHPAD_horizontal_flip, SYSMENU_BOOLEAN);
			SD_WRITE_SETT_LINE("CALIBRATE.TOUCHPAD_vertical_flip", (uint64_t *)&CALIBRATE.TOUCHPAD_vertical_flip, SYSMENU_BOOLEAN);
			SD_WRITE_SETT_LINE("CALIBRATE.INA226_EN", (uint64_t *)&CALIBRATE.INA226_EN, SYSMENU_BOOLEAN);
			SD_WRITE_SETT_LINE("CALIBRATE.INA226_Shunt_mOhm", (uint64_t *)&CALIBRATE.INA226_Shunt_mOhm, SYSMENU_FLOAT32);
			SD_WRITE_SETT_LINE("CALIBRATE.INA226_VoltageOffset", (uint64_t *)&CALIBRATE.INA226_VoltageOffset, SYSMENU_FLOAT32);
			SD_WRITE_SETT_LINE("CALIBRATE.PWR_VLT_Calibration", (uint64_t *)&CALIBRATE.PWR_VLT_Calibration, SYSMENU_FLOAT32);
			SD_WRITE_SETT_LINE("CALIBRATE.ATU_AVERAGING", (uint64_t *)&CALIBRATE.ATU_AVERAGING, SYSMENU_UINT8);
			SD_WRITE_SETT_LINE("CALIBRATE.LNA_compensation", (uint64_t *)&CALIBRATE.LNA_compensation, SYSMENU_INT8);
			SD_WRITE_SETT_LINE("CALIBRATE.CAT_Type", (uint64_t *)&CALIBRATE.CAT_Type, SYSMENU_UINT8);
			SD_WRITE_SETT_LINE("CALIBRATE.TwoSignalTune_Balance", (uint64_t *)&CALIBRATE.TwoSignalTune_Balance, SYSMENU_UINT8);
			SD_WRITE_SETT_LINE("CALIBRATE.LinearPowerControl", (uint64_t *)&CALIBRATE.LinearPowerControl, SYSMENU_BOOLEAN);
			SD_WRITE_SETT_LINE("CALIBRATE.ALC_Port_Enabled", (uint64_t *)&CALIBRATE.ALC_Port_Enabled, SYSMENU_BOOLEAN);
			SD_WRITE_SETT_LINE("CALIBRATE.ALC_Inverted_Logic", (uint64_t *)&CALIBRATE.ALC_Inverted_Logic, SYSMENU_BOOLEAN);
			SD_WRITE_SETT_LINE("CALIBRATE.IF_GAIN_MIN", (uint64_t *)&CALIBRATE.IF_GAIN_MIN, SYSMENU_UINT8);
			SD_WRITE_SETT_LINE("CALIBRATE.IF_GAIN_MAX", (uint64_t *)&CALIBRATE.IF_GAIN_MAX, SYSMENU_UINT8);
			SD_WRITE_SETT_LINE("CALIBRATE.TOUCHPAD_TIMEOUT", (uint64_t *)&CALIBRATE.TOUCHPAD_TIMEOUT, SYSMENU_UINT16);
			SD_WRITE_SETT_LINE("CALIBRATE.TOUCHPAD_CLICK_THRESHOLD", (uint64_t *)&CALIBRATE.TOUCHPAD_CLICK_THRESHOLD, SYSMENU_UINT16);
			SD_WRITE_SETT_LINE("CALIBRATE.TOUCHPAD_CLICK_TIMEOUT", (uint64_t *)&CALIBRATE.TOUCHPAD_CLICK_TIMEOUT, SYSMENU_UINT16);
			SD_WRITE_SETT_LINE("CALIBRATE.TOUCHPAD_HOLD_TIMEOUT", (uint64_t *)&CALIBRATE.TOUCHPAD_HOLD_TIMEOUT, SYSMENU_UINT16);
			SD_WRITE_SETT_LINE("CALIBRATE.TOUCHPAD_SWIPE_THRESHOLD_PX", (uint64_t *)&CALIBRATE.TOUCHPAD_SWIPE_THRESHOLD_PX, SYSMENU_UINT16);
			SD_WRITE_SETT_LINE("CALIBRATE.COM_CAT_DTR_Mode", (uint64_t *)&CALIBRATE.COM_CAT_DTR_Mode, SYSMENU_UINT8);
			SD_WRITE_SETT_LINE("CALIBRATE.COM_CAT_RTS_Mode", (uint64_t *)&CALIBRATE.COM_CAT_RTS_Mode, SYSMENU_UINT8);
			SD_WRITE_SETT_LINE("CALIBRATE.COM_DEBUG_DTR_Mode", (uint64_t *)&CALIBRATE.COM_DEBUG_DTR_Mode, SYSMENU_UINT8);
			SD_WRITE_SETT_LINE("CALIBRATE.COM_DEBUG_RTS_Mode", (uint64_t *)&CALIBRATE.COM_DEBUG_RTS_Mode, SYSMENU_UINT8);
			SD_WRITE_SETT_LINE("CALIBRATE.Swap_USB_IQ", (uint64_t *)&CALIBRATE.Swap_USB_IQ, SYSMENU_BOOLEAN);
			SD_WRITE_SETT_LINE("CALIBRATE.ATT_compensation", (uint64_t *)&CALIBRATE.ATT_compensation, SYSMENU_BOOLEAN);
		}

		if (!res) {
			LCD_showInfo("SD error", true);
		} else {
			LCD_showInfo("Calibration export complete", true);
		}
	} else {
		LCD_showInfo("SD error", true);
		SD_Present = false;
	}
	f_close(&File);
}

static void SDCOMM_PARSE_SETTINGS_LINE(char *line) {
	static IRAM2 char name[83] = {0};
	static IRAM2 char value[83] = {0};
	char *istr = strstr((char *)line, " = ");
	uint16_t name_len = (uint16_t)((uint32_t)istr - (uint32_t)line);
	dma_memset(name, 0x00, sizeof(name));
	dma_memset(value, 0x00, sizeof(value));
	if (name_len > 82) {
		LCD_showInfo("Line name length error", true);
		// println("E ", line);
		return;
	}
	if (strlen((char *)line + name_len + 3) > 82) {
		LCD_showInfo("Line value length error", true);
		return;
	}
	strncpy(name, (char *)line, name_len);
	strcpy(value, (char *)line + name_len + 3);

	uint64_t uint64val = atoll(value);
	uint32_t uintval = atol(value);
	int32_t intval = atol(value);
	float32_t floatval = atof(value);
	bool bval = false;
	if (uintval > 0) {
		bval = true;
	}

	// println("IMP: ",name, " = ", value);
	// print_flush();

	// TRX
	if (strcmp(name, "TRX.VFO_A.Freq") == 0) {
		TRX.VFO_A.Freq = uint64val;
	}
	if (strcmp(name, "TRX.VFO_A.Mode") == 0) {
		TRX.VFO_A.Mode = uintval;
	}
	if (strcmp(name, "TRX.VFO_A.LPF_RX_Filter_Width") == 0) {
		TRX.VFO_A.LPF_RX_Filter_Width = uintval;
	}
	if (strcmp(name, "TRX.VFO_A.LPF_TX_Filter_Width") == 0) {
		TRX.VFO_A.LPF_TX_Filter_Width = uintval;
	}
	if (strcmp(name, "TRX.VFO_A.HPF_RX_Filter_Width") == 0) {
		TRX.VFO_A.HPF_RX_Filter_Width = uintval;
	}
	if (strcmp(name, "TRX.VFO_A.HPF_TX_Filter_Width") == 0) {
		TRX.VFO_A.HPF_TX_Filter_Width = uintval;
	}
	if (strcmp(name, "TRX.VFO_A.ManualNotchFilter") == 0) {
		TRX.VFO_A.ManualNotchFilter = bval;
	}
	if (strcmp(name, "TRX.VFO_A.AutoNotchFilter") == 0) {
		TRX.VFO_A.AutoNotchFilter = bval;
	}
	if (strcmp(name, "TRX.VFO_A.NotchFC") == 0) {
		TRX.VFO_A.NotchFC = uintval;
	}
	if (strcmp(name, "TRX.VFO_A.DNR_Type") == 0) {
		TRX.VFO_A.DNR_Type = (uint8_t)uintval;
	}
	if (strcmp(name, "TRX.VFO_A.AGC") == 0) {
		TRX.VFO_A.AGC = bval;
	}
	if (strcmp(name, "TRX.VFO_A.RepeaterMode") == 0) {
		TRX.VFO_A.RepeaterMode = bval;
	}
	if (strcmp(name, "TRX.VFO_A.SQL") == 0) {
		TRX.VFO_A.SQL = bval;
	}
	if (strcmp(name, "TRX.VFO_A.FM_SQL_threshold_dBm") == 0) {
		TRX.VFO_A.FM_SQL_threshold_dBm = (int16_t)intval;
	}
	if (strcmp(name, "TRX.VFO_A.CW_LPF_Filter") == 0) {
		TRX.VFO_A.CW_LPF_Filter = (uint16_t)uintval;
	}
	if (strcmp(name, "TRX.VFO_A.DIGI_LPF_Filter") == 0) {
		TRX.VFO_A.DIGI_LPF_Filter = (uint16_t)uintval;
	}
	if (strcmp(name, "TRX.VFO_A.DIGI_HPF_Filter") == 0) {
		TRX.VFO_A.DIGI_HPF_Filter = (uint16_t)uintval;
	}
	if (strcmp(name, "TRX.VFO_A.SSB_LPF_RX_Filter") == 0) {
		TRX.VFO_A.SSB_LPF_RX_Filter = (uint16_t)uintval;
	}
	if (strcmp(name, "TRX.VFO_A.SSB_LPF_TX_Filter") == 0) {
		TRX.VFO_A.SSB_LPF_TX_Filter = (uint16_t)uintval;
	}
	if (strcmp(name, "TRX.VFO_A.SSB_HPF_RX_Filter") == 0) {
		TRX.VFO_A.SSB_HPF_RX_Filter = (uint16_t)uintval;
	}
	if (strcmp(name, "TRX.VFO_A.SSB_HPF_TX_Filter") == 0) {
		TRX.VFO_A.SSB_HPF_TX_Filter = (uint16_t)uintval;
	}
	if (strcmp(name, "TRX.VFO_A.AM_LPF_RX_Filter") == 0) {
		TRX.VFO_A.AM_LPF_RX_Filter = (uint16_t)uintval;
	}
	if (strcmp(name, "TRX.VFO_A.AM_LPF_TX_Filter") == 0) {
		TRX.VFO_A.AM_LPF_TX_Filter = (uint16_t)uintval;
	}
	if (strcmp(name, "TRX.VFO_A.FM_LPF_RX_Filter") == 0) {
		TRX.VFO_A.FM_LPF_RX_Filter = (uint16_t)uintval;
	}
	if (strcmp(name, "TRX.VFO_A.FM_LPF_TX_Filter") == 0) {
		TRX.VFO_A.FM_LPF_TX_Filter = (uint16_t)uintval;
	}
	if (strcmp(name, "TRX.VFO_A.FM_HPF_RX_Filter") == 0) {
		TRX.VFO_A.FM_HPF_RX_Filter = (uint16_t)uintval;
	}
	if (strcmp(name, "TRX.VFO_B.Freq") == 0) {
		TRX.VFO_B.Freq = uint64val;
	}
	if (strcmp(name, "TRX.VFO_B.Mode") == 0) {
		TRX.VFO_B.Mode = uintval;
	}
	if (strcmp(name, "TRX.VFO_B.LPF_RX_Filter_Width") == 0) {
		TRX.VFO_B.LPF_RX_Filter_Width = uintval;
	}
	if (strcmp(name, "TRX.VFO_B.LPF_TX_Filter_Width") == 0) {
		TRX.VFO_B.LPF_TX_Filter_Width = uintval;
	}
	if (strcmp(name, "TRX.VFO_B.HPF_RX_Filter_Width") == 0) {
		TRX.VFO_B.HPF_RX_Filter_Width = uintval;
	}
	if (strcmp(name, "TRX.VFO_B.HPF_TX_Filter_Width") == 0) {
		TRX.VFO_B.HPF_TX_Filter_Width = uintval;
	}
	if (strcmp(name, "TRX.VFO_B.ManualNotchFilter") == 0) {
		TRX.VFO_B.ManualNotchFilter = bval;
	}
	if (strcmp(name, "TRX.VFO_B.AutoNotchFilter") == 0) {
		TRX.VFO_B.AutoNotchFilter = bval;
	}
	if (strcmp(name, "TRX.VFO_B.NotchFC") == 0) {
		TRX.VFO_B.NotchFC = uintval;
	}
	if (strcmp(name, "TRX.VFO_B.DNR_Type") == 0) {
		TRX.VFO_B.DNR_Type = (uint8_t)uintval;
	}
	if (strcmp(name, "TRX.VFO_B.AGC") == 0) {
		TRX.VFO_B.AGC = bval;
	}
	if (strcmp(name, "TRX.VFO_B.RepeaterMode") == 0) {
		TRX.VFO_B.RepeaterMode = bval;
	}
	if (strcmp(name, "TRX.VFO_B.SQL") == 0) {
		TRX.VFO_B.SQL = bval;
	}
	if (strcmp(name, "TRX.VFO_B.FM_SQL_threshold_dBm") == 0) {
		TRX.VFO_B.FM_SQL_threshold_dBm = (int16_t)intval;
	}
	if (strcmp(name, "TRX.VFO_B.CW_LPF_Filter") == 0) {
		TRX.VFO_B.CW_LPF_Filter = (uint16_t)uintval;
	}
	if (strcmp(name, "TRX.VFO_B.DIGI_LPF_Filter") == 0) {
		TRX.VFO_B.DIGI_LPF_Filter = (uint16_t)uintval;
	}
	if (strcmp(name, "TRX.VFO_B.DIGI_HPF_Filter") == 0) {
		TRX.VFO_B.DIGI_HPF_Filter = (uint16_t)uintval;
	}
	if (strcmp(name, "TRX.VFO_B.SSB_LPF_RX_Filter") == 0) {
		TRX.VFO_B.SSB_LPF_RX_Filter = (uint16_t)uintval;
	}
	if (strcmp(name, "TRX.VFO_B.SSB_LPF_TX_Filter") == 0) {
		TRX.VFO_B.SSB_LPF_TX_Filter = (uint16_t)uintval;
	}
	if (strcmp(name, "TRX.VFO_B.SSB_HPF_RX_Filter") == 0) {
		TRX.VFO_B.SSB_HPF_RX_Filter = (uint16_t)uintval;
	}
	if (strcmp(name, "TRX.VFO_B.SSB_HPF_TX_Filter") == 0) {
		TRX.VFO_B.SSB_HPF_TX_Filter = (uint16_t)uintval;
	}
	if (strcmp(name, "TRX.VFO_B.AM_LPF_RX_Filter") == 0) {
		TRX.VFO_B.AM_LPF_RX_Filter = (uint16_t)uintval;
	}
	if (strcmp(name, "TRX.VFO_B.AM_LPF_TX_Filter") == 0) {
		TRX.VFO_B.AM_LPF_TX_Filter = (uint16_t)uintval;
	}
	if (strcmp(name, "TRX.VFO_B.FM_LPF_RX_Filter") == 0) {
		TRX.VFO_B.FM_LPF_RX_Filter = (uint16_t)uintval;
	}
	if (strcmp(name, "TRX.VFO_B.FM_LPF_TX_Filter") == 0) {
		TRX.VFO_B.FM_LPF_TX_Filter = (uint16_t)uintval;
	}
	if (strcmp(name, "TRX.VFO_B.FM_HPF_RX_Filter") == 0) {
		TRX.VFO_B.FM_HPF_RX_Filter = (uint16_t)uintval;
	}
	if (strcmp(name, "TRX.selected_vfo") == 0) {
		TRX.selected_vfo = bval;
	}
	if (strcmp(name, "TRX.LNA") == 0) {
		TRX.LNA = bval;
	}
	if (strcmp(name, "TRX.ATT") == 0) {
		TRX.ATT = bval;
	}
	if (strcmp(name, "TRX.ATT_DB") == 0) {
		TRX.ATT_DB = floatval;
	}
	if (strcmp(name, "TRX.ATT_STEP") == 0) {
		TRX.ATT_STEP = (uint8_t)uintval;
	}
	if (strcmp(name, "TRX.Fast") == 0) {
		TRX.Fast = bval;
	}
	if (strcmp(name, "TRX.ANT_RX") == 0) {
		TRX.ANT_RX = (uint8_t)uintval;
	}
	if (strcmp(name, "TRX.ANT_TX") == 0) {
		TRX.ANT_TX = (uint8_t)uintval;
	}
	if (strcmp(name, "TRX.RF_Filters") == 0) {
		TRX.RF_Filters = bval;
	}
	if (strcmp(name, "TRX.ChannelMode") == 0) {
		TRX.ChannelMode = bval;
	}
	if (strcmp(name, "TRX.SatMode") == 0) {
		TRX.SatMode = bval;
	}
	if (strcmp(name, "TRX.REPEATER_Offset") == 0) {
		TRX.REPEATER_Offset = intval;
	}
	if (strcmp(name, "TRX.RF_Gain") == 0) {
		TRX.RF_Gain = (uint8_t)uintval;
	}
	if (strcmp(name, "TRX.RF_Gain_For_Each_Band") == 0) {
		TRX.RF_Gain_For_Each_Band = bval;
	}
	if (strcmp(name, "TRX.RF_Gain_For_Each_Mode") == 0) {
		TRX.RF_Gain_For_Each_Mode = bval;
	}
	if (strcmp(name, "TRX.RIT_Enabled") == 0) {
		TRX.RIT_Enabled = bval;
	}
	if (strcmp(name, "TRX.XIT_Enabled") == 0) {
		TRX.XIT_Enabled = bval;
	}
	if (strcmp(name, "TRX.FineRITTune") == 0) {
		TRX.FineRITTune = bval;
	}
	if (strcmp(name, "TRX.RIT_INTERVAL") == 0) {
		TRX.RIT_INTERVAL = (uint16_t)uintval;
	}
	if (strcmp(name, "TRX.XIT_INTERVAL") == 0) {
		TRX.XIT_INTERVAL = (uint16_t)uintval;
	}
	if (strcmp(name, "TRX.TWO_SIGNAL_TUNE") == 0) {
		TRX.TWO_SIGNAL_TUNE = bval;
	}
	if (strcmp(name, "TRX.SAMPLERATE_MAIN") == 0) {
		TRX.SAMPLERATE_MAIN = (uint8_t)uintval;
	}
	if (strcmp(name, "TRX.SAMPLERATE_FM") == 0) {
		TRX.SAMPLERATE_FM = (uint8_t)uintval;
	}
	if (strcmp(name, "TRX.FRQ_STEP_CW_Hz") == 0) {
		TRX.FRQ_STEP_CW_Hz = uintval;
	}
	if (strcmp(name, "TRX.FRQ_STEP_SSB_Hz") == 0) {
		TRX.FRQ_STEP_SSB_Hz = uintval;
	}
	if (strcmp(name, "TRX.FRQ_STEP_DIGI_Hz") == 0) {
		TRX.FRQ_STEP_DIGI_Hz = uintval;
	}
	if (strcmp(name, "TRX.FRQ_STEP_AM_Hz") == 0) {
		TRX.FRQ_STEP_AM_Hz = uintval;
	}
	if (strcmp(name, "TRX.FRQ_STEP_FM_Hz") == 0) {
		TRX.FRQ_STEP_FM_Hz = uintval;
	}
	if (strcmp(name, "TRX.FRQ_STEP_WFM_Hz") == 0) {
		TRX.FRQ_STEP_WFM_Hz = uintval;
	}
	if (strcmp(name, "TRX.FAST_STEP_Multiplier") == 0) {
		TRX.FAST_STEP_Multiplier = (uint8_t)uintval;
	}
	if (strcmp(name, "TRX.ENC2_STEP_Multiplier") == 0) {
		TRX.ENC2_STEP_Multiplier = (uint8_t)uintval;
	}
	if (strcmp(name, "TRX.Debug_Type") == 0) {
		TRX.Debug_Type = (uint8_t)uintval;
	}
	if (strcmp(name, "TRX.DXCluster_Type") == 0) {
		TRX.DXCluster_Type = (uint8_t)uintval;
	}
	if (strcmp(name, "TRX.BandMapEnabled") == 0) {
		TRX.BandMapEnabled = bval;
	}
	if (strcmp(name, "TRX.InputType_MAIN") == 0) {
		TRX.InputType_MAIN = (uint8_t)uintval;
	}
	if (strcmp(name, "TRX.InputType_DIGI") == 0) {
		TRX.InputType_DIGI = (uint8_t)uintval;
	}
	if (strcmp(name, "TRX.AutoGain") == 0) {
		TRX.AutoGain = bval;
	}
	if (strcmp(name, "TRX.SPLIT_Enabled") == 0) {
		TRX.SPLIT_Enabled = bval;
	}
	if (strcmp(name, "TRX.Split_Mode_Sync_Freq") == 0) {
		TRX.Split_Mode_Sync_Freq = bval;
	}
	if (strcmp(name, "TRX.WOLF_Cluster") == 0) {
		TRX.WOLF_Cluster = bval;
	}
	if (strcmp(name, "TRX.FREE_Tune") == 0) {
		TRX.FREE_Tune = bval;
	}
	if (strcmp(name, "TRX.FT8_Auto_CQ") == 0) {
		TRX.FT8_Auto_CQ = bval;
	}
#if HRDW_HAS_DUAL_RX
	if (strcmp(name, "TRX.Dual_RX") == 0) {
		TRX.Dual_RX = bval;
	}
	if (strcmp(name, "TRX.Dual_RX_Type") == 0) {
		TRX.Dual_RX_Type = (DUAL_RX_TYPE)uintval;
	}
	if (strcmp(name, "TRX.Dual_RX_AB_Balance") == 0) {
		TRX.Dual_RX_AB_Balance = (int8_t)intval;
	}
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
