witalis3/UA3REO-DDC-Transceiver/STM32/Src/system_menu.c

#include "system_menu.h"
#include "FT8/FT8_main.h"
#include "INA226_PWR_monitor.h"
#include "agc.h"
#include "atu.h"
#include "audio_filters.h"
#include "auto_calibration.h"
#include "bands.h"
#include "bootloader.h"
#include "callsign.h"
#include "cw.h"
#include "filemanager.h"
#include "fonts.h"
#include "front_unit.h"
#include "functions.h"
#include "hardware.h"
#include "lcd.h"
#include "locator.h"
#include "noise_blanker.h"
#include "rf_unit.h"
#include "rtty_decoder.h"
#include "satellite.h"
#include "screen_layout.h"
#include "sd.h"
#include "self_test.h"
#include "settings.h"
#include "spec_analyzer.h"
#include "swr_analyzer.h"
#include "usbd_ua3reo.h"
#include "wifi.h"
#include "wspr.h"

static void SYSMENU_HANDL_TRX_BandMap(int8_t direction);
static void SYSMENU_HANDL_TRX_Beeper(int8_t direction);
static void SYSMENU_HANDL_TRX_ChannelMode(int8_t direction);
static void SYSMENU_HANDL_TRX_DEBUG_TYPE(int8_t direction);
static void SYSMENU_HANDL_TRX_ENC_ACCELERATE(int8_t direction);
static void SYSMENU_HANDL_TRX_FAST_STEP_Multiplier(int8_t direction);
static void SYSMENU_HANDL_TRX_ENC2_STEP_Multiplier(int8_t direction);
static void SYSMENU_HANDL_TRX_FRQ_STEP_CW_Hz(int8_t direction);
static void SYSMENU_HANDL_TRX_FRQ_STEP_SSB_Hz(int8_t direction);
static void SYSMENU_HANDL_TRX_FRQ_STEP_DIGI_Hz(int8_t direction);
static void SYSMENU_HANDL_TRX_FRQ_STEP_AM_Hz(int8_t direction);
static void SYSMENU_HANDL_TRX_FRQ_STEP_FM_Hz(int8_t direction);
static void SYSMENU_HANDL_TRX_FRQ_STEP_WFM_Hz(int8_t direction);
static void SYSMENU_HANDL_TRX_NOTCH_STEP_Hz(int8_t direction);
static void SYSMENU_HANDL_TRX_FineRITTune(int8_t direction);
static void SYSMENU_HANDL_TRX_Full_Duplex(int8_t direction);
static void SYSMENU_HANDL_TRX_RIT_INTERVAL(int8_t direction);
static void SYSMENU_HANDL_TRX_SetCallsign(int8_t direction);
static void SYSMENU_HANDL_TRX_SetLocator(int8_t direction);
static void SYSMENU_HANDL_TRX_SetURSICode(int8_t direction);
static void SYSMENU_HANDL_TRX_Split_Mode_Sync_Freq(int8_t direction);
static void SYSMENU_HANDL_TRX_TROPO_Region(int8_t direction);
static void SYSMENU_HANDL_TRX_TRANSV_13CM(int8_t direction);
static void SYSMENU_HANDL_TRX_TRANSV_23CM(int8_t direction);
static void SYSMENU_HANDL_TRX_TRANSV_3CM(int8_t direction);
static void SYSMENU_HANDL_TRX_TRANSV_1_2CM(int8_t direction);
static void SYSMENU_HANDL_TRX_TRANSV_6CM(int8_t direction);
static void SYSMENU_HANDL_TRX_TRANSV_70CM(int8_t direction);
static void SYSMENU_HANDL_TRX_TRANSV_2M(int8_t direction);
static void SYSMENU_HANDL_TRX_TRANSV_ENABLE(int8_t direction);
static void SYSMENU_HANDL_TRX_TRANSV_QO100(int8_t direction);
static void SYSMENU_HANDL_TRX_XIT_INTERVAL(int8_t direction);

static void SYSMENU_HANDL_FILTER_AMFM_LPF_Stages(int8_t direction);
static void SYSMENU_HANDL_FILTER_CW_GaussFilter(int8_t direction);
static void SYSMENU_HANDL_FILTER_CW_LPF_Stages(int8_t direction);
static void SYSMENU_HANDL_FILTER_SSB_LPF_Stages(int8_t direction);
static void SYSMENU_HANDL_FILTER_NOTCH_Filter_width(int8_t direction);

static void SYSMENU_HANDL_RX_ADC_DITH(int8_t direction);
static void SYSMENU_HANDL_RX_ADC_DRIVER(int8_t direction);
static void SYSMENU_HANDL_RX_ADC_PGA(int8_t direction);
static void SYSMENU_HANDL_RX_ADC_RAND(int8_t direction);
static void SYSMENU_HANDL_RX_ADC_SHDN(int8_t direction);
static void SYSMENU_HANDL_RX_AGC(int8_t direction);
static void SYSMENU_HANDL_RX_AGC_CW_Speed(int8_t direction);
static void SYSMENU_HANDL_RX_AGC_Gain_target_SSB(int8_t direction);
static void SYSMENU_HANDL_RX_AGC_Gain_target_CW(int8_t direction);
static void SYSMENU_HANDL_RX_AGC_Hold_Time(int8_t direction);
static void SYSMENU_HANDL_RX_AGC_Hold_Limiter(int8_t direction);
static void SYSMENU_HANDL_RX_AGC_Hold_Step_Up(int8_t direction);
static void SYSMENU_HANDL_RX_AGC_Hold_Step_Down(int8_t direction);
static void SYSMENU_HANDL_RX_AGC_Max_gain(int8_t direction);
static void SYSMENU_HANDL_RX_AGC_SSB_Speed(int8_t direction);
static void SYSMENU_HANDL_RX_AGC_Spectral(int8_t direction);
static void SYSMENU_HANDL_RX_AGC_Threshold(int8_t direction);
static void SYSMENU_HANDL_RX_ATT_DB(int8_t direction);
static void SYSMENU_HANDL_RX_ATT_STEP(int8_t direction);
static void SYSMENU_HANDL_RX_AutoGain(int8_t direction);
static void SYSMENU_HANDL_RX_Auto_Snap(int8_t direction);
static void SYSMENU_HANDL_RX_DNR(int8_t direction);
static void SYSMENU_HANDL_RX_DNR1_THRES(int8_t direction);
static void SYSMENU_HANDL_RX_DNR2_THRES(int8_t direction);
static void SYSMENU_HANDL_RX_DNR_AVERAGE(int8_t direction);
static void SYSMENU_HANDL_RX_DNR_MINMAL(int8_t direction);
static void SYSMENU_HANDL_RX_EQ_P1(int8_t direction);
static void SYSMENU_HANDL_RX_EQ_P1_WFM(int8_t direction);
static void SYSMENU_HANDL_RX_EQ_P2(int8_t direction);
static void SYSMENU_HANDL_RX_EQ_P2_WFM(int8_t direction);
static void SYSMENU_HANDL_RX_EQ_P3(int8_t direction);
static void SYSMENU_HANDL_RX_EQ_P3_WFM(int8_t direction);
static void SYSMENU_HANDL_RX_EQ_P4(int8_t direction);
static void SYSMENU_HANDL_RX_EQ_P4_WFM(int8_t direction);
static void SYSMENU_HANDL_RX_EQ_P5(int8_t direction);
static void SYSMENU_HANDL_RX_EQ_P5_WFM(int8_t direction);
static void SYSMENU_HANDL_RX_EQ_P6(int8_t direction);
static void SYSMENU_HANDL_RX_EQ_P6_WFM(int8_t direction);
static void SYSMENU_HANDL_RX_FMSquelch(int8_t direction);
static void SYSMENU_HANDL_RX_FM_Stereo(int8_t direction);
static void SYSMENU_HANDL_RX_FM_Stereo_Modulation(int8_t direction);
static void SYSMENU_HANDL_RX_IFGain(int8_t direction);
static void SYSMENU_HANDL_RX_NOISE_BLANKER1(int8_t direction);
static void SYSMENU_HANDL_RX_NOISE_BLANKER2(int8_t direction);
static void SYSMENU_HANDL_RX_NOISE_BLANKER1_THRESHOLD(int8_t direction);
static void SYSMENU_HANDL_RX_NOISE_BLANKER2_THRESHOLD(int8_t direction);
static void SYSMENU_HANDL_RX_RFFilters(int8_t direction);
static void SYSMENU_HANDL_RX_SAMPLERATE_FM(int8_t direction);
static void SYSMENU_HANDL_RX_SAMPLERATE_MAIN(int8_t direction);
static void SYSMENU_HANDL_RX_Squelch(int8_t direction);
static void SYSMENU_HANDL_RX_VAD_THRESHOLD(int8_t direction);
static void SYSMENU_HANDL_RX_VGA_GAIN(int8_t direction);
static void SYSMENU_HANDL_RX_Volume(int8_t direction);
static void SYSMENU_HANDL_RX_Volume_Step(int8_t direction);
static void SYSMENU_HANDL_RX_CODEC_Out_Volume(int8_t direction);
static void SYSMENU_HANDL_RX_BluetoothAudio_Enabled(int8_t direction);
static void SYSMENU_HANDL_RX_AUDIO_MODE(int8_t direction);
static void SYSMENU_HANDL_RX_FREE_Tune(int8_t direction);
static void SYSMENU_HANDL_RX_CenterAfterIdle(int8_t direction);
static void SYSMENU_HANDL_RX_Dual_RX_AB_Balance(int8_t direction);

static void SYSMENU_HANDL_TX_ATU_C(int8_t direction);
static void SYSMENU_HANDL_TX_ATU_Enabled(int8_t direction);
static void SYSMENU_HANDL_TX_ATU_I(int8_t direction);
static void SYSMENU_HANDL_TX_ATU_T(int8_t direction);
static void SYSMENU_HANDL_TX_Auto_Input_Switch(int8_t direction);
static void SYSMENU_HANDL_TX_CESSB(int8_t direction);
static void SYSMENU_HANDL_TX_CESSB_COMPRESS_DB(int8_t direction);
static void SYSMENU_HANDL_TX_CTCSS_Freq(int8_t direction);
static void SYSMENU_HANDL_TX_CompressorMaxGain_AMFM(int8_t direction);
static void SYSMENU_HANDL_TX_CompressorMaxGain_SSB(int8_t direction);
static void SYSMENU_HANDL_TX_CompressorSpeed_AMFM(int8_t direction);
static void SYSMENU_HANDL_TX_CompressorSpeed_SSB(int8_t direction);
static void SYSMENU_HANDL_TX_INPUT_TYPE_DIGI(int8_t direction);
static void SYSMENU_HANDL_TX_INPUT_TYPE_MAIN(int8_t direction);
static void SYSMENU_HANDL_TX_MIC_Boost(int8_t direction);
static void SYSMENU_HANDL_TX_LINE_Volume(int8_t direction);
static void SYSMENU_HANDL_TX_MIC_EQ_P1_AMFM(int8_t direction);
static void SYSMENU_HANDL_TX_MIC_EQ_P1_SSB(int8_t direction);
static void SYSMENU_HANDL_TX_MIC_EQ_P2_AMFM(int8_t direction);
static void SYSMENU_HANDL_TX_MIC_EQ_P2_SSB(int8_t direction);
static void SYSMENU_HANDL_TX_MIC_EQ_P3_AMFM(int8_t direction);
static void SYSMENU_HANDL_TX_MIC_EQ_P3_SSB(int8_t direction);
static void SYSMENU_HANDL_TX_MIC_EQ_P4_AMFM(int8_t direction);
static void SYSMENU_HANDL_TX_MIC_EQ_P4_SSB(int8_t direction);
static void SYSMENU_HANDL_TX_MIC_EQ_P5_AMFM(int8_t direction);
static void SYSMENU_HANDL_TX_MIC_EQ_P5_SSB(int8_t direction);
static void SYSMENU_HANDL_TX_MIC_EQ_P6_AMFM(int8_t direction);
static void SYSMENU_HANDL_TX_MIC_EQ_P6_SSB(int8_t direction);
static void SYSMENU_HANDL_TX_MIC_Gain_SSB_DB(int8_t direction);
static void SYSMENU_HANDL_TX_MIC_Gain_AM_DB(int8_t direction);
static void SYSMENU_HANDL_TX_MIC_Gain_FM_DB(int8_t direction);
static void SYSMENU_HANDL_TX_MIC_NOISE_GATE(int8_t direction);
static void SYSMENU_HANDL_TX_MIC_REVERBER(int8_t direction);
static void SYSMENU_HANDL_TX_REPEATER_Offset(int8_t direction);
static void SYSMENU_HANDL_TX_RFPower(int8_t direction);
static void SYSMENU_HANDL_TX_RF_Gain_For_Each_Band(int8_t direction);
static void SYSMENU_HANDL_TX_RF_Gain_For_Each_Mode(int8_t direction);
static void SYSMENU_HANDL_TX_RepeaterMode(int8_t direction);
static void SYSMENU_HANDL_TX_SELFHEAR_Volume(int8_t direction);
static void SYSMENU_HANDL_TX_TUNER_Enabled(int8_t direction);
static void SYSMENU_HANDL_TX_ATU_MEM_STEP_KHZ(int8_t direction);
static void SYSMENU_HANDL_TX_TWO_SIGNAL_TUNE(int8_t direction);
static void SYSMENU_HANDL_TX_VOX(int8_t direction);
static void SYSMENU_HANDL_TX_VOX_THRESHOLD(int8_t direction);
static void SYSMENU_HANDL_TX_VOX_TIMEOUT(int8_t direction);
static void SYSMENU_HANDL_TX_FT8_Auto_CQ(int8_t direction);

static void SYSMENU_HANDL_CW_DotToDashRate(int8_t direction);
static void SYSMENU_HANDL_CW_Iambic(int8_t direction);
static void SYSMENU_HANDL_CW_Iambic_Type(int8_t direction);
static void SYSMENU_HANDL_CW_Invert(int8_t direction);
static void SYSMENU_HANDL_CW_Auto_CW_Mode(int8_t direction);
static void SYSMENU_HANDL_CW_In_SSB(int8_t direction);
static void SYSMENU_HANDL_CW_Key_timeout(int8_t direction);
static void SYSMENU_HANDL_CW_Keyer(int8_t direction);
static void SYSMENU_HANDL_CW_OneSymbolMemory(int8_t direction);
static void SYSMENU_HANDL_CW_Keyer_WPM(int8_t direction);
static void SYSMENU_HANDL_CW_PTT_Type(int8_t direction);
static void SYSMENU_HANDL_CW_EDGES_SMOOTH_MS(int8_t direction);
static void SYSMENU_HANDL_CW_Pitch(int8_t direction);
static void SYSMENU_HANDL_CW_SelfHear(int8_t direction);
static void SYSMENU_HANDL_CW_SetCWMacros1(int8_t direction);
static void SYSMENU_HANDL_CW_SetCWMacros2(int8_t direction);
static void SYSMENU_HANDL_CW_SetCWMacros3(int8_t direction);
static void SYSMENU_HANDL_CW_SetCWMacros4(int8_t direction);
static void SYSMENU_HANDL_CW_SetCWMacros5(int8_t direction);
static void SYSMENU_HANDL_CW_SetCWMacrosName1(int8_t direction);
static void SYSMENU_HANDL_CW_SetCWMacrosName2(int8_t direction);
static void SYSMENU_HANDL_CW_SetCWMacrosName3(int8_t direction);
static void SYSMENU_HANDL_CW_SetCWMacrosName4(int8_t direction);
static void SYSMENU_HANDL_CW_SetCWMacrosName5(int8_t direction);

static void SYSMENU_HANDL_SCREEN_COLOR_THEME(int8_t direction);
static void SYSMENU_HANDL_SCREEN_FFT_3D(int8_t direction);
static void SYSMENU_HANDL_SCREEN_FFT_Automatic_Type(int8_t direction);
static void SYSMENU_HANDL_SCREEN_FFT_Averaging(int8_t direction);
static void SYSMENU_HANDL_SCREEN_FFT_BW_Style(int8_t direction);
static void SYSMENU_HANDL_SCREEN_FFT_BW_Position(int8_t direction);
static void SYSMENU_HANDL_SCREEN_FFT_Background(int8_t direction);
static void SYSMENU_HANDL_SCREEN_FFT_Color(int8_t direction);
static void SYSMENU_HANDL_SCREEN_FFT_Compressor(int8_t direction);
static void SYSMENU_HANDL_SCREEN_FFT_Enabled(int8_t direction);
static void SYSMENU_HANDL_SCREEN_FFT_FreqGrid(int8_t direction);
static void SYSMENU_HANDL_SCREEN_FFT_Height(int8_t direction);
static void SYSMENU_HANDL_SCREEN_FFT_HoldPeaks(int8_t direction);
static void SYSMENU_HANDL_SCREEN_FFT_Lens(int8_t direction);
static void SYSMENU_HANDL_SCREEN_FFT_ManualBottom(int8_t direction);
static void SYSMENU_HANDL_SCREEN_FFT_ManualTop(int8_t direction);
static void SYSMENU_HANDL_SCREEN_FFT_Scale_Type(int8_t direction);
static void SYSMENU_HANDL_SCREEN_FFT_Sensitivity(int8_t direction);
static void SYSMENU_HANDL_SCREEN_FFT_Speed(int8_t direction);
static void SYSMENU_HANDL_SCREEN_FFT_Style(int8_t direction);
static void SYSMENU_HANDL_SCREEN_FFT_Window(int8_t direction);
static void SYSMENU_HANDL_SCREEN_FFT_Zoom(int8_t direction);
static void SYSMENU_HANDL_SCREEN_FFT_ZoomCW(int8_t direction);
static void SYSMENU_HANDL_SCREEN_FFT_dBmGrid(int8_t direction);
static void SYSMENU_HANDL_SCREEN_LAYOUT_THEME(int8_t direction);
static void SYSMENU_HANDL_SCREEN_LCD_Brightness(int8_t direction);
static void SYSMENU_HANDL_SCREEN_LCD_SleepTimeout(int8_t direction);
static void SYSMENU_HANDL_SCREEN_Show_Sec_VFO(int8_t direction);
static void SYSMENU_HANDL_SCREEN_EnableBottomNavigationButtons(int8_t direction);
static void SYSMENU_HANDL_SCREEN_WTF_Color(int8_t direction);
static void SYSMENU_HANDL_SCREEN_WTF_Moving(int8_t direction);
#if HRDW_HAS_WIFI
static void SYSMENU_HANDL_SCREEN_DXCluster_Type(int8_t direction);
static void SYSMENU_HANDL_SCREEN_FFT_DXCluster(int8_t direction);
static void SYSMENU_HANDL_SCREEN_FFT_DXCluster_Azimuth(int8_t direction);
static void SYSMENU_HANDL_SCREEN_FFT_DXCluster_Timeout(int8_t direction);
static void SYSMENU_HANDL_SCREEN_WOLF_Cluster(int8_t direction);
#endif
static void SYSMENU_HANDL_SCREEN_FUNC_BUTTON1(int8_t direction);
static void SYSMENU_HANDL_SCREEN_FUNC_BUTTON2(int8_t direction);
static void SYSMENU_HANDL_SCREEN_FUNC_BUTTON3(int8_t direction);
static void SYSMENU_HANDL_SCREEN_FUNC_BUTTON4(int8_t direction);
static void SYSMENU_HANDL_SCREEN_FUNC_BUTTON5(int8_t direction);
static void SYSMENU_HANDL_SCREEN_FUNC_BUTTON6(int8_t direction);
static void SYSMENU_HANDL_SCREEN_FUNC_BUTTON7(int8_t direction);
static void SYSMENU_HANDL_SCREEN_FUNC_BUTTON8(int8_t direction);
static void SYSMENU_HANDL_SCREEN_FUNC_BUTTON9(int8_t direction);
static void SYSMENU_HANDL_SCREEN_FUNC_BUTTON10(int8_t direction);
static void SYSMENU_HANDL_SCREEN_FUNC_BUTTON11(int8_t direction);
static void SYSMENU_HANDL_SCREEN_FUNC_BUTTON12(int8_t direction);
static void SYSMENU_HANDL_SCREEN_FUNC_BUTTON13(int8_t direction);
static void SYSMENU_HANDL_SCREEN_FUNC_BUTTON14(int8_t direction);
static void SYSMENU_HANDL_SCREEN_FUNC_BUTTON15(int8_t direction);
static void SYSMENU_HANDL_SCREEN_FUNC_BUTTON16(int8_t direction);
static void SYSMENU_HANDL_SCREEN_FUNC_BUTTON17(int8_t direction);
static void SYSMENU_HANDL_SCREEN_FUNC_BUTTON18(int8_t direction);
static void SYSMENU_HANDL_SCREEN_FUNC_BUTTON19(int8_t direction);
static void SYSMENU_HANDL_SCREEN_FUNC_BUTTON20(int8_t direction);
static void SYSMENU_HANDL_SCREEN_FUNC_BUTTON21(int8_t direction);
static void SYSMENU_HANDL_SCREEN_FUNC_BUTTON22(int8_t direction);
static void SYSMENU_HANDL_SCREEN_FUNC_BUTTON23(int8_t direction);
static void SYSMENU_HANDL_SCREEN_FUNC_BUTTON24(int8_t direction);
static void SYSMENU_HANDL_SCREEN_FUNC_BUTTON25(int8_t direction);
static void SYSMENU_HANDL_SCREEN_FUNC_BUTTON26(int8_t direction);
static void SYSMENU_HANDL_SCREEN_FUNC_BUTTON27(int8_t direction);
static void SYSMENU_HANDL_SCREEN_FUNC_BUTTON28(int8_t direction);
static void SYSMENU_HANDL_SCREEN_FUNC_BUTTON29(int8_t direction);
static void SYSMENU_HANDL_SCREEN_FUNC_BUTTON30(int8_t direction);
static void SYSMENU_HANDL_SCREEN_FUNC_BUTTON31(int8_t direction);
static void SYSMENU_HANDL_SCREEN_FUNC_BUTTON32(int8_t direction);
static void SYSMENU_HANDL_SCREEN_FUNC_BUTTON33(int8_t direction);
static void SYSMENU_HANDL_SCREEN_FUNC_BUTTON34(int8_t direction);
static void SYSMENU_HANDL_SCREEN_FUNC_BUTTON35(int8_t direction);
static void SYSMENU_HANDL_SCREEN_FUNC_BUTTON36(int8_t direction);
static void SYSMENU_HANDL_SCREEN_FUNC_BUTTON37(int8_t direction);
static void SYSMENU_HANDL_SCREEN_FUNC_BUTTON38(int8_t direction);
static void SYSMENU_HANDL_SCREEN_FUNC_BUTTON39(int8_t direction);
static void SYSMENU_HANDL_SCREEN_FUNC_BUTTON40(int8_t direction);

static void SYSMENU_HANDL_DECODERS_CW_Decoder(int8_t direction);
static void SYSMENU_HANDL_DECODERS_CW_Decoder_Threshold(int8_t direction);
static void SYSMENU_HANDL_DECODERS_RDS_Decoder(int8_t direction);
static void SYSMENU_HANDL_DECODERS_RTTY_Freq(int8_t direction);
static void SYSMENU_HANDL_DECODERS_RTTY_InvertBits(int8_t direction);
static void SYSMENU_HANDL_DECODERS_RTTY_Shift(int8_t direction);
static void SYSMENU_HANDL_DECODERS_RTTY_Speed(int8_t direction);
static void SYSMENU_HANDL_DECODERS_RTTY_StopBits(int8_t direction);

#if HRDW_HAS_WIFI
static void SYSMENU_HANDL_WIFI_CAT_Server(int8_t direction);
static void SYSMENU_HANDL_WIFI_Enabled(int8_t direction);
static void SYSMENU_HANDL_WIFI_SelectAP1(int8_t direction);
static void SYSMENU_HANDL_WIFI_SelectAP2(int8_t direction);
static void SYSMENU_HANDL_WIFI_SelectAP3(int8_t direction);
static void SYSMENU_HANDL_WIFI_SetALLQSO_LOGID(int8_t direction);
static void SYSMENU_HANDL_WIFI_SetALLQSO_TOKEN(int8_t direction);
static void SYSMENU_HANDL_WIFI_SetAP1password(int8_t direction);
static void SYSMENU_HANDL_WIFI_SetAP2password(int8_t direction);
static void SYSMENU_HANDL_WIFI_SetAP3password(int8_t direction);
static void SYSMENU_HANDL_WIFI_Timezone(int8_t direction);
static void SYSMENU_HANDL_WIFI_UpdateFW(int8_t direction);
#endif

#if HRDW_HAS_SD
static void SYSMENU_HANDL_SD_ExportSettings1(int8_t direction);
static void SYSMENU_HANDL_SD_ExportSettings2(int8_t direction);
static void SYSMENU_HANDL_SD_ExportSettings3(int8_t direction);
static void SYSMENU_HANDL_SD_ExportCalibrations1(int8_t direction);
static void SYSMENU_HANDL_SD_ExportCalibrations2(int8_t direction);
static void SYSMENU_HANDL_SD_ExportCalibrations3(int8_t direction);
static void SYSMENU_HANDL_SD_ExportSettingsDialog(int8_t direction);
static void SYSMENU_HANDL_SD_Filemanager(int8_t direction);
static void SYSMENU_HANDL_SD_Format(int8_t direction);
static void SYSMENU_HANDL_SD_FormatDialog(int8_t direction);
static void SYSMENU_HANDL_SD_ImportSettings1(int8_t direction);
static void SYSMENU_HANDL_SD_ImportSettings2(int8_t direction);
static void SYSMENU_HANDL_SD_ImportSettings3(int8_t direction);
static void SYSMENU_HANDL_SD_ImportCalibrations1(int8_t direction);
static void SYSMENU_HANDL_SD_ImportCalibrations2(int8_t direction);
static void SYSMENU_HANDL_SD_ImportCalibrations3(int8_t direction);
static void SYSMENU_HANDL_SD_ImportSettingsDialog(int8_t direction);
static void SYSMENU_HANDL_SD_USB(int8_t direction);

static void SYSMENU_HANDL_SAT_SatMode(int8_t direction);
static void SYSMENU_HANDL_SAT_DownloadTLE(int8_t direction);
static void SYSMENU_HANDL_SAT_SelectSAT(int8_t direction);
static void SYSMENU_HANDL_SAT_QTHLat(int8_t direction);
static void SYSMENU_HANDL_SAT_QTHLon(int8_t direction);
static void SYSMENU_HANDL_SAT_QTHAlt(int8_t direction);
#endif

static void SYSMENU_HANDL_SETTIME(int8_t direction);
static void SYSMENU_HANDL_Bootloader(int8_t direction);
#if HRDW_HAS_SD
static void SYSMENU_HANDL_OTA_Update(int8_t direction);
#endif
static void SYSMENU_HANDL_SYSINFO(int8_t direction);
static void SYSMENU_HANDL_SUPPORT(int8_t direction);

static void SYSMENU_HANDL_CALIB_ALC_Port_Enabled(int8_t direction);
static void SYSMENU_HANDL_CALIB_ALC_Inverted_Logic(int8_t direction);
static void SYSMENU_HANDL_CALIB_AM_MODULATION_INDEX(int8_t direction);
static void SYSMENU_HANDL_CALIB_ATU_AVERAGING(int8_t direction);
static void SYSMENU_HANDL_CALIB_BPF_0_END(int8_t direction);
static void SYSMENU_HANDL_CALIB_BPF_0_START(int8_t direction);
static void SYSMENU_HANDL_CALIB_BPF_1_END(int8_t direction);
static void SYSMENU_HANDL_CALIB_BPF_1_START(int8_t direction);
static void SYSMENU_HANDL_CALIB_BPF_2_END(int8_t direction);
static void SYSMENU_HANDL_CALIB_BPF_2_START(int8_t direction);
static void SYSMENU_HANDL_CALIB_BPF_3_END(int8_t direction);
static void SYSMENU_HANDL_CALIB_BPF_3_START(int8_t direction);
static void SYSMENU_HANDL_CALIB_BPF_4_END(int8_t direction);
static void SYSMENU_HANDL_CALIB_BPF_4_START(int8_t direction);
static void SYSMENU_HANDL_CALIB_BPF_5_END(int8_t direction);
static void SYSMENU_HANDL_CALIB_BPF_5_START(int8_t direction);
static void SYSMENU_HANDL_CALIB_BPF_6_END(int8_t direction);
static void SYSMENU_HANDL_CALIB_BPF_6_START(int8_t direction);
static void SYSMENU_HANDL_CALIB_BPF_7_END(int8_t direction);
static void SYSMENU_HANDL_CALIB_BPF_7_START(int8_t direction);
static void SYSMENU_HANDL_CALIB_BPF_8_END(int8_t direction);
static void SYSMENU_HANDL_CALIB_BPF_8_START(int8_t direction);
static void SYSMENU_HANDL_CALIB_BPF_9_END(int8_t direction);
static void SYSMENU_HANDL_CALIB_BPF_9_START(int8_t direction);
static void SYSMENU_HANDL_CALIB_CALIBRATION_RESET(int8_t direction);
static void SYSMENU_HANDL_CALIB_CAT_Type(int8_t direction);
static void SYSMENU_HANDL_CALIB_CICCOMP_192K_SHIFT(int8_t direction);
static void SYSMENU_HANDL_CALIB_CICCOMP_384K_SHIFT(int8_t direction);
static void SYSMENU_HANDL_CALIB_CICCOMP_48K_SHIFT(int8_t direction);
static void SYSMENU_HANDL_CALIB_CICCOMP_96K_SHIFT(int8_t direction);
static void SYSMENU_HANDL_CALIB_DAC_SHIFT(int8_t direction);
static void SYSMENU_HANDL_CALIB_DAC_driver_mode(int8_t direction);
static void SYSMENU_HANDL_CALIB_ENABLE_2200m_band(int8_t direction);
static void SYSMENU_HANDL_CALIB_ENABLE_630m_band(int8_t direction);
static void SYSMENU_HANDL_CALIB_ENABLE_60m_band(int8_t direction);
static void SYSMENU_HANDL_CALIB_ENABLE_6m_band(int8_t direction);
static void SYSMENU_HANDL_CALIB_ENABLE_4m_band(int8_t direction);
static void SYSMENU_HANDL_CALIB_ENABLE_FM_band(int8_t direction);
static void SYSMENU_HANDL_CALIB_ENABLE_2m_band(int8_t direction);
static void SYSMENU_HANDL_CALIB_ENABLE_AIR_band(int8_t direction);
static void SYSMENU_HANDL_CALIB_ENABLE_marine_band(int8_t direction);
static void SYSMENU_HANDL_CALIB_ENABLE_70cm_band(int8_t direction);
static void SYSMENU_HANDL_CALIB_ENABLE_23cm_band(int8_t direction);
static void SYSMENU_HANDL_CALIB_ENCODER2_DEBOUNCE(int8_t direction);
static void SYSMENU_HANDL_CALIB_ENCODER2_INVERT(int8_t direction);
static void SYSMENU_HANDL_CALIB_ENCODER2_ON_FALLING(int8_t direction);
static void SYSMENU_HANDL_CALIB_ENCODER_ACCELERATION(int8_t direction);
static void SYSMENU_HANDL_CALIB_ENCODER_DEBOUNCE(int8_t direction);
static void SYSMENU_HANDL_CALIB_ENCODER_INVERT(int8_t direction);
static void SYSMENU_HANDL_CALIB_ENCODER_SLOW_RATE(int8_t direction);
static void SYSMENU_HANDL_CALIB_EXT_10m(int8_t direction);
static void SYSMENU_HANDL_CALIB_EXT_12m(int8_t direction);
static void SYSMENU_HANDL_CALIB_EXT_15m(int8_t direction);
static void SYSMENU_HANDL_CALIB_EXT_160m(int8_t direction);
static void SYSMENU_HANDL_CALIB_EXT_17m(int8_t direction);
static void SYSMENU_HANDL_CALIB_EXT_20m(int8_t direction);
static void SYSMENU_HANDL_CALIB_EXT_2200m(int8_t direction);
static void SYSMENU_HANDL_CALIB_EXT_630m(int8_t direction);
static void SYSMENU_HANDL_CALIB_EXT_2m(int8_t direction);
static void SYSMENU_HANDL_CALIB_EXT_30m(int8_t direction);
static void SYSMENU_HANDL_CALIB_EXT_40m(int8_t direction);
static void SYSMENU_HANDL_CALIB_EXT_4m(int8_t direction);
static void SYSMENU_HANDL_CALIB_EXT_60m(int8_t direction);
static void SYSMENU_HANDL_CALIB_EXT_6m(int8_t direction);
static void SYSMENU_HANDL_CALIB_EXT_70cm(int8_t direction);
static void SYSMENU_HANDL_CALIB_EXT_80m(int8_t direction);
static void SYSMENU_HANDL_CALIB_EXT_CB(int8_t direction);
static void SYSMENU_HANDL_CALIB_EXT_FM(int8_t direction);
static void SYSMENU_HANDL_CALIB_EXT_13cm(int8_t direction);
static void SYSMENU_HANDL_CALIB_EXT_23cm(int8_t direction);
static void SYSMENU_HANDL_CALIB_EXT_3cm(int8_t direction);
static void SYSMENU_HANDL_CALIB_EXT_1_2cm(int8_t direction);
static void SYSMENU_HANDL_CALIB_EXT_6cm(int8_t direction);
static void SYSMENU_HANDL_CALIB_EXT_QO100(int8_t direction);
static void SYSMENU_HANDL_CALIB_FAN_FULL_START(int8_t direction);
static void SYSMENU_HANDL_CALIB_FAN_MEDIUM_START(int8_t direction);
static void SYSMENU_HANDL_CALIB_FAN_MEDIUM_STOP(int8_t direction);
static void SYSMENU_HANDL_CALIB_FAN_Medium_speed(int8_t direction);
static void SYSMENU_HANDL_CALIB_FM_DEVIATION_SCALE(int8_t direction);
static void SYSMENU_HANDL_CALIB_FlashGT911(int8_t direction);
static void SYSMENU_HANDL_CALIB_HPF_START(int8_t direction);
static void SYSMENU_HANDL_CALIB_IF_GAIN_MAX(int8_t direction);
static void SYSMENU_HANDL_CALIB_IF_GAIN_MIN(int8_t direction);
static void SYSMENU_HANDL_CALIB_LCD_Rotate(int8_t direction);
static void SYSMENU_HANDL_CALIB_LNA_compensation(int8_t direction);
static void SYSMENU_HANDL_CALIB_LPF_END(int8_t direction);
static void SYSMENU_HANDL_CALIB_LinearPowerControl(int8_t direction);
static void SYSMENU_HANDL_CALIB_MAX_ChargePump_Freq(int8_t direction);
static void SYSMENU_HANDL_CALIB_MAX_RF_POWER_ON_METER(int8_t direction);
static void SYSMENU_HANDL_CALIB_NOTX_10m(int8_t direction);
static void SYSMENU_HANDL_CALIB_NOTX_12m(int8_t direction);
static void SYSMENU_HANDL_CALIB_NOTX_15m(int8_t direction);
static void SYSMENU_HANDL_CALIB_NOTX_160m(int8_t direction);
static void SYSMENU_HANDL_CALIB_NOTX_17m(int8_t direction);
static void SYSMENU_HANDL_CALIB_NOTX_20m(int8_t direction);
static void SYSMENU_HANDL_CALIB_NOTX_2200m(int8_t direction);
static void SYSMENU_HANDL_CALIB_NOTX_630m(int8_t direction);
static void SYSMENU_HANDL_CALIB_NOTX_2m(int8_t direction);
static void SYSMENU_HANDL_CALIB_NOTX_30m(int8_t direction);
static void SYSMENU_HANDL_CALIB_NOTX_40m(int8_t direction);
static void SYSMENU_HANDL_CALIB_NOTX_4m(int8_t direction);
static void SYSMENU_HANDL_CALIB_NOTX_60m(int8_t direction);
static void SYSMENU_HANDL_CALIB_NOTX_6m(int8_t direction);
static void SYSMENU_HANDL_CALIB_NOTX_70cm(int8_t direction);
static void SYSMENU_HANDL_CALIB_NOTX_23cm(int8_t direction);
static void SYSMENU_HANDL_CALIB_NOTX_80m(int8_t direction);
static void SYSMENU_HANDL_CALIB_NOTX_CB(int8_t direction);
static void SYSMENU_HANDL_CALIB_NOTX_FM(int8_t direction);
static void SYSMENU_HANDL_CALIB_NOTX_NOTHAM(int8_t direction);
static void SYSMENU_HANDL_CALIB_OTA_update(int8_t direction);
static void SYSMENU_HANDL_CALIB_PWR_CUR_Calibration(int8_t direction);
static void SYSMENU_HANDL_CALIB_PWR_VLT_Calibration(int8_t direction);
static void SYSMENU_HANDL_CALIB_RF_GAIN_10M(int8_t direction);
static void SYSMENU_HANDL_CALIB_RF_GAIN_12M(int8_t direction);
static void SYSMENU_HANDL_CALIB_RF_GAIN_13CM(int8_t direction);
static void SYSMENU_HANDL_CALIB_RF_GAIN_15M(int8_t direction);
static void SYSMENU_HANDL_CALIB_RF_GAIN_160M(int8_t direction);
static void SYSMENU_HANDL_CALIB_RF_GAIN_17M(int8_t direction);
static void SYSMENU_HANDL_CALIB_RF_GAIN_20M(int8_t direction);
static void SYSMENU_HANDL_CALIB_RF_GAIN_2200M(int8_t direction);
static void SYSMENU_HANDL_CALIB_RF_GAIN_630M(int8_t direction);
static void SYSMENU_HANDL_CALIB_RF_GAIN_23CM(int8_t direction);
static void SYSMENU_HANDL_CALIB_RF_GAIN_2M(int8_t direction);
static void SYSMENU_HANDL_CALIB_RF_GAIN_30M(int8_t direction);
static void SYSMENU_HANDL_CALIB_RF_GAIN_3CM(int8_t direction);
static void SYSMENU_HANDL_CALIB_RF_GAIN_1_2CM(int8_t direction);
static void SYSMENU_HANDL_CALIB_RF_GAIN_40M(int8_t direction);
static void SYSMENU_HANDL_CALIB_RF_GAIN_4M(int8_t direction);
static void SYSMENU_HANDL_CALIB_RF_GAIN_60M(int8_t direction);
static void SYSMENU_HANDL_CALIB_RF_GAIN_6CM(int8_t direction);
static void SYSMENU_HANDL_CALIB_RF_GAIN_6M(int8_t direction);
static void SYSMENU_HANDL_CALIB_RF_GAIN_70CM(int8_t direction);
static void SYSMENU_HANDL_CALIB_RF_GAIN_80M(int8_t direction);
static void SYSMENU_HANDL_CALIB_RF_GAIN_CB(int8_t direction);
static void SYSMENU_HANDL_CALIB_RF_GAIN_QO100(int8_t direction);
static void SYSMENU_HANDL_CALIB_RF_unit_type(int8_t direction);
static void SYSMENU_HANDL_CALIB_RTC_CALIBRATION(int8_t direction);
static void SYSMENU_HANDL_CALIB_RTC_COARSE_CALIBRATION(int8_t direction);
static void SYSMENU_HANDL_CALIB_SETTINGS_RESET(int8_t direction);
static void SYSMENU_HANDL_CALIB_SSB_POWER_ADDITION(int8_t direction);
static void SYSMENU_HANDL_CALIB_SWR_FWD_RATE_6M(int8_t direction);
static void SYSMENU_HANDL_CALIB_SWR_FWD_RATE_HF(int8_t direction);
static void SYSMENU_HANDL_CALIB_SWR_FWD_RATE_VHF(int8_t direction);
static void SYSMENU_HANDL_CALIB_SWR_REF_RATE_6M(int8_t direction);
static void SYSMENU_HANDL_CALIB_SWR_REF_RATE_HF(int8_t direction);
static void SYSMENU_HANDL_CALIB_SWR_REF_RATE_VHF(int8_t direction);
static void SYSMENU_HANDL_CALIB_S_METER_HF(int8_t direction);
static void SYSMENU_HANDL_CALIB_S_METER_VHF(int8_t direction);
static void SYSMENU_HANDL_CALIB_TCXO(int8_t direction);
static void SYSMENU_HANDL_CALIB_TOUCHPAD_horizontal_flip(int8_t direction);
static void SYSMENU_HANDL_CALIB_TOUCHPAD_vertical_flip(int8_t direction);
static void SYSMENU_HANDL_CALIB_TRANSV_IF_13cm(int8_t direction);
static void SYSMENU_HANDL_CALIB_TRANSV_IF_23cm(int8_t direction);
static void SYSMENU_HANDL_CALIB_TRANSV_IF_3cm(int8_t direction);
static void SYSMENU_HANDL_CALIB_TRANSV_IF_1_2cm(int8_t direction);
static void SYSMENU_HANDL_CALIB_TRANSV_IF_6cm(int8_t direction);
static void SYSMENU_HANDL_CALIB_TRANSV_IF_70cm(int8_t direction);
static void SYSMENU_HANDL_CALIB_TRANSV_IF_2m(int8_t direction);
static void SYSMENU_HANDL_CALIB_TRANSV_IF_RX_QO100(int8_t direction);
static void SYSMENU_HANDL_CALIB_TRANSV_IF_TX_QO100(int8_t direction);
static void SYSMENU_HANDL_CALIB_TRANSV_OFFSET_Custom(int8_t direction);
static void SYSMENU_HANDL_CALIB_TRANSV_RF_13cm(int8_t direction);
static void SYSMENU_HANDL_CALIB_TRANSV_RF_23cm(int8_t direction);
static void SYSMENU_HANDL_CALIB_TRANSV_RF_3cm(int8_t direction);
static void SYSMENU_HANDL_CALIB_TRANSV_RF_1_2cm(int8_t direction);
static void SYSMENU_HANDL_CALIB_TRANSV_RF_6cm(int8_t direction);
static void SYSMENU_HANDL_CALIB_TRANSV_RF_70cm(int8_t direction);
static void SYSMENU_HANDL_CALIB_TRANSV_RF_2m(int8_t direction);
static void SYSMENU_HANDL_CALIB_TRANSV_RF_QO100(int8_t direction);
static void SYSMENU_HANDL_CALIB_TRX_MAX_RF_TEMP(int8_t direction);
static void SYSMENU_HANDL_CALIB_TRX_MAX_SWR(int8_t direction);
static void SYSMENU_HANDL_CALIB_TUNE_MAX_POWER(int8_t direction);
static void SYSMENU_HANDL_CALIB_TXCICCOMP_SHIFT(int8_t direction);
static void SYSMENU_HANDL_CALIB_TX_StartDelay(int8_t direction);
static void SYSMENU_HANDL_CALIB_TangentType(int8_t direction);
static void SYSMENU_HANDL_CALIB_TwoSignalTune_Balance(int8_t direction);
static void SYSMENU_HANDL_CALIB_VCXO(int8_t direction);
static void SYSMENU_HANDL_CALIB_WIFI_RESET(int8_t direction);
static void SYSMENU_HANDL_CALIB_INA226_Shunt_mOhm(int8_t direction);
static void SYSMENU_HANDL_CALIB_INA226_VoltageOffset(int8_t direction);
static void SYSMENU_HANDL_CALIB_INA226_PWR_MON(int8_t direction);
static void SYSMENU_HANDL_CALIB_KTY81_Calibration(int8_t direction);
static void SYSMENU_HANDL_CALIB_TOUCHPAD_TIMEOUT(int8_t direction);
static void SYSMENU_HANDL_CALIB_TOUCHPAD_CLICK_THRESHOLD(int8_t direction);
static void SYSMENU_HANDL_CALIB_TOUCHPAD_CLICK_TIMEOUT(int8_t direction);
static void SYSMENU_HANDL_CALIB_TOUCHPAD_HOLD_TIMEOUT(int8_t direction);
static void SYSMENU_HANDL_CALIB_TOUCHPAD_SWIPE_THRESHOLD_PX(int8_t direction);
static void SYSMENU_HANDL_CALIB_COM_CAT_DTR_Mode(int8_t direction);
static void SYSMENU_HANDL_CALIB_COM_CAT_RTS_Mode(int8_t direction);
static void SYSMENU_HANDL_CALIB_COM_DEBUG_DTR_Mode(int8_t direction);
static void SYSMENU_HANDL_CALIB_COM_DEBUG_RTS_Mode(int8_t direction);
static void SYSMENU_HANDL_CALIB_Swap_USB_IQ(int8_t direction);
static void SYSMENU_HANDL_CALIB_ATT_compensation(int8_t direction);

static void SYSMENU_HANDL_TRXMENU(int8_t direction);
static void SYSMENU_HANDL_FILTERMENU(int8_t direction);
static void SYSMENU_HANDL_RXMENU(int8_t direction);
static void SYSMENU_HANDL_TXMENU(int8_t direction);
static void SYSMENU_HANDL_CWMENU(int8_t direction);
static void SYSMENU_HANDL_LCDMENU(int8_t direction);
static void SYSMENU_HANDL_DECODERSMENU(int8_t direction);
static void SYSMENU_HANDL_CALIBRATIONMENU(int8_t direction);

#if HRDW_HAS_WIFI
static void SYSMENU_HANDL_WIFIMENU(int8_t direction);
static void SYSMENU_HANDL_DX_CLUSTER(int8_t direction);
static void SYSMENU_HANDL_RDA_STATS(int8_t direction);
static void SYSMENU_HANDL_PROPAGATION(int8_t direction);
static void SYSMENU_HANDL_TROPO(int8_t direction);
static void SYSMENU_HANDL_DAYNIGHT_MAP(int8_t direction);
static void SYSMENU_HANDL_IONOGRAM(int8_t direction);
#endif
static void SYSMENU_HANDL_SPECTRUMMENU(int8_t direction);
static void SYSMENU_HANDL_SWR_ANALYSER_MENU(int8_t direction);
static void SYSMENU_HANDL_WSPRMENU(int8_t direction);
#if HRDW_HAS_SD
static void SYSMENU_HANDL_SDMENU(int8_t direction);
static void SYSMENU_HANDL_RECORD_CQ_WAV(int8_t direction);

static void SYSMENU_HANDL_SATMENU(int8_t direction);
#endif
static void SYSMENU_HANDL_FT8_Decoder(int8_t direction);     // Tisho
static void SYSMENU_HANDL_SWR_Tandem_Ctrl(int8_t direction); // Tisho
static void SYSMENU_HANDL_LOCATOR_INFO(int8_t direction);
static void SYSMENU_HANDL_CALLSIGN_INFO(int8_t direction);
static void SYSMENU_HANDL_SELF_TEST(int8_t direction);
static void SYSMENU_HANDL_AUTO_CALIBRATION(int8_t direction);

static void SYSMENU_HANDL_SPECTRUM_Begin(int8_t direction);
static void SYSMENU_HANDL_SPECTRUM_Start(int8_t direction);
static void SYSMENU_HANDL_SPECTRUM_End(int8_t direction);
static void SYSMENU_HANDL_SPECTRUM_TopDBM(int8_t direction);
static void SYSMENU_HANDL_SPECTRUM_BottomDBM(int8_t direction);

static void SYSMENU_HANDL_SWR_BAND_START(int8_t direction);
static void SYSMENU_HANDL_SWR_HF_START(int8_t direction);
static void SYSMENU_HANDL_SWR_CUSTOM_Begin(int8_t direction);
static void SYSMENU_HANDL_SWR_CUSTOM_Start(int8_t direction);
static void SYSMENU_HANDL_SWR_CUSTOM_End(int8_t direction);

static void SYSMENU_HANDL_WSPR_Start(int8_t direction);
static void SYSMENU_HANDL_WSPR_FREQ_OFFSET(int8_t direction);
static void SYSMENU_HANDL_WSPR_BAND160(int8_t direction);
static void SYSMENU_HANDL_WSPR_BAND80(int8_t direction);
static void SYSMENU_HANDL_WSPR_BAND40(int8_t direction);
static void SYSMENU_HANDL_WSPR_BAND30(int8_t direction);
static void SYSMENU_HANDL_WSPR_BAND20(int8_t direction);
static void SYSMENU_HANDL_WSPR_BAND17(int8_t direction);
static void SYSMENU_HANDL_WSPR_BAND15(int8_t direction);
static void SYSMENU_HANDL_WSPR_BAND12(int8_t direction);
static void SYSMENU_HANDL_WSPR_BAND10(int8_t direction);
static void SYSMENU_HANDL_WSPR_BAND6(int8_t direction);
static void SYSMENU_HANDL_WSPR_BAND2(int8_t direction);

static void SYSMENU_HANDL_AUTO_CALIBRATION_SWR(int8_t direction);
static void SYSMENU_HANDL_AUTO_CALIBRATION_POWER(int8_t direction);

static void SYSMENU_HANDL_TIME_BEACON(int8_t direction);
static void SYSMENU_HANDL_TIME_BEACON_40kHz(int8_t direction);
static void SYSMENU_HANDL_TIME_BEACON_50kHz(int8_t direction);
static void SYSMENU_HANDL_TIME_BEACON_60kHz(int8_t direction);
static void SYSMENU_HANDL_TIME_BEACON_66_66kHz(int8_t direction);
static void SYSMENU_HANDL_TIME_BEACON_75kHz(int8_t direction);
static void SYSMENU_HANDL_TIME_BEACON_77_5kHz(int8_t direction);
static void SYSMENU_HANDL_TIME_BEACON_2_5MHz(int8_t direction);
static void SYSMENU_HANDL_TIME_BEACON_4_996MHz(int8_t direction);
static void SYSMENU_HANDL_TIME_BEACON_5MHz(int8_t direction);
static void SYSMENU_HANDL_TIME_BEACON_9_996MHz(int8_t direction);
static void SYSMENU_HANDL_TIME_BEACON_10MHz(int8_t direction);
static void SYSMENU_HANDL_TIME_BEACON_14_996MHz(int8_t direction);
static void SYSMENU_HANDL_TIME_BEACON_15MHz(int8_t direction);
static void SYSMENU_HANDL_TIME_BEACON_20MHz(int8_t direction);

static bool SYSMENU_HANDL_CHECK_HAS_LPF(void);
static bool SYSMENU_HANDL_CHECK_HAS_HPF(void);
static bool SYSMENU_HANDL_CHECK_HAS_BPF_8(void);
static bool SYSMENU_HANDL_CHECK_HAS_BPF_9(void);
static bool SYSMENU_HANDL_CHECK_HAS_RFFILTERS_BYPASS(void);
static bool SYSMENU_HANDL_CHECK_HIDDEN_ENABLED(void);

static void SYSMENU_HANDL_MEMORY_CHANNELS_MENU(int8_t direction);
#if MEMORY_CHANNELS_COUNT > 0
static void SYSMENU_HANDL_MEMORY_CHANNELS_0(int8_t direction);
static void SYSMENU_HANDL_MEMORY_CHANNELS_1(int8_t direction);
static void SYSMENU_HANDL_MEMORY_CHANNELS_2(int8_t direction);
static void SYSMENU_HANDL_MEMORY_CHANNELS_3(int8_t direction);
static void SYSMENU_HANDL_MEMORY_CHANNELS_4(int8_t direction);
static void SYSMENU_HANDL_MEMORY_CHANNELS_5(int8_t direction);
static void SYSMENU_HANDL_MEMORY_CHANNELS_6(int8_t direction);
static void SYSMENU_HANDL_MEMORY_CHANNELS_7(int8_t direction);
static void SYSMENU_HANDL_MEMORY_CHANNELS_8(int8_t direction);
static void SYSMENU_HANDL_MEMORY_CHANNELS_9(int8_t direction);
#endif
#if MEMORY_CHANNELS_COUNT > 10
static void SYSMENU_HANDL_MEMORY_CHANNELS_10(int8_t direction);
static void SYSMENU_HANDL_MEMORY_CHANNELS_11(int8_t direction);
static void SYSMENU_HANDL_MEMORY_CHANNELS_12(int8_t direction);
static void SYSMENU_HANDL_MEMORY_CHANNELS_13(int8_t direction);
static void SYSMENU_HANDL_MEMORY_CHANNELS_14(int8_t direction);
static void SYSMENU_HANDL_MEMORY_CHANNELS_15(int8_t direction);
static void SYSMENU_HANDL_MEMORY_CHANNELS_16(int8_t direction);
static void SYSMENU_HANDL_MEMORY_CHANNELS_17(int8_t direction);
static void SYSMENU_HANDL_MEMORY_CHANNELS_18(int8_t direction);
static void SYSMENU_HANDL_MEMORY_CHANNELS_19(int8_t direction);
#endif
#if MEMORY_CHANNELS_COUNT > 20
static void SYSMENU_HANDL_MEMORY_CHANNELS_20(int8_t direction);
static void SYSMENU_HANDL_MEMORY_CHANNELS_21(int8_t direction);
static void SYSMENU_HANDL_MEMORY_CHANNELS_22(int8_t direction);
static void SYSMENU_HANDL_MEMORY_CHANNELS_23(int8_t direction);
static void SYSMENU_HANDL_MEMORY_CHANNELS_24(int8_t direction);
static void SYSMENU_HANDL_MEMORY_CHANNELS_25(int8_t direction);
static void SYSMENU_HANDL_MEMORY_CHANNELS_26(int8_t direction);
static void SYSMENU_HANDL_MEMORY_CHANNELS_27(int8_t direction);
static void SYSMENU_HANDL_MEMORY_CHANNELS_28(int8_t direction);
static void SYSMENU_HANDL_MEMORY_CHANNELS_29(int8_t direction);
#endif
#if MEMORY_CHANNELS_COUNT > 30
static void SYSMENU_HANDL_MEMORY_CHANNELS_30(int8_t direction);
static void SYSMENU_HANDL_MEMORY_CHANNELS_31(int8_t direction);
static void SYSMENU_HANDL_MEMORY_CHANNELS_32(int8_t direction);
static void SYSMENU_HANDL_MEMORY_CHANNELS_33(int8_t direction);
static void SYSMENU_HANDL_MEMORY_CHANNELS_34(int8_t direction);
#endif

#ifdef LCD_SMALL_INTERFACE
#ifdef LAY_320x240
#define interactive_menu_top 54
#else
#define interactive_menu_top 46
#endif
#else
#define interactive_menu_top 54
#endif

const static struct sysmenu_item_handler sysmenu_handlers[] = {
    {"TRX Settings", SYSMENU_MENU, NULL, 0, SYSMENU_HANDL_TRXMENU},
    {"FILTERS Settings", SYSMENU_MENU, NULL, 0, SYSMENU_HANDL_FILTERMENU},
    {"RX Settings", SYSMENU_MENU, NULL, 0, SYSMENU_HANDL_RXMENU},
    {"TX Settings", SYSMENU_MENU, NULL, 0, SYSMENU_HANDL_TXMENU},
    {"CW Settings", SYSMENU_MENU, NULL, 0, SYSMENU_HANDL_CWMENU},
    {"SCREEN Settings", SYSMENU_MENU, NULL, 0, SYSMENU_HANDL_LCDMENU},
    {"Decoders", SYSMENU_MENU, NULL, 0, SYSMENU_HANDL_DECODERSMENU},
#if HRDW_HAS_WIFI
    {"WIFI Settings", SYSMENU_MENU, NULL, 0, SYSMENU_HANDL_WIFIMENU},
#endif
#if HRDW_HAS_SD
    {"SD Card", SYSMENU_MENU, NULL, 0, SYSMENU_HANDL_SDMENU},
    {"Satellites", SYSMENU_MENU, NULL, 0, SYSMENU_HANDL_SATMENU},
#endif
#if MEMORY_CHANNELS_COUNT > 0
    {"Channels Name", SYSMENU_RUN, NULL, 0, SYSMENU_HANDL_MEMORY_CHANNELS_MENU},
#endif
    {"Set Clock Time", SYSMENU_RUN, NULL, 0, SYSMENU_HANDL_SETTIME},
    {"DFU Mode", SYSMENU_RUN, NULL, 0, SYSMENU_HANDL_Bootloader},
#if HRDW_HAS_SD
    {"OTA Update", SYSMENU_RUN, NULL, 0, SYSMENU_HANDL_OTA_Update},
#endif
    {"Services", SYSMENU_RUN, NULL, 0, SYSMENU_HANDL_SERVICESMENU},
    {"System info", SYSMENU_RUN, NULL, 0, SYSMENU_HANDL_SYSINFO},
    {"Support project", SYSMENU_RUN, NULL, 0, SYSMENU_HANDL_SUPPORT},
    {"Calibration", SYSMENU_MENU, SYSMENU_HANDL_CHECK_HIDDEN_ENABLED, 0, SYSMENU_HANDL_CALIBRATIONMENU},
};

const static struct sysmenu_item_handler sysmenu_trx_handlers[] = {
    {"Band Map", SYSMENU_BOOLEAN, NULL, (uint32_t *)&TRX.BandMapEnabled, SYSMENU_HANDL_TRX_BandMap},
    {"Beeper", SYSMENU_BOOLEAN, NULL, (uint32_t *)&TRX.Beeper, SYSMENU_HANDL_TRX_Beeper},
    {"Callsign", SYSMENU_RUN, NULL, 0, SYSMENU_HANDL_TRX_SetCallsign},
    {"Channel Mode", SYSMENU_BOOLEAN, NULL, (uint32_t *)&TRX.ChannelMode, SYSMENU_HANDL_TRX_ChannelMode},
#if HRDW_HAS_USB_DEBUG || HRDW_DEBUG_ON_CAT_PORT
    {"Debug console", SYSMENU_ENUM, NULL, (uint32_t *)&TRX.Debug_Type, SYSMENU_HANDL_TRX_DEBUG_TYPE, (const enumerate_item[7]){"OFF", "SYSTEM", "WIFI", "BUTTONS", "TOUCH", "CAT", "I2C"}},
#endif
    {"Encoder Accelerate", SYSMENU_BOOLEAN, NULL, (uint32_t *)&TRX.Encoder_Accelerate, SYSMENU_HANDL_TRX_ENC_ACCELERATE},
    {"Freq Step CW", SYSMENU_UINT32R, NULL, (uint32_t *)&TRX.FRQ_STEP_CW_Hz, SYSMENU_HANDL_TRX_FRQ_STEP_CW_Hz},
    {"Freq Step SSB", SYSMENU_UINT32R, NULL, (uint32_t *)&TRX.FRQ_STEP_SSB_Hz, SYSMENU_HANDL_TRX_FRQ_STEP_SSB_Hz},
    {"Freq Step DIGI", SYSMENU_UINT32R, NULL, (uint32_t *)&TRX.FRQ_STEP_DIGI_Hz, SYSMENU_HANDL_TRX_FRQ_STEP_DIGI_Hz},
    {"Freq Step AM", SYSMENU_UINT32R, NULL, (uint32_t *)&TRX.FRQ_STEP_AM_Hz, SYSMENU_HANDL_TRX_FRQ_STEP_AM_Hz},
    {"Freq Step FM", SYSMENU_UINT32R, NULL, (uint32_t *)&TRX.FRQ_STEP_FM_Hz, SYSMENU_HANDL_TRX_FRQ_STEP_FM_Hz},
    {"Freq Step WFM", SYSMENU_UINT32R, NULL, (uint32_t *)&TRX.FRQ_STEP_WFM_Hz, SYSMENU_HANDL_TRX_FRQ_STEP_WFM_Hz},
    {"FAST Step Mult", SYSMENU_UINT8, NULL, (uint32_t *)&TRX.FAST_STEP_Multiplier, SYSMENU_HANDL_TRX_FAST_STEP_Multiplier},
    {"ENC2 Step Mult", SYSMENU_UINT8, NULL, (uint32_t *)&TRX.ENC2_STEP_Multiplier, SYSMENU_HANDL_TRX_ENC2_STEP_Multiplier},
    {"Notch Step, Hz", SYSMENU_FLOAT32, NULL, (uint32_t *)&TRX.NOTCH_STEP_Hz, SYSMENU_HANDL_TRX_NOTCH_STEP_Hz},
    {"Full Duplex", SYSMENU_BOOLEAN, NULL, (uint32_t *)&TRX.Full_Duplex, SYSMENU_HANDL_TRX_Full_Duplex},
    {"Locator", SYSMENU_RUN, NULL, 0, SYSMENU_HANDL_TRX_SetLocator},
    {"RIT Interval", SYSMENU_UINT16, NULL, (uint32_t *)&TRX.RIT_INTERVAL, SYSMENU_HANDL_TRX_RIT_INTERVAL},
    {"XIT Interval", SYSMENU_UINT16, NULL, (uint32_t *)&TRX.XIT_INTERVAL, SYSMENU_HANDL_TRX_XIT_INTERVAL},
#if !defined(FRONTPANEL_LITE) && !defined(FRONTPANEL_X1) && !defined(FRONTPANEL_WOLF_2)
    {"Fine RIT Tune", SYSMENU_BOOLEAN, NULL, (uint32_t *)&TRX.FineRITTune, SYSMENU_HANDL_TRX_FineRITTune},
#endif
    {"Split freq sync", SYSMENU_BOOLEAN, NULL, (uint32_t *)&TRX.Split_Mode_Sync_Freq, SYSMENU_HANDL_TRX_Split_Mode_Sync_Freq},
    {"Transverter 2m", SYSMENU_BOOLEAN, NULL, (uint32_t *)&TRX.Transverter_2m, SYSMENU_HANDL_TRX_TRANSV_2M},
    {"Transverter 70cm", SYSMENU_BOOLEAN, NULL, (uint32_t *)&TRX.Transverter_70cm, SYSMENU_HANDL_TRX_TRANSV_70CM},
    {"Transverter 23cm", SYSMENU_BOOLEAN, NULL, (uint32_t *)&TRX.Transverter_23cm, SYSMENU_HANDL_TRX_TRANSV_23CM},
    {"Transverter 13cm", SYSMENU_BOOLEAN, NULL, (uint32_t *)&TRX.Transverter_13cm, SYSMENU_HANDL_TRX_TRANSV_13CM},
    {"Transverter 6cm", SYSMENU_BOOLEAN, NULL, (uint32_t *)&TRX.Transverter_6cm, SYSMENU_HANDL_TRX_TRANSV_6CM},
    {"Transverter 3cm", SYSMENU_BOOLEAN, NULL, (uint32_t *)&TRX.Transverter_3cm, SYSMENU_HANDL_TRX_TRANSV_3CM},
    {"Transverter QO-100", SYSMENU_BOOLEAN, NULL, (uint32_t *)&TRX.Transverter_QO100, SYSMENU_HANDL_TRX_TRANSV_QO100},
    {"Transverter 1.2cm", SYSMENU_BOOLEAN, NULL, (uint32_t *)&TRX.Transverter_1_2cm, SYSMENU_HANDL_TRX_TRANSV_1_2CM},
    {"Custom Transverter", SYSMENU_BOOLEAN, NULL, (uint32_t *)&TRX.Custom_Transverter_Enabled, SYSMENU_HANDL_TRX_TRANSV_ENABLE},
#if HRDW_HAS_WIFI
    {"URSI Code", SYSMENU_RUN, NULL, 0, SYSMENU_HANDL_TRX_SetURSICode},
    {"Tropo Region", SYSMENU_ENUM, NULL, (uint32_t *)&TRX.TROPO_Region, SYSMENU_HANDL_TRX_TROPO_Region,
     (const enumerate_item[23]){"EEU", "EUR", "NWE", "NCA", "MID", "SEA", "NEA", "WAM", "EAM", "NSA", "SAM", "EAS",
                                "OCE", "INO", "AFI", "ENP", "ESP", "CAR", "SAT", "NAT", "ENT", "AUS", "WNP"}},
#endif
};

const static struct sysmenu_item_handler sysmenu_filter_handlers[] = {
    {"AM LPF RX Pass", SYSMENU_UINT16, NULL, (uint32_t *)&TRX.AM_LPF_RX_Filter_shadow, SYSMENU_HANDL_FILTER_AM_LPF_RX_pass},
    {"AM LPF TX Pass", SYSMENU_UINT16, NULL, (uint32_t *)&TRX.AM_LPF_TX_Filter_shadow, SYSMENU_HANDL_FILTER_AM_LPF_TX_pass},
    {"AM/FM LPF Stages", SYSMENU_UINT8, NULL, (uint32_t *)&TRX.AMFM_LPF_Stages, SYSMENU_HANDL_FILTER_AMFM_LPF_Stages},
    {"CW Gauss filter", SYSMENU_BOOLEAN, NULL, (uint32_t *)&TRX.CW_GaussFilter, SYSMENU_HANDL_FILTER_CW_GaussFilter},
    {"CW LPF Pass", SYSMENU_UINT16, NULL, (uint32_t *)&TRX.CW_LPF_Filter_shadow, SYSMENU_HANDL_FILTER_CW_LPF_pass},
    {"CW LPF Stages", SYSMENU_UINT8, NULL, (uint32_t *)&TRX.CW_LPF_Stages, SYSMENU_HANDL_FILTER_CW_LPF_Stages},
    {"DIGI LPF Pass", SYSMENU_UINT16, NULL, (uint32_t *)&TRX.DIGI_LPF_Filter_shadow, SYSMENU_HANDL_FILTER_DIGI_LPF_pass},
    {"DIGI HPF Pass", SYSMENU_UINT16, NULL, (uint32_t *)&TRX.DIGI_HPF_Filter_shadow, SYSMENU_HANDL_FILTER_DIGI_HPF_pass},
    {"FM HPF RX Pass", SYSMENU_UINT16, NULL, (uint32_t *)&TRX.FM_HPF_RX_Filter_shadow, SYSMENU_HANDL_FILTER_FM_HPF_RX_pass},
    {"FM LPF RX Pass", SYSMENU_UINT16, NULL, (uint32_t *)&TRX.FM_LPF_RX_Filter_shadow, SYSMENU_HANDL_FILTER_FM_LPF_RX_pass},
    {"FM LPF TX Pass", SYSMENU_UINT16, NULL, (uint32_t *)&TRX.FM_LPF_TX_Filter_shadow, SYSMENU_HANDL_FILTER_FM_LPF_TX_pass},
    {"SSB HPF RX Pass", SYSMENU_UINT16, NULL, (uint32_t *)&TRX.SSB_HPF_RX_Filter_shadow, SYSMENU_HANDL_FILTER_SSB_HPF_RX_pass},
    {"SSB HPF TX Pass", SYSMENU_UINT16, NULL, (uint32_t *)&TRX.SSB_HPF_TX_Filter_shadow, SYSMENU_HANDL_FILTER_SSB_HPF_TX_pass},
    {"SSB LPF RX Pass", SYSMENU_UINT16, NULL, (uint32_t *)&TRX.SSB_LPF_RX_Filter_shadow, SYSMENU_HANDL_FILTER_SSB_LPF_RX_pass},
    {"SSB LPF TX Pass", SYSMENU_UINT16, NULL, (uint32_t *)&TRX.SSB_LPF_TX_Filter_shadow, SYSMENU_HANDL_FILTER_SSB_LPF_TX_pass},
    {"SSB LPF Stages", SYSMENU_UINT8, NULL, (uint32_t *)&TRX.SSB_LPF_Stages, SYSMENU_HANDL_FILTER_SSB_LPF_Stages},
    {"NOTCH Filter width", SYSMENU_UINT16, NULL, (uint32_t *)&TRX.NOTCH_Filter_width, SYSMENU_HANDL_FILTER_NOTCH_Filter_width},
};

const static struct sysmenu_item_handler sysmenu_rx_handlers[] = {
#if defined(FRONTPANEL_X1) || defined(FRONTPANEL_LITE) || defined(FRONTPANEL_MINI)
    {"Volume", SYSMENU_UINT8, NULL, (uint32_t *)&TRX.Volume, SYSMENU_HANDL_RX_Volume},
    {"Volume Step", SYSMENU_UINT8, NULL, (uint32_t *)&TRX.Volume_Step, SYSMENU_HANDL_RX_Volume_Step},
#endif
    {"IF Gain, dB", SYSMENU_UINT8, NULL, (uint32_t *)&TRX.IF_Gain, SYSMENU_HANDL_RX_IFGain},
    {"ADC Driver", SYSMENU_BOOLEAN, NULL, (uint32_t *)&TRX.ADC_Driver, SYSMENU_HANDL_RX_ADC_DRIVER},
#if defined(FRONTPANEL_NONE) || defined(FRONTPANEL_SMALL_V1) || defined(FRONTPANEL_BIG_V1) || defined(FRONTPANEL_KT_100S) || defined(FRONTPANEL_WF_100D) || defined(FRONTPANEL_WOLF_2) || \
    defined(FRONTPANEL_X1) || defined(FRONTPANEL_MINI)
    {"ADC Dither", SYSMENU_BOOLEAN, NULL, (uint32_t *)&TRX.ADC_DITH, SYSMENU_HANDL_RX_ADC_DITH},
    {"ADC Preamp", SYSMENU_BOOLEAN, NULL, (uint32_t *)&TRX.ADC_PGA, SYSMENU_HANDL_RX_ADC_PGA},
    {"ADC Randomizer", SYSMENU_BOOLEAN, NULL, (uint32_t *)&TRX.ADC_RAND, SYSMENU_HANDL_RX_ADC_RAND},
#endif
    {"ADC Shutdown", SYSMENU_BOOLEAN, NULL, (uint32_t *)&TRX.ADC_SHDN, SYSMENU_HANDL_RX_ADC_SHDN},
    {"AGC", SYSMENU_BOOLEAN, NULL, (uint32_t *)&TRX.AGC_shadow, SYSMENU_HANDL_RX_AGC},
#ifdef LAY_320x240
    {"AGC Gain tr SSB", SYSMENU_INT8, NULL, (uint32_t *)&TRX.AGC_Gain_target_SSB, SYSMENU_HANDL_RX_AGC_Gain_target_SSB},
    {"AGC Gain tr CW", SYSMENU_INT8, NULL, (uint32_t *)&TRX.AGC_Gain_target_CW, SYSMENU_HANDL_RX_AGC_Gain_target_CW},
#else
    {"AGC Gain targ SSB", SYSMENU_INT8, NULL, (uint32_t *)&TRX.AGC_Gain_target_SSB, SYSMENU_HANDL_RX_AGC_Gain_target_SSB},
    {"AGC Gain targ CW", SYSMENU_INT8, NULL, (uint32_t *)&TRX.AGC_Gain_target_CW, SYSMENU_HANDL_RX_AGC_Gain_target_CW},
#endif
    {"AGC Spectral", SYSMENU_BOOLEAN, NULL, (uint32_t *)&TRX.AGC_Spectral, SYSMENU_HANDL_RX_AGC_Spectral},
    {"AGC Threshold", SYSMENU_BOOLEAN, NULL, (uint32_t *)&TRX.AGC_Threshold, SYSMENU_HANDL_RX_AGC_Threshold},
#if defined(FRONTPANEL_NONE) || defined(FRONTPANEL_SMALL_V1) || defined(FRONTPANEL_LITE) || defined(FRONTPANEL_BIG_V1) || defined(FRONTPANEL_KT_100S) || defined(FRONTPANEL_WF_100D) || \
    defined(FRONTPANEL_WOLF_2) || defined(FRONTPANEL_X1) || defined(FRONTPANEL_MINI)
    {"Att step, dB", SYSMENU_UINT8, NULL, (uint32_t *)&TRX.ATT_STEP, SYSMENU_HANDL_RX_ATT_STEP},
    {"Attenuation, dB", SYSMENU_FLOAT32, NULL, (uint32_t *)&TRX.ATT_DB, SYSMENU_HANDL_RX_ATT_DB},
#endif
    {"Auto Snap", SYSMENU_BOOLEAN, NULL, (uint32_t *)&TRX.Auto_Snap, SYSMENU_HANDL_RX_Auto_Snap},
    {"AutoGainer", SYSMENU_BOOLEAN, NULL, (uint32_t *)&TRX.AutoGain, SYSMENU_HANDL_RX_AutoGain},
#if HRDW_HAS_DUAL_RX
    {"A/B Balance", SYSMENU_INT8, NULL, (uint32_t *)&TRX.Dual_RX_AB_Balance, SYSMENU_HANDL_RX_Dual_RX_AB_Balance},
#endif
#if HRDW_HAS_BLUETOOTH_AUDIO
    {"Bluetooth Audio", SYSMENU_BOOLEAN, NULL, (uint32_t *)&TRX.BluetoothAudio_Enabled, SYSMENU_HANDL_RX_BluetoothAudio_Enabled},
#endif
    {"CODEC Gain", SYSMENU_UINT8, NULL, (uint32_t *)&TRX.CODEC_Out_Volume, SYSMENU_HANDL_RX_CODEC_Out_Volume},
    {"DNR", SYSMENU_ENUM, NULL, (uint32_t *)&TRX.DNR_shadow, SYSMENU_HANDL_RX_DNR, (const enumerate_item[3]){"OFF", "DNR1", "DNR2"}},
    {"DNR Average", SYSMENU_UINT8, NULL, (uint32_t *)&TRX.DNR_AVERAGE, SYSMENU_HANDL_RX_DNR_AVERAGE},
    {"DNR Minimal", SYSMENU_UINT8, NULL, (uint32_t *)&TRX.DNR_MINIMAL, SYSMENU_HANDL_RX_DNR_MINMAL},
    {"DNR1 Threshold", SYSMENU_UINT8, NULL, (uint32_t *)&TRX.DNR1_SNR_THRESHOLD, SYSMENU_HANDL_RX_DNR1_THRES},
#if !defined(FRONTPANEL_LITE)
    {"DNR2 Threshold", SYSMENU_UINT8, NULL, (uint32_t *)&TRX.DNR2_SNR_THRESHOLD, SYSMENU_HANDL_RX_DNR2_THRES},
#endif
    {"Squelch", SYSMENU_BOOLEAN, NULL, (uint32_t *)&TRX.SQL_shadow, SYSMENU_HANDL_RX_Squelch},
#ifdef LAY_320x240
    {"FM Squelch level", SYSMENU_INT16, NULL, (uint32_t *)&TRX.FM_SQL_threshold_dBm_shadow, SYSMENU_HANDL_RX_FMSquelch},
#else
    {"FM Squelch level, dBm", SYSMENU_INT16, NULL, (uint32_t *)&TRX.FM_SQL_threshold_dBm_shadow, SYSMENU_HANDL_RX_FMSquelch},
#endif
    {"Free tune", SYSMENU_BOOLEAN, NULL, (uint32_t *)&TRX.FREE_Tune, SYSMENU_HANDL_RX_FREE_Tune},
    {"Center After Idle", SYSMENU_BOOLEAN, NULL, (uint32_t *)&TRX.CenterSpectrumAfterIdle, SYSMENU_HANDL_RX_CenterAfterIdle},
    {"Noise blanker 1", SYSMENU_BOOLEAN, NULL, (uint32_t *)&TRX.NOISE_BLANKER1, SYSMENU_HANDL_RX_NOISE_BLANKER1},
    {"NB1 Threshold", SYSMENU_UINT8, NULL, (uint32_t *)&TRX.NOISE_BLANKER1_THRESHOLD, SYSMENU_HANDL_RX_NOISE_BLANKER1_THRESHOLD},
    {"Noise blanker 2", SYSMENU_BOOLEAN, NULL, (uint32_t *)&TRX.NOISE_BLANKER2, SYSMENU_HANDL_RX_NOISE_BLANKER2},
    {"NB2 Threshold", SYSMENU_UINT8, NULL, (uint32_t *)&TRX.NOISE_BLANKER2_THRESHOLD, SYSMENU_HANDL_RX_NOISE_BLANKER2_THRESHOLD},
#if !defined(FRONTPANEL_LITE)
    {"RF Filters", SYSMENU_BOOLEAN, SYSMENU_HANDL_CHECK_HAS_RFFILTERS_BYPASS, (uint32_t *)&TRX.RF_Filters, SYSMENU_HANDL_RX_RFFilters},
#endif
    {"RX AUDIO Mode", SYSMENU_ENUM, NULL, (uint32_t *)&TRX.RX_AUDIO_MODE, SYSMENU_HANDL_RX_AUDIO_MODE, (const enumerate_item[3]){"STEREO", "LEFT", "RIGHT"}},
    {"RX AGC CW Speed", SYSMENU_UINT8, NULL, (uint32_t *)&TRX.RX_AGC_CW_speed, SYSMENU_HANDL_RX_AGC_CW_Speed},
    {"RX AGC SSB Speed", SYSMENU_UINT8, NULL, (uint32_t *)&TRX.RX_AGC_SSB_speed, SYSMENU_HANDL_RX_AGC_SSB_Speed},
    {"RX AGC Max gain", SYSMENU_UINT8, NULL, (uint32_t *)&TRX.RX_AGC_Max_gain, SYSMENU_HANDL_RX_AGC_Max_gain},
    {"RX AGC Hold time", SYSMENU_UINT16, NULL, (uint32_t *)&TRX.RX_AGC_Hold_Time, SYSMENU_HANDL_RX_AGC_Hold_Time},
    {"RX AGC Hold limit", SYSMENU_UINT16, NULL, (uint32_t *)&TRX.RX_AGC_Hold_Limiter, SYSMENU_HANDL_RX_AGC_Hold_Limiter},
    {"RX AGC Hold st up", SYSMENU_UINT16, NULL, (uint32_t *)&TRX.RX_AGC_Hold_Step_Up, SYSMENU_HANDL_RX_AGC_Hold_Step_Up},
    {"RX AGC Hold st dw", SYSMENU_UINT16, NULL, (uint32_t *)&TRX.RX_AGC_Hold_Step_Down, SYSMENU_HANDL_RX_AGC_Hold_Step_Down},
    {"RX EQ 0.3k", SYSMENU_INT8, NULL, (uint32_t *)&TRX.RX_EQ_P1, SYSMENU_HANDL_RX_EQ_P1},
    {"RX EQ 0.7k", SYSMENU_INT8, NULL, (uint32_t *)&TRX.RX_EQ_P2, SYSMENU_HANDL_RX_EQ_P2},
    {"RX EQ 1.2k", SYSMENU_INT8, NULL, (uint32_t *)&TRX.RX_EQ_P3, SYSMENU_HANDL_RX_EQ_P3},
    {"RX EQ 1.8k", SYSMENU_INT8, NULL, (uint32_t *)&TRX.RX_EQ_P4, SYSMENU_HANDL_RX_EQ_P4},
    {"RX EQ 2.0k", SYSMENU_INT8, NULL, (uint32_t *)&TRX.RX_EQ_P5, SYSMENU_HANDL_RX_EQ_P5},
    {"RX EQ 2.5k", SYSMENU_INT8, NULL, (uint32_t *)&TRX.RX_EQ_P6, SYSMENU_HANDL_RX_EQ_P6},
    {"RX WFM EQ 50Hz", SYSMENU_INT8, NULL, (uint32_t *)&TRX.RX_EQ_P1_WFM, SYSMENU_HANDL_RX_EQ_P1_WFM},
    {"RX WFM EQ 0.3k", SYSMENU_INT8, NULL, (uint32_t *)&TRX.RX_EQ_P2_WFM, SYSMENU_HANDL_RX_EQ_P2_WFM},
    {"RX WFM EQ 1.5k", SYSMENU_INT8, NULL, (uint32_t *)&TRX.RX_EQ_P3_WFM, SYSMENU_HANDL_RX_EQ_P3_WFM},
    {"RX WFM EQ 5.0k", SYSMENU_INT8, NULL, (uint32_t *)&TRX.RX_EQ_P4_WFM, SYSMENU_HANDL_RX_EQ_P4_WFM},
    {"RX WFM EQ 8.0k", SYSMENU_INT8, NULL, (uint32_t *)&TRX.RX_EQ_P5_WFM, SYSMENU_HANDL_RX_EQ_P5_WFM},
    {"RX WFM EQ 12.0k", SYSMENU_INT8, NULL, (uint32_t *)&TRX.RX_EQ_P6_WFM, SYSMENU_HANDL_RX_EQ_P6_WFM},
    {"TRX Samplerate", SYSMENU_ENUM, NULL, (uint32_t *)&TRX.SAMPLERATE_MAIN, SYSMENU_HANDL_RX_SAMPLERATE_MAIN, (const enumerate_item[4]){"48kHz", "96kHz", "192kHz", "384kHz"}},
    {"FM Samplerate", SYSMENU_ENUM, NULL, (uint32_t *)&TRX.SAMPLERATE_FM, SYSMENU_HANDL_RX_SAMPLERATE_FM, (const enumerate_item[4]){"48kHz", "96kHz", "192kHz", "384kHz"}},
    {"VAD Threshold", SYSMENU_UINT8, NULL, (uint32_t *)&TRX.VAD_THRESHOLD, SYSMENU_HANDL_RX_VAD_THRESHOLD},
#if !defined(STM32F407xx)
    {"WFM Stereo", SYSMENU_BOOLEAN, NULL, (uint32_t *)&TRX.FM_Stereo, SYSMENU_HANDL_RX_FM_Stereo},
    {"WFM Stereo Modul", SYSMENU_UINT8, NULL, (uint32_t *)&TRX.FM_Stereo_Modulation, SYSMENU_HANDL_RX_FM_Stereo_Modulation},
#endif
};

const static struct sysmenu_item_handler sysmenu_tx_handlers[] = {
    {"RF Power", SYSMENU_UINT8, NULL, (uint32_t *)&TRX.RF_Gain, SYSMENU_HANDL_TX_RFPower},
    {"CESSB", SYSMENU_BOOLEAN, NULL, (uint32_t *)&TRX.TX_CESSB, SYSMENU_HANDL_TX_CESSB},
    {"CESSB Compress", SYSMENU_FLOAT32, NULL, (uint32_t *)&TRX.TX_CESSB_COMPRESS_DB, SYSMENU_HANDL_TX_CESSB_COMPRESS_DB},
    {"Compr. MxGa AMFM", SYSMENU_UINT8, NULL, (uint32_t *)&TRX.TX_Compressor_maxgain_AMFM, SYSMENU_HANDL_TX_CompressorMaxGain_AMFM},
    {"Compr. Speed AMFM", SYSMENU_UINT8, NULL, (uint32_t *)&TRX.TX_Compressor_speed_AMFM, SYSMENU_HANDL_TX_CompressorSpeed_AMFM},
    {"Compr. MxGa SSB", SYSMENU_UINT8, NULL, (uint32_t *)&TRX.TX_Compressor_maxgain_SSB, SYSMENU_HANDL_TX_CompressorMaxGain_SSB},
    {"Compr. Speed SSB", SYSMENU_UINT8, NULL, (uint32_t *)&TRX.TX_Compressor_speed_SSB, SYSMENU_HANDL_TX_CompressorSpeed_SSB},
    {"CTCSS Frequency", SYSMENU_FLOAT32, NULL, (uint32_t *)&TRX.CTCSS_Freq, SYSMENU_HANDL_TX_CTCSS_Freq},
    {"Auto Input Switch", SYSMENU_BOOLEAN, NULL, (uint32_t *)&TRX.Auto_Input_Switch, SYSMENU_HANDL_TX_Auto_Input_Switch},
#if FT8_SUPPORT
    {"FT8 Auto CQ", SYSMENU_BOOLEAN, NULL, (uint32_t *)&TRX.FT8_Auto_CQ, SYSMENU_HANDL_TX_FT8_Auto_CQ},
#endif
    {"Input Type MAIN", SYSMENU_ENUM, NULL, (uint32_t *)&TRX.InputType_MAIN, SYSMENU_HANDL_TX_INPUT_TYPE_MAIN, (const enumerate_item[3]){"MIC", "LINE", "USB"}},
    {"Input Type DIGI", SYSMENU_ENUM, NULL, (uint32_t *)&TRX.InputType_DIGI, SYSMENU_HANDL_TX_INPUT_TYPE_DIGI, (const enumerate_item[3]){"MIC", "LINE", "USB"}},
    {"TUNER Enabled", SYSMENU_BOOLEAN, SYSMENU_HANDL_CHECK_HAS_ATU, (uint32_t *)&TRX.TUNER_Enabled, SYSMENU_HANDL_TX_TUNER_Enabled},
    {"ATU Enabled", SYSMENU_BOOLEAN, SYSMENU_HANDL_CHECK_HAS_ATU, (uint32_t *)&TRX.ATU_Enabled, SYSMENU_HANDL_TX_ATU_Enabled},
    {"ATU Cap", SYSMENU_ATU_C, SYSMENU_HANDL_CHECK_HAS_ATU, (uint32_t *)&TRX.ATU_C, SYSMENU_HANDL_TX_ATU_C},
    {"ATU Ind", SYSMENU_ATU_I, SYSMENU_HANDL_CHECK_HAS_ATU, (uint32_t *)&TRX.ATU_I, SYSMENU_HANDL_TX_ATU_I},
    {"ATU T", SYSMENU_BOOLEAN, SYSMENU_HANDL_CHECK_HAS_ATU, (uint32_t *)&TRX.ATU_T, SYSMENU_HANDL_TX_ATU_T},
    {TRX_SWR_SMOOTHED_STR, SYSMENU_INFOLINE, SYSMENU_HANDL_CHECK_HAS_ATU, 0},
    {"ATU Mem step, kHz", SYSMENU_UINT16, SYSMENU_HANDL_CHECK_HAS_ATU, (uint32_t *)&TRX.ATU_MEM_STEP_KHZ, SYSMENU_HANDL_TX_ATU_MEM_STEP_KHZ},
    {"LINE Gain", SYSMENU_UINT8, NULL, (uint32_t *)&TRX.LINE_Volume, SYSMENU_HANDL_TX_LINE_Volume},
    {"MIC Boost", SYSMENU_BOOLEAN, NULL, (uint32_t *)&TRX.MIC_Boost, SYSMENU_HANDL_TX_MIC_Boost},
    {"MIC Gain SSB", SYSMENU_FLOAT32, NULL, (uint32_t *)&TRX.MIC_Gain_SSB_DB, SYSMENU_HANDL_TX_MIC_Gain_SSB_DB},
    {"MIC Gain AM", SYSMENU_FLOAT32, NULL, (uint32_t *)&TRX.MIC_Gain_AM_DB, SYSMENU_HANDL_TX_MIC_Gain_AM_DB},
    {"MIC Gain FM", SYSMENU_FLOAT32, NULL, (uint32_t *)&TRX.MIC_Gain_FM_DB, SYSMENU_HANDL_TX_MIC_Gain_FM_DB},
    {"MIC Noise Gate", SYSMENU_INT8, NULL, (uint32_t *)&TRX.MIC_NOISE_GATE, SYSMENU_HANDL_TX_MIC_NOISE_GATE},
    {"MIC EQ 0.3k AMFM", SYSMENU_INT8, NULL, (uint32_t *)&TRX.MIC_EQ_P1_AMFM, SYSMENU_HANDL_TX_MIC_EQ_P1_AMFM},
    {"MIC EQ 0.7k AMFM", SYSMENU_INT8, NULL, (uint32_t *)&TRX.MIC_EQ_P2_AMFM, SYSMENU_HANDL_TX_MIC_EQ_P2_AMFM},
    {"MIC EQ 1.2k AMFM", SYSMENU_INT8, NULL, (uint32_t *)&TRX.MIC_EQ_P3_AMFM, SYSMENU_HANDL_TX_MIC_EQ_P3_AMFM},
    {"MIC EQ 1.8k AMFM", SYSMENU_INT8, NULL, (uint32_t *)&TRX.MIC_EQ_P4_AMFM, SYSMENU_HANDL_TX_MIC_EQ_P4_AMFM},
    {"MIC EQ 2.0k AMFM", SYSMENU_INT8, NULL, (uint32_t *)&TRX.MIC_EQ_P5_AMFM, SYSMENU_HANDL_TX_MIC_EQ_P5_AMFM},
    {"MIC EQ 2.5k AMFM", SYSMENU_INT8, NULL, (uint32_t *)&TRX.MIC_EQ_P6_AMFM, SYSMENU_HANDL_TX_MIC_EQ_P6_AMFM},
    {"MIC EQ 0.3k SSB", SYSMENU_INT8, NULL, (uint32_t *)&TRX.MIC_EQ_P1_SSB, SYSMENU_HANDL_TX_MIC_EQ_P1_SSB},
    {"MIC EQ 0.7k SSB", SYSMENU_INT8, NULL, (uint32_t *)&TRX.MIC_EQ_P2_SSB, SYSMENU_HANDL_TX_MIC_EQ_P2_SSB},
    {"MIC EQ 1.2k SSB", SYSMENU_INT8, NULL, (uint32_t *)&TRX.MIC_EQ_P3_SSB, SYSMENU_HANDL_TX_MIC_EQ_P3_SSB},
    {"MIC EQ 1.8k SSB", SYSMENU_INT8, NULL, (uint32_t *)&TRX.MIC_EQ_P4_SSB, SYSMENU_HANDL_TX_MIC_EQ_P4_SSB},
    {"MIC EQ 2.0k SSB", SYSMENU_INT8, NULL, (uint32_t *)&TRX.MIC_EQ_P5_SSB, SYSMENU_HANDL_TX_MIC_EQ_P5_SSB},
    {"MIC EQ 2.5k SSB", SYSMENU_INT8, NULL, (uint32_t *)&TRX.MIC_EQ_P6_SSB, SYSMENU_HANDL_TX_MIC_EQ_P6_SSB},
#if !defined(STM32F407xx)
    {"MIC Reverber", SYSMENU_UINT8, NULL, (uint32_t *)&TRX.MIC_REVERBER, SYSMENU_HANDL_TX_MIC_REVERBER},
#endif
    {"Pwr for each band", SYSMENU_BOOLEAN, NULL, (uint32_t *)&TRX.RF_Gain_For_Each_Band, SYSMENU_HANDL_TX_RF_Gain_For_Each_Band},
    {"Pwr for each mode", SYSMENU_BOOLEAN, NULL, (uint32_t *)&TRX.RF_Gain_For_Each_Mode, SYSMENU_HANDL_TX_RF_Gain_For_Each_Mode},
    {"Repeater Mode", SYSMENU_BOOLEAN, NULL, (uint32_t *)&TRX.RepeaterMode_shadow, SYSMENU_HANDL_TX_RepeaterMode},
    {"Repeater offset, kHz", SYSMENU_INT16, NULL, (uint32_t *)&TRX.REPEATER_Offset, SYSMENU_HANDL_TX_REPEATER_Offset},
    {"SelfHear Volume", SYSMENU_UINT8, NULL, (uint32_t *)&TRX.SELFHEAR_Volume, SYSMENU_HANDL_TX_SELFHEAR_Volume},
    {"Two Signal TUNE", SYSMENU_BOOLEAN, NULL, (uint32_t *)&TRX.TWO_SIGNAL_TUNE, SYSMENU_HANDL_TX_TWO_SIGNAL_TUNE},
    {"VOX", SYSMENU_BOOLEAN, NULL, (uint32_t *)&TRX.VOX, SYSMENU_HANDL_TX_VOX},
    {"VOX Timeout, ms", SYSMENU_UINT16, NULL, (uint32_t *)&TRX.VOX_TIMEOUT, SYSMENU_HANDL_TX_VOX_TIMEOUT},
#ifdef LAY_320x240
    {"VOX Threshold", SYSMENU_INT8, NULL, (uint32_t *)&TRX.VOX_THRESHOLD, SYSMENU_HANDL_TX_VOX_THRESHOLD},
#else
    {"VOX Threshold, dbFS", SYSMENU_INT8, NULL, (uint32_t *)&TRX.VOX_THRESHOLD, SYSMENU_HANDL_TX_VOX_THRESHOLD},
#endif
};

const static struct sysmenu_item_handler sysmenu_cw_handlers[] = {
    {"Auto CW Mode", SYSMENU_BOOLEAN, NULL, (uint32_t *)&TRX.Auto_CW_Mode, SYSMENU_HANDL_CW_Auto_CW_Mode},
    {"CW In SSB", SYSMENU_BOOLEAN, NULL, (uint32_t *)&TRX.CW_In_SSB, SYSMENU_HANDL_CW_In_SSB},
    {"DotToDash Rate", SYSMENU_FLOAT32, NULL, (uint32_t *)&TRX.CW_DotToDashRate, SYSMENU_HANDL_CW_DotToDashRate},
    {"Edges smooth, ms", SYSMENU_UINT8, NULL, (uint32_t *)&TRX.CW_EDGES_SMOOTH_MS, SYSMENU_HANDL_CW_EDGES_SMOOTH_MS},
    {"Iambic Keyer", SYSMENU_BOOLEAN, NULL, (uint32_t *)&TRX.CW_Iambic, SYSMENU_HANDL_CW_Iambic},
    {"Iambic Type", SYSMENU_ENUMR, NULL, (uint32_t *)&TRX.CW_Iambic_Type, SYSMENU_HANDL_CW_Iambic_Type, (const enumerate_item[2]){"A", "B"}},
    {"Key Invert", SYSMENU_BOOLEAN, NULL, (uint32_t *)&TRX.CW_Invert, SYSMENU_HANDL_CW_Invert},
    {"Key timeout", SYSMENU_UINT16, NULL, (uint32_t *)&TRX.CW_Key_timeout, SYSMENU_HANDL_CW_Key_timeout},
    {"Keyer", SYSMENU_BOOLEAN, NULL, (uint32_t *)&TRX.CW_KEYER, SYSMENU_HANDL_CW_Keyer},
    {"Keyer WPM", SYSMENU_UINT8, NULL, (uint32_t *)&TRX.CW_KEYER_WPM, SYSMENU_HANDL_CW_Keyer_WPM},
    {"One symbol memory", SYSMENU_BOOLEAN, NULL, (uint32_t *)&TRX.CW_OneSymbolMemory, SYSMENU_HANDL_CW_OneSymbolMemory},
    {"PTT Type", SYSMENU_ENUMR, NULL, (uint32_t *)&TRX.CW_PTT_Type, SYSMENU_HANDL_CW_PTT_Type, (const enumerate_item[3]){"Key", "PTT", "KEY+PTT"}},
    {"Pitch", SYSMENU_UINT16, NULL, (uint32_t *)&TRX.CW_Pitch, SYSMENU_HANDL_CW_Pitch},
    {"Self Hear", SYSMENU_BOOLEAN, NULL, (uint32_t *)&TRX.CW_SelfHear, SYSMENU_HANDL_CW_SelfHear},
#if !defined(FRONTPANEL_SMALL_V1)
    {"Macros 1 name", SYSMENU_RUN, NULL, 0, SYSMENU_HANDL_CW_SetCWMacrosName1},
    {"Macros 1", SYSMENU_RUN, NULL, 0, SYSMENU_HANDL_CW_SetCWMacros1},
    {"Macros 2 name", SYSMENU_RUN, NULL, 0, SYSMENU_HANDL_CW_SetCWMacrosName2},
    {"Macros 2", SYSMENU_RUN, NULL, 0, SYSMENU_HANDL_CW_SetCWMacros2},
    {"Macros 3 name", SYSMENU_RUN, NULL, 0, SYSMENU_HANDL_CW_SetCWMacrosName3},
    {"Macros 3", SYSMENU_RUN, NULL, 0, SYSMENU_HANDL_CW_SetCWMacros3},
    {"Macros 4 name", SYSMENU_RUN, NULL, 0, SYSMENU_HANDL_CW_SetCWMacrosName4},
    {"Macros 4", SYSMENU_RUN, NULL, 0, SYSMENU_HANDL_CW_SetCWMacros4},
    {"Macros 5 name", SYSMENU_RUN, NULL, 0, SYSMENU_HANDL_CW_SetCWMacrosName5},
    {"Macros 5", SYSMENU_RUN, NULL, 0, SYSMENU_HANDL_CW_SetCWMacros5},
#endif
};

const static struct sysmenu_item_handler sysmenu_screen_handlers[] = {
#if LCD_WIDTH > 700
    {"Bottom navi buttons", SYSMENU_BOOLEAN, NULL, (uint32_t *)&TRX.EnableBottomNavigationButtons, SYSMENU_HANDL_SCREEN_EnableBottomNavigationButtons},
#endif
#ifdef LAY_160x128
    {"Color Theme", SYSMENU_ENUMR, NULL, (uint32_t *)&TRX.ColorThemeId, SYSMENU_HANDL_SCREEN_COLOR_THEME, (const enumerate_item[6]){"Black", "White", "Colored", "CN", "C+Green", "C+White"}},
#else
    {"Color Theme", SYSMENU_ENUMR, NULL, (uint32_t *)&TRX.ColorThemeId, SYSMENU_HANDL_SCREEN_COLOR_THEME,
     (const enumerate_item[6]){"Black", "White", "Colored", "CN", "CN+Green", "CN+White"}},
#endif
#ifdef LAY_480x320
    {"Layout Theme", SYSMENU_ENUMR, NULL, (uint32_t *)&TRX.LayoutThemeId, SYSMENU_HANDL_SCREEN_LAYOUT_THEME, (const enumerate_item[2]){"Default", "7 Segm"}},
#endif
#ifdef LAY_800x480
    {"Layout Theme", SYSMENU_ENUMR, NULL, (uint32_t *)&TRX.LayoutThemeId, SYSMENU_HANDL_SCREEN_LAYOUT_THEME,
     (const enumerate_item[8]){"Default", "Analog", "7 Segm", "Classic", "Default+", "Analog+", "CN", "CN+"}},
#endif
#if !defined(FRONTPANEL_LITE)
    {"FFT 3D Mode", SYSMENU_ENUM, NULL, (uint32_t *)&TRX.FFT_3D, SYSMENU_HANDL_SCREEN_FFT_3D, (const enumerate_item[3]){"NO", "Lines", "Dots"}},
#endif
    {"FFT Automatic", SYSMENU_ENUM, NULL, (uint32_t *)&TRX.FFT_Automatic_Type, SYSMENU_HANDL_SCREEN_FFT_Automatic_Type, (const enumerate_item[3]){"No", "Half", "Full"}},
    {"FFT Averaging", SYSMENU_UINT8, NULL, (uint32_t *)&TRX.FFT_Averaging, SYSMENU_HANDL_SCREEN_FFT_Averaging},
#if !defined(FRONTPANEL_LITE)
    {"FFT BW Style", SYSMENU_ENUMR, NULL, (uint32_t *)&TRX.FFT_BW_Style, SYSMENU_HANDL_SCREEN_FFT_BW_Style, (const enumerate_item[4]){"", "Fill", "LowOp", "Line"}},
    {"FFT BW Position", SYSMENU_ENUMR, NULL, (uint32_t *)&TRX.FFT_BW_Position, SYSMENU_HANDL_SCREEN_FFT_BW_Position, (const enumerate_item[4]){"All", "Top+Lin", "Top", "Delay"}},
#endif
    {"FFT Background", SYSMENU_BOOLEAN, NULL, (uint32_t *)&TRX.FFT_Background, SYSMENU_HANDL_SCREEN_FFT_Background},
    {"FFT Color", SYSMENU_ENUMR, NULL, (uint32_t *)&TRX.FFT_Color, SYSMENU_HANDL_SCREEN_FFT_Color,
     (const enumerate_item[10]){"Blu>Y>R", "BlB>Y>R", "BlR>Y>R", "BGYRM", "Bla>Y>R", "Bla>Y>G", "Bla>R", "Bla>G", "Bla>Blu", "Bla>W"}},
    {"WTF Color", SYSMENU_ENUMR, NULL, (uint32_t *)&TRX.WTF_Color, SYSMENU_HANDL_SCREEN_WTF_Color,
     (const enumerate_item[10]){"Blu>Y>R", "BlB>Y>R", "BlR>Y>R", "BGYRM", "Bla>Y>R", "Bla>Y>G", "Bla>R", "Bla>G", "Bla>Blu", "Bla>W"}},
    {"FFT Compressor", SYSMENU_BOOLEAN, NULL, (uint32_t *)&TRX.FFT_Compressor, SYSMENU_HANDL_SCREEN_FFT_Compressor},
#if HRDW_HAS_WIFI
    {"DX Cluster type", SYSMENU_ENUM, NULL, (uint32_t *)&TRX.DXCluster_Type, SYSMENU_HANDL_SCREEN_DXCluster_Type, (const enumerate_item[2]){"RBN", "SUMMIT"}},
    {"FFT DXCluster", SYSMENU_BOOLEAN, NULL, (uint32_t *)&TRX.FFT_DXCluster, SYSMENU_HANDL_SCREEN_FFT_DXCluster},
    {"FFT DXClus Azimuth", SYSMENU_BOOLEAN, NULL, (uint32_t *)&TRX.FFT_DXCluster_Azimuth, SYSMENU_HANDL_SCREEN_FFT_DXCluster_Azimuth},
    {"FFT DXClus Timeout", SYSMENU_UINT8, NULL, (uint32_t *)&TRX.FFT_DXCluster_Timeout, SYSMENU_HANDL_SCREEN_FFT_DXCluster_Timeout},
    {"WOLF Cluster", SYSMENU_BOOLEAN, NULL, (uint32_t *)&TRX.WOLF_Cluster, SYSMENU_HANDL_SCREEN_WOLF_Cluster},
#endif
    {"FFT Enabled", SYSMENU_BOOLEAN, NULL, (uint32_t *)&TRX.FFT_Enabled, SYSMENU_HANDL_SCREEN_FFT_Enabled},
    {"FFT Freq Grid", SYSMENU_ENUM, NULL, (uint32_t *)&TRX.FFT_FreqGrid, SYSMENU_HANDL_SCREEN_FFT_FreqGrid, (const enumerate_item[4]){"NO", "Top", "All", "Bott"}},
    {"FFT Height", SYSMENU_UINT8, NULL, (uint32_t *)&TRX.FFT_Height, SYSMENU_HANDL_SCREEN_FFT_Height},
#if !defined(FRONTPANEL_LITE)
    {"FFT Hold Peaks", SYSMENU_BOOLEAN, NULL, (uint32_t *)&TRX.FFT_HoldPeaks, SYSMENU_HANDL_SCREEN_FFT_HoldPeaks},
    {"FFT Lens", SYSMENU_BOOLEAN, NULL, (uint32_t *)&TRX.FFT_Lens, SYSMENU_HANDL_SCREEN_FFT_Lens},
#endif
    {"FFT Manual Bottom", SYSMENU_INT16, NULL, (uint32_t *)&TRX.FFT_ManualBottom, SYSMENU_HANDL_SCREEN_FFT_ManualBottom},
    {"FFT Manual Top", SYSMENU_INT16, NULL, (uint32_t *)&TRX.FFT_ManualTop, SYSMENU_HANDL_SCREEN_FFT_ManualTop},
    {"FFT Scale Type", SYSMENU_ENUM, NULL, (uint32_t *)&TRX.FFT_Scale_Type, SYSMENU_HANDL_SCREEN_FFT_Scale_Type, (const enumerate_item[3]){"Ampl", "Squared", "dBm"}},
    {"FFT Sensitivity", SYSMENU_UINT8, NULL, (uint32_t *)&TRX.FFT_Sensitivity, SYSMENU_HANDL_SCREEN_FFT_Sensitivity},
    {"FFT Speed", SYSMENU_UINT8, NULL, (uint32_t *)&TRX.FFT_Speed, SYSMENU_HANDL_SCREEN_FFT_Speed},
    {"FFT Style", SYSMENU_ENUMR, NULL, (uint32_t *)&TRX.FFT_Style, SYSMENU_HANDL_SCREEN_FFT_Style, (const enumerate_item[6]){"", "Gradien", "Fill", "Dots", "Contour", "Gr+Cont"}},
    {"FFT Window", SYSMENU_ENUMR, NULL, (uint32_t *)&TRX.FFT_Window, SYSMENU_HANDL_SCREEN_FFT_Window,
     (const enumerate_item[9]){"", "GNuttal", "Dolph", "Blckman", "Nuttall", "BlNuttl", "Hann", "Hamming", "No"}},
    {"FFT Zoom", SYSMENU_UINT8, NULL, (uint32_t *)&TRX.FFT_Zoom, SYSMENU_HANDL_SCREEN_FFT_Zoom},
    {"FFT Zoom CW", SYSMENU_UINT8, NULL, (uint32_t *)&TRX.FFT_ZoomCW, SYSMENU_HANDL_SCREEN_FFT_ZoomCW},
#if !defined(FRONTPANEL_LITE)
    {"FFT dBm Grid", SYSMENU_BOOLEAN, NULL, (uint32_t *)&TRX.FFT_dBmGrid, SYSMENU_HANDL_SCREEN_FFT_dBmGrid},
#endif
#ifdef HAS_BRIGHTNESS_CONTROL
    {"LCD Brightness", SYSMENU_UINT8, NULL, (uint32_t *)&TRX.LCD_Brightness, SYSMENU_HANDL_SCREEN_LCD_Brightness},
    {"LCD Sleep Timeout", SYSMENU_UINT16, NULL, (uint32_t *)&TRX.LCD_SleepTimeout, SYSMENU_HANDL_SCREEN_LCD_SleepTimeout},
#endif
#if !defined(FRONTPANEL_LITE)
    {"Show Sec VFO", SYSMENU_BOOLEAN, NULL, (uint32_t *)&TRX.Show_Sec_VFO, SYSMENU_HANDL_SCREEN_Show_Sec_VFO},
#endif
    {"WTF Moving", SYSMENU_BOOLEAN, NULL, (uint32_t *)&TRX.WTF_Moving, SYSMENU_HANDL_SCREEN_WTF_Moving},
#ifdef HRDW_HAS_FUNCBUTTONS
    {"Func button 1", SYSMENU_FUNCBUTTON, NULL, (uint32_t *)&TRX.FuncButtons[0], SYSMENU_HANDL_SCREEN_FUNC_BUTTON1},
    {"Func button 2", SYSMENU_FUNCBUTTON, NULL, (uint32_t *)&TRX.FuncButtons[1], SYSMENU_HANDL_SCREEN_FUNC_BUTTON2},
    {"Func button 3", SYSMENU_FUNCBUTTON, NULL, (uint32_t *)&TRX.FuncButtons[2], SYSMENU_HANDL_SCREEN_FUNC_BUTTON3},
    {"Func button 4", SYSMENU_FUNCBUTTON, NULL, (uint32_t *)&TRX.FuncButtons[3], SYSMENU_HANDL_SCREEN_FUNC_BUTTON4},
    {"Func button 5", SYSMENU_FUNCBUTTON, NULL, (uint32_t *)&TRX.FuncButtons[4], SYSMENU_HANDL_SCREEN_FUNC_BUTTON5},
    {"Func button 6", SYSMENU_FUNCBUTTON, NULL, (uint32_t *)&TRX.FuncButtons[5], SYSMENU_HANDL_SCREEN_FUNC_BUTTON6},
    {"Func button 7", SYSMENU_FUNCBUTTON, NULL, (uint32_t *)&TRX.FuncButtons[6], SYSMENU_HANDL_SCREEN_FUNC_BUTTON7},
    {"Func button 8", SYSMENU_FUNCBUTTON, NULL, (uint32_t *)&TRX.FuncButtons[7], SYSMENU_HANDL_SCREEN_FUNC_BUTTON8},
    {"Func button 9", SYSMENU_FUNCBUTTON, NULL, (uint32_t *)&TRX.FuncButtons[8], SYSMENU_HANDL_SCREEN_FUNC_BUTTON9},
    {"Func button 10", SYSMENU_FUNCBUTTON, NULL, (uint32_t *)&TRX.FuncButtons[9], SYSMENU_HANDL_SCREEN_FUNC_BUTTON10},
    {"Func button 11", SYSMENU_FUNCBUTTON, NULL, (uint32_t *)&TRX.FuncButtons[10], SYSMENU_HANDL_SCREEN_FUNC_BUTTON11},
    {"Func button 12", SYSMENU_FUNCBUTTON, NULL, (uint32_t *)&TRX.FuncButtons[11], SYSMENU_HANDL_SCREEN_FUNC_BUTTON12},
    {"Func button 13", SYSMENU_FUNCBUTTON, NULL, (uint32_t *)&TRX.FuncButtons[12], SYSMENU_HANDL_SCREEN_FUNC_BUTTON13},
    {"Func button 14", SYSMENU_FUNCBUTTON, NULL, (uint32_t *)&TRX.FuncButtons[13], SYSMENU_HANDL_SCREEN_FUNC_BUTTON14},
    {"Func button 15", SYSMENU_FUNCBUTTON, NULL, (uint32_t *)&TRX.FuncButtons[14], SYSMENU_HANDL_SCREEN_FUNC_BUTTON15},
    {"Func button 16", SYSMENU_FUNCBUTTON, NULL, (uint32_t *)&TRX.FuncButtons[15], SYSMENU_HANDL_SCREEN_FUNC_BUTTON16},
    {"Func button 17", SYSMENU_FUNCBUTTON, NULL, (uint32_t *)&TRX.FuncButtons[16], SYSMENU_HANDL_SCREEN_FUNC_BUTTON17},
    {"Func button 18", SYSMENU_FUNCBUTTON, NULL, (uint32_t *)&TRX.FuncButtons[17], SYSMENU_HANDL_SCREEN_FUNC_BUTTON18},
    {"Func button 19", SYSMENU_FUNCBUTTON, NULL, (uint32_t *)&TRX.FuncButtons[18], SYSMENU_HANDL_SCREEN_FUNC_BUTTON19},
    {"Func button 20", SYSMENU_FUNCBUTTON, NULL, (uint32_t *)&TRX.FuncButtons[19], SYSMENU_HANDL_SCREEN_FUNC_BUTTON20},
    {"Func button 21", SYSMENU_FUNCBUTTON, NULL, (uint32_t *)&TRX.FuncButtons[20], SYSMENU_HANDL_SCREEN_FUNC_BUTTON21},
    {"Func button 22", SYSMENU_FUNCBUTTON, NULL, (uint32_t *)&TRX.FuncButtons[21], SYSMENU_HANDL_SCREEN_FUNC_BUTTON22},
    {"Func button 23", SYSMENU_FUNCBUTTON, NULL, (uint32_t *)&TRX.FuncButtons[22], SYSMENU_HANDL_SCREEN_FUNC_BUTTON23},
    {"Func button 24", SYSMENU_FUNCBUTTON, NULL, (uint32_t *)&TRX.FuncButtons[23], SYSMENU_HANDL_SCREEN_FUNC_BUTTON24},
    {"Func button 25", SYSMENU_FUNCBUTTON, NULL, (uint32_t *)&TRX.FuncButtons[24], SYSMENU_HANDL_SCREEN_FUNC_BUTTON25},
#if (FUNCBUTTONS_ON_PAGE * FUNCBUTTONS_PAGES) > 25
    {"Func button 26", SYSMENU_FUNCBUTTON, NULL, (uint32_t *)&TRX.FuncButtons[25], SYSMENU_HANDL_SCREEN_FUNC_BUTTON26},
    {"Func button 27", SYSMENU_FUNCBUTTON, NULL, (uint32_t *)&TRX.FuncButtons[26], SYSMENU_HANDL_SCREEN_FUNC_BUTTON27},
#if (FUNCBUTTONS_ON_PAGE * FUNCBUTTONS_PAGES) > 27
    {"Func button 28", SYSMENU_FUNCBUTTON, NULL, (uint32_t *)&TRX.FuncButtons[27], SYSMENU_HANDL_SCREEN_FUNC_BUTTON28},
#if (FUNCBUTTONS_ON_PAGE * FUNCBUTTONS_PAGES) > 28
    {"Func button 29", SYSMENU_FUNCBUTTON, NULL, (uint32_t *)&TRX.FuncButtons[28], SYSMENU_HANDL_SCREEN_FUNC_BUTTON29},
    {"Func button 30", SYSMENU_FUNCBUTTON, NULL, (uint32_t *)&TRX.FuncButtons[29], SYSMENU_HANDL_SCREEN_FUNC_BUTTON30},
#if (FUNCBUTTONS_ON_PAGE * FUNCBUTTONS_PAGES) > 30
    {"Func button 31", SYSMENU_FUNCBUTTON, NULL, (uint32_t *)&TRX.FuncButtons[30], SYSMENU_HANDL_SCREEN_FUNC_BUTTON31},
    {"Func button 32", SYSMENU_FUNCBUTTON, NULL, (uint32_t *)&TRX.FuncButtons[31], SYSMENU_HANDL_SCREEN_FUNC_BUTTON32},
#if (FUNCBUTTONS_ON_PAGE * FUNCBUTTONS_PAGES) > 32
    {"Func button 33", SYSMENU_FUNCBUTTON, NULL, (uint32_t *)&TRX.FuncButtons[32], SYSMENU_HANDL_SCREEN_FUNC_BUTTON33},
    {"Func button 34", SYSMENU_FUNCBUTTON, NULL, (uint32_t *)&TRX.FuncButtons[33], SYSMENU_HANDL_SCREEN_FUNC_BUTTON34},
    {"Func button 35", SYSMENU_FUNCBUTTON, NULL, (uint32_t *)&TRX.FuncButtons[34], SYSMENU_HANDL_SCREEN_FUNC_BUTTON35},
#if (FUNCBUTTONS_ON_PAGE * FUNCBUTTONS_PAGES) > 35
    {"Func button 36", SYSMENU_FUNCBUTTON, NULL, (uint32_t *)&TRX.FuncButtons[35], SYSMENU_HANDL_SCREEN_FUNC_BUTTON36},
#endif
#if (FUNCBUTTONS_ON_PAGE * FUNCBUTTONS_PAGES) > 36
    {"Func button 37", SYSMENU_FUNCBUTTON, NULL, (uint32_t *)&TRX.FuncButtons[36], SYSMENU_HANDL_SCREEN_FUNC_BUTTON37},
#endif
#if (FUNCBUTTONS_ON_PAGE * FUNCBUTTONS_PAGES) > 37
    {"Func button 38", SYSMENU_FUNCBUTTON, NULL, (uint32_t *)&TRX.FuncButtons[37], SYSMENU_HANDL_SCREEN_FUNC_BUTTON38},
#endif
#if (FUNCBUTTONS_ON_PAGE * FUNCBUTTONS_PAGES) > 38
    {"Func button 39", SYSMENU_FUNCBUTTON, NULL, (uint32_t *)&TRX.FuncButtons[38], SYSMENU_HANDL_SCREEN_FUNC_BUTTON39},
#endif
#if (FUNCBUTTONS_ON_PAGE * FUNCBUTTONS_PAGES) > 39
    {"Func button 40", SYSMENU_FUNCBUTTON, NULL, (uint32_t *)&TRX.FuncButtons[39], SYSMENU_HANDL_SCREEN_FUNC_BUTTON40},
#endif
#endif
#endif
#endif
#endif
#endif
#endif
};

const static struct sysmenu_item_handler sysmenu_decoders_handlers[] = {
    {"CW Decoder", SYSMENU_BOOLEAN, NULL, (uint32_t *)&TRX.CW_Decoder, SYSMENU_HANDL_DECODERS_CW_Decoder},
    {"CW Decod. Threshold", SYSMENU_UINT8, NULL, (uint32_t *)&TRX.CW_Decoder_Threshold, SYSMENU_HANDL_DECODERS_CW_Decoder_Threshold},
#if !defined(FRONTPANEL_LITE)
    {"RDS Decoder", SYSMENU_BOOLEAN, NULL, (uint32_t *)&TRX.RDS_Decoder, SYSMENU_HANDL_DECODERS_RDS_Decoder},
#endif
    {"RTTY Speed", SYSMENU_UINT16, NULL, (uint32_t *)&TRX.RTTY_Speed, SYSMENU_HANDL_DECODERS_RTTY_Speed},
    {"RTTY Shift", SYSMENU_UINT16, NULL, (uint32_t *)&TRX.RTTY_Shift, SYSMENU_HANDL_DECODERS_RTTY_Shift},
    {"RTTY Freq", SYSMENU_UINT16, NULL, (uint32_t *)&TRX.RTTY_Freq, SYSMENU_HANDL_DECODERS_RTTY_Freq},
    {"RTTY StopBits", SYSMENU_ENUM, NULL, (uint32_t *)&TRX.RTTY_StopBits, SYSMENU_HANDL_DECODERS_RTTY_StopBits, (const enumerate_item[3]){"1", "1.5", "2"}},
    {"RTTY InvertBits", SYSMENU_BOOLEAN, NULL, (uint32_t *)&TRX.RTTY_InvertBits, SYSMENU_HANDL_DECODERS_RTTY_InvertBits},
};

#if HRDW_HAS_WIFI
const static struct sysmenu_item_handler sysmenu_wifi_handlers[] = {
#ifdef LAY_320x240
    {"WIFI Enabled", SYSMENU_BOOLEAN, NULL, (uint32_t *)&WIFI.Enabled, SYSMENU_HANDL_WIFI_Enabled},
    {"WIFI Network 1", SYSMENU_RUN, NULL, 0, SYSMENU_HANDL_WIFI_SelectAP1},
    {"WIFI Network 1 Pas", SYSMENU_RUN, NULL, 0, SYSMENU_HANDL_WIFI_SetAP1password},
    {"WIFI Network 2", SYSMENU_RUN, NULL, 0, SYSMENU_HANDL_WIFI_SelectAP2},
    {"WIFI Network 2 Pas", SYSMENU_RUN, NULL, 0, SYSMENU_HANDL_WIFI_SetAP2password},
    {"WIFI Network 3", SYSMENU_RUN, NULL, 0, SYSMENU_HANDL_WIFI_SelectAP3},
    {"WIFI Network 3 Pas", SYSMENU_RUN, NULL, 0, SYSMENU_HANDL_WIFI_SetAP3password},
    {"WIFI Timezone", SYSMENU_TIMEZONE, NULL, (uint32_t *)&WIFI.Timezone, SYSMENU_HANDL_WIFI_Timezone},
    {"WIFI CAT Server", SYSMENU_BOOLEAN, NULL, (uint32_t *)&WIFI.CAT_Server, SYSMENU_HANDL_WIFI_CAT_Server},
    {"WIFI Update ESP", SYSMENU_RUN, NULL, 0, SYSMENU_HANDL_WIFI_UpdateFW},
    {"ALLQSO.RU Token", SYSMENU_RUN, NULL, 0, SYSMENU_HANDL_WIFI_SetALLQSO_TOKEN},
    {"ALLQSO.RU LogId", SYSMENU_RUN, NULL, 0, SYSMENU_HANDL_WIFI_SetALLQSO_LOGID},
#else
    {"WIFI Enabled", SYSMENU_BOOLEAN, NULL, (uint32_t *)&WIFI.Enabled, SYSMENU_HANDL_WIFI_Enabled},
    {"WIFI Network 1", SYSMENU_RUN, NULL, 0, SYSMENU_HANDL_WIFI_SelectAP1},
    {"WIFI Network 1 Pass", SYSMENU_RUN, NULL, 0, SYSMENU_HANDL_WIFI_SetAP1password},
    {"WIFI Network 2", SYSMENU_RUN, NULL, 0, SYSMENU_HANDL_WIFI_SelectAP2},
    {"WIFI Network 2 Pass", SYSMENU_RUN, NULL, 0, SYSMENU_HANDL_WIFI_SetAP2password},
    {"WIFI Network 3", SYSMENU_RUN, NULL, 0, SYSMENU_HANDL_WIFI_SelectAP3},
    {"WIFI Network 3 Pass", SYSMENU_RUN, NULL, 0, SYSMENU_HANDL_WIFI_SetAP3password},
    {"WIFI Timezone", SYSMENU_TIMEZONE, NULL, (uint32_t *)&WIFI.Timezone, SYSMENU_HANDL_WIFI_Timezone},
    {"WIFI CAT Server", SYSMENU_BOOLEAN, NULL, (uint32_t *)&WIFI.CAT_Server, SYSMENU_HANDL_WIFI_CAT_Server},
    {"WIFI Update ESP", SYSMENU_RUN, NULL, 0, SYSMENU_HANDL_WIFI_UpdateFW},
    {"ALLQSO.RU Token", SYSMENU_RUN, NULL, 0, SYSMENU_HANDL_WIFI_SetALLQSO_TOKEN},
    {"ALLQSO.RU LogId", SYSMENU_RUN, NULL, 0, SYSMENU_HANDL_WIFI_SetALLQSO_LOGID},
#endif
    {WIFI_AP, SYSMENU_INFOLINE, 0, 0},
    {WIFI_IP, SYSMENU_INFOLINE, 0, 0},
};
#endif

#if HRDW_HAS_SD
const static struct sysmenu_item_handler sysmenu_sd_handlers[] = {
    {"File Manager", SYSMENU_RUN, NULL, 0, SYSMENU_HANDL_SD_Filemanager},
    {"Record CQ message", SYSMENU_RUN, NULL, 0, SYSMENU_HANDL_RECORD_CQ_WAV},
    {"USB SD Card Reader", SYSMENU_BOOLEAN, NULL, (uint32_t *)&SD_USBCardReader, SYSMENU_HANDL_SD_USB},
#ifdef LAY_320x240
    {"Export to SD", SYSMENU_RUN, NULL, 0, SYSMENU_HANDL_SD_ExportSettingsDialog},
    {"Import from SD", SYSMENU_RUN, NULL, 0, SYSMENU_HANDL_SD_ImportSettingsDialog},
#else
    {"Export Settings to SD", SYSMENU_RUN, NULL, 0, SYSMENU_HANDL_SD_ExportSettingsDialog},
    {"Import Settings frm SD", SYSMENU_RUN, NULL, 0, SYSMENU_HANDL_SD_ImportSettingsDialog},
#endif
    {"Format SD card", SYSMENU_RUN, NULL, 0, SYSMENU_HANDL_SD_FormatDialog},
};

const static struct sysmenu_item_handler sysmenu_sd_export_handlers[] = {
    {"Back", SYSMENU_RUN, NULL, 0, SYSMENU_HANDL_Back},
    {"Export Settings 1", SYSMENU_RUN, NULL, 0, SYSMENU_HANDL_SD_ExportSettings1},
    {"Export Settings 2", SYSMENU_RUN, NULL, 0, SYSMENU_HANDL_SD_ExportSettings2},
    {"Export Settings 3", SYSMENU_RUN, NULL, 0, SYSMENU_HANDL_SD_ExportSettings3},
    {"Export Calibration 1", SYSMENU_RUN, NULL, 0, SYSMENU_HANDL_SD_ExportCalibrations1},
    {"Export Calibration 2", SYSMENU_RUN, NULL, 0, SYSMENU_HANDL_SD_ExportCalibrations2},
    {"Export Calibration 3", SYSMENU_RUN, NULL, 0, SYSMENU_HANDL_SD_ExportCalibrations3},
};

const static struct sysmenu_item_handler sysmenu_sd_import_handlers[] = {
    {"Back", SYSMENU_RUN, NULL, 0, SYSMENU_HANDL_Back},
    {"Import Settings 1", SYSMENU_RUN, NULL, 0, SYSMENU_HANDL_SD_ImportSettings1},
    {"Import Settings 2", SYSMENU_RUN, NULL, 0, SYSMENU_HANDL_SD_ImportSettings2},
    {"Import Settings 3", SYSMENU_RUN, NULL, 0, SYSMENU_HANDL_SD_ImportSettings3},
    {"Import Calibration 1", SYSMENU_RUN, NULL, 0, SYSMENU_HANDL_SD_ImportCalibrations1},
    {"Import Calibration 2", SYSMENU_RUN, NULL, 0, SYSMENU_HANDL_SD_ImportCalibrations2},
    {"Import Calibration 3", SYSMENU_RUN, NULL, 0, SYSMENU_HANDL_SD_ImportCalibrations3},
};
const static struct sysmenu_item_handler sysmenu_sd_format_handlers[] = {
    {"Back", SYSMENU_RUN, NULL, 0, SYSMENU_HANDL_Back},
#ifdef LAY_320x240
    {"Yes, Format Card", SYSMENU_RUN, NULL, 0, SYSMENU_HANDL_SD_Format},
#else
    {"Yes, Format SD Card", SYSMENU_RUN, NULL, 0, SYSMENU_HANDL_SD_Format},
#endif
};

const static struct sysmenu_item_handler sysmenu_sat_handlers[] = {
    {"SAT Mode", SYSMENU_BOOLEAN, NULL, (uint32_t *)&TRX.SatMode, SYSMENU_HANDL_SAT_SatMode},
    {"Download TLE", SYSMENU_RUN, NULL, 0, SYSMENU_HANDL_SAT_DownloadTLE},
    {"Select SAT", SYSMENU_RUN, NULL, 0, SYSMENU_HANDL_SAT_SelectSAT},
    {"QTH Lat", SYSMENU_RUN, NULL, 0, SYSMENU_HANDL_SAT_QTHLat},
    {"QTH Lon", SYSMENU_RUN, NULL, 0, SYSMENU_HANDL_SAT_QTHLon},
    {"QTH Alt", SYSMENU_RUN, NULL, 0, SYSMENU_HANDL_SAT_QTHAlt},
};
#endif
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
