witalis3/UA3REO-DDC-Transceiver/STM32/Src/trx_manager.c

#include "trx_manager.h"
#include "FT8/FT8_main.h"
#include "agc.h"
#include "atu.h"
#include "audio_filters.h"
#include "auto_notch.h"
#include "bands.h"
#include "codec.h"
#include "cw.h"
#include "cw_decoder.h"
#include "filemanager.h"
#include "fpga.h"
#include "front_unit.h"
#include "functions.h"
#include "hardware.h"
#include "lcd.h"
#include "main.h"
#include "noise_reduction.h"
#include "pre_distortion.h"
#include "rf_unit.h"
#include "satellite.h"
#include "sd.h"
#include "self_test.h"
#include "settings.h"
#include "snap.h"
#include "swr_analyzer.h"
#include "system_menu.h"
#include "usbd_audio_if.h"
#include "vad.h"

volatile bool TRX_ptt_hard = false;
volatile bool TRX_ptt_soft = false;
volatile bool TRX_old_ptt_soft = false;
volatile bool TRX_RX1_IQ_swap = false;
volatile bool TRX_RX2_IQ_swap = false;
volatile bool TRX_TX_IQ_swap = false;
volatile bool TRX_Tune = false;
volatile bool TRX_Inited = false;
volatile float32_t TRX_RX1_dBm = -100.0f;
volatile float32_t TRX_RX2_dBm = -100.0f;
volatile float32_t TRX_RX1_dBm_measurement = -100.0f;
volatile bool TRX_ADC_OTR = false;
volatile bool TRX_DAC_OTR = false;
volatile bool TRX_PWR_ALC_SWR_OVERFLOW = false;
volatile bool TRX_MIC_BELOW_NOISEGATE = false;
volatile int16_t TRX_ADC_MINAMPLITUDE = 0;
volatile int16_t TRX_ADC_MAXAMPLITUDE = 0;
volatile uint32_t TRX_SNTP_Synced = 0; // time of the last time synchronization
volatile int_fast16_t TRX_RIT = 0;
volatile int_fast16_t TRX_XIT = 0;
volatile float32_t TRX_MAX_TX_Amplitude = 1.0f;
volatile float32_t TRX_PWR_Forward = 0;
volatile float32_t TRX_PWR_Backward = 0;
volatile float32_t TRX_SWR = 0;
volatile float32_t TRX_PWR_Forward_SMOOTHED = 0;
volatile float32_t TRX_PWR_Backward_SMOOTHED = 0;
volatile float32_t TRX_SWR_SMOOTHED = 0;
char TRX_SWR_SMOOTHED_STR[12] = "SWR: 1.0";
volatile float32_t TRX_VLT_forward = 0;  // Tisho
volatile float32_t TRX_VLT_backward = 0; // Tisho
volatile float32_t TRX_ALC_OUT = 0;
volatile float32_t TRX_ALC_IN = 0;
volatile bool TRX_SWR_PROTECTOR = false;
volatile bool TRX_DAC_DIV0 = false;
volatile bool TRX_DAC_DIV1 = false;
volatile bool TRX_DAC_HP1 = false;
volatile bool TRX_DAC_HP2 = false;
volatile bool TRX_DAC_X4 = false;
volatile bool TRX_DCDC_Freq = false;
volatile bool TRX_DAC_DRV_A0 = true;
volatile bool TRX_DAC_DRV_A1 = true;
volatile float32_t TRX_STM32_VREF = 3.3f;         // voltage on STM32
volatile float32_t TRX_STM32_TEMPERATURE = 30.0f; // STM32 temperature
volatile float32_t TRX_IQ_phase_error = 0.0f;
volatile bool TRX_Temporary_Stop_BandMap = false;
volatile uint32_t TRX_Temporary_Mute_StartTime = 0;
uint32_t TRX_freq_phrase = 0;
uint32_t TRX_freq_phrase2 = 0;
uint32_t TRX_freq_phrase_tx = 0;
volatile float32_t TRX_RF_Temperature = 0.0f;
volatile bool TRX_ScanMode = false;
bool TRX_phase_restarted = false;
uint32_t TRX_TX_StartTime = 0;
uint32_t TRX_TX_EndTime = 0;
uint32_t TRX_Inactive_Time = 0;
uint32_t TRX_DXCluster_UpdateTime = 0;
uint32_t TRX_SAT_UpdateTime = 0;
uint32_t TRX_WOLF_Cluster_UpdateTime = 0;
volatile float32_t TRX_PWR_Voltage = 12.0f;
volatile float32_t TRX_PWR_Current = 0.0f;
volatile float32_t TRX_RF_Current = 0.0f;
volatile float32_t TRX_VBAT_Voltage = 0.0f;
volatile float32_t TRX_NoiseFloor = -150.0f;
volatile uint_fast16_t CW_Key_Timeout_est = 0;
uint32_t dbg_FPGA_samples = 0;
uint8_t TRX_TX_Harmonic = 1;
uint8_t TRX_TX_sendZeroes = 0;
int8_t TRX_MemoryChannelSelected;
volatile bool TRX_REPEATER_Applied = false;

static uint_fast8_t TRX_TXRXMode = 0; // 0 - undef, 1 - rx, 2 - tx, 3 - txrx
static bool TRX_SPLIT_Applied = false;
static void TRX_Start_RX(void);
static void TRX_Start_TX(void);
static void TRX_Start_TXRX(void);

void TRX_Init() {
	TRX_Start_RX();
	CODEC_TXRX_mode();
	CODEC_start_i2s_and_dma();
	uint_fast8_t saved_mode = CurrentVFO->Mode;
	TRX_setFrequency(CurrentVFO->Freq, CurrentVFO);
	TRX_setMode(saved_mode, CurrentVFO);
	HRDW_Init();
#if HRDW_HAS_SD
	SAT_init();
#endif
}

void TRX_Restart_Mode() {
	ADCDAC_OVR_StatusLatency = 0;
	uint_fast8_t mode = CurrentVFO->Mode;

	// Switch mode
	if (TRX_on_TX) {
		if (mode == TRX_MODE_LOOPBACK || mode == TRX_MODE_CW || FULL_DUPLEX) {
			TRX_Start_TXRX();
		} else {
			TRX_Start_TX();
		}
	} else {
		TRX_Start_RX();
		TRX_TX_sendZeroes = 0;
		TRX_SWR_PROTECTOR = false;
	}

	// SPLIT
	if (TRX.SPLIT_Enabled && !TRX_SPLIT_Applied) {
		TRX_SPLIT_Applied = true;

		TRX.selected_vfo = !TRX.selected_vfo;
		if (!TRX.selected_vfo) {
			CurrentVFO = &TRX.VFO_A;
			SecondaryVFO = &TRX.VFO_B;
		} else {
			CurrentVFO = &TRX.VFO_B;
			SecondaryVFO = &TRX.VFO_A;
		}
		TRX_setFrequency(CurrentVFO->Freq, CurrentVFO);
		TRX_setMode(CurrentVFO->Mode, CurrentVFO);

		int8_t band = getBandFromFreq(CurrentVFO->Freq, true);
		TRX.ANT_RX = TRX.BANDS_SAVED_SETTINGS[band].ANT_RX;
		TRX.ANT_TX = TRX.BANDS_SAVED_SETTINGS[band].ANT_TX;

		LCD_UpdateQuery.FreqInfoRedraw = true;
		LCD_UpdateQuery.TopButtons = true;
		LCD_UpdateQuery.StatusInfoGUIRedraw = true;
	}

	// Repeater mode
	if (TRX.RepeaterMode_shadow && !TRX_REPEATER_Applied) {
		TRX_REPEATER_Applied = true;

		if (TRX_on_TX) {
			TRX_setFrequency(CurrentVFO->Freq + TRX.REPEATER_Offset * 1000, CurrentVFO);
		} else {
			TRX_setFrequency(CurrentVFO->Freq - TRX.REPEATER_Offset * 1000, CurrentVFO);
		}

		LCD_UpdateQuery.FreqInfoRedraw = true;
		LCD_UpdateQuery.TopButtons = true;
		LCD_UpdateQuery.StatusInfoGUIRedraw = true;
	}

	// Ant swap for mode 1RX/2TX and others
	ATU_Load_Memory(TRX_on_TX ? TRX.ANT_TX : TRX.ANT_RX, CurrentVFO->Freq);

	// CW_In_SSB
	if (CW_In_SSB_applyed == 1 && !TRX_on_TX) { // return to LSB
		CW_In_SSB_applyed = 0;
		TRX_setMode(TRX_MODE_LSB, CurrentVFO);
		TRX_setFrequency(CurrentVFO->Freq + TRX.CW_Pitch, CurrentVFO);
	}
	if (CW_In_SSB_applyed == 2 && !TRX_on_TX) { // return to USB
		CW_In_SSB_applyed = 0;
		TRX_setMode(TRX_MODE_USB, CurrentVFO);
		TRX_setFrequency(CurrentVFO->Freq - TRX.CW_Pitch, CurrentVFO);
	}

	// XIT
	if (TRX.XIT_Enabled) {
		LCD_UpdateQuery.FreqInfoRedraw = true;
	}
}

static void TRX_Start_RX() {
	if (TRX_TXRXMode == 1) {
		return;
	}
	println("RX MODE");
	TRX_phase_restarted = false;
	RF_UNIT_UpdateState(false);
	CODEC_CleanBuffer();
	Processor_NeedRXBuffer = false;
	CODEC_Buffer_underrun = false;
	CODEC_DMA_state = true;
	TRX_SPLIT_Applied = false;
	TRX_REPEATER_Applied = false;
	TRX_TXRXMode = 1;

	// clean TX buffer
	dma_memset((void *)&FPGA_Audio_SendBuffer_Q[0], 0x00, sizeof(FPGA_Audio_SendBuffer_Q));
	dma_memset((void *)&FPGA_Audio_SendBuffer_I[0], 0x00, sizeof(FPGA_Audio_SendBuffer_I));

	LCD_UpdateQuery.StatusInfoGUIRedraw = true;
	NeedReinitReverber = true;
	NeedFFTReinit = true;

	// FPGA_NeedRestart_TX = true;
}

static void TRX_Start_TX() {
	if (TRX_TXRXMode == 2) {
		return;
	}
	println("TX MODE");
	RF_UNIT_UpdateState(false);
	CODEC_CleanBuffer();
	TRX_TX_StartTime = HAL_GetTick();
	TRX_SPLIT_Applied = false;
	TRX_REPEATER_Applied = false;
	TRX_TXRXMode = 2;
#if !defined(FRONTPANEL_LITE)
	CWDecoder_SetWPM(TRX.CW_KEYER_WPM);
#endif

	LCD_UpdateQuery.StatusInfoGUIRedraw = true;
	NeedReinitReverber = true;
	NeedFFTReinit = true;
}

static void TRX_Start_TXRX() {
	if (TRX_TXRXMode == 3) {
		return;
	}
	println("TXRX MODE");
	RF_UNIT_UpdateState(false);
	CODEC_CleanBuffer();
	TRX_TX_StartTime = HAL_GetTick();
	TRX_SPLIT_Applied = false;
	TRX_REPEATER_Applied = false;
	TRX_TXRXMode = 3;
#if !defined(FRONTPANEL_LITE)
	CWDecoder_SetWPM(TRX.CW_KEYER_WPM);
#endif

	LCD_UpdateQuery.StatusInfoGUIRedraw = true;
	NeedReinitReverber = true;
	NeedFFTReinit = true;

	// FPGA_NeedRestart_TX = true;
}

void TRX_ptt_change(void) {
	TRX_Inactive_Time = 0;

	if (!TRX_Inited) {
		return;
	}

	if (TRX_Tune) {
		TRX_Tune = false;
	}

	bool notx = TRX_TX_Disabled(CurrentVFO->Freq) && !TRX_REPEATER_Applied;
	if (notx) {
		TRX_ptt_soft = false;
		TRX_ptt_hard = false;
		return;
	}

	if (CurrentVFO->Mode == TRX_MODE_CW && TRX.CW_PTT_Type == KEY_PTT) // cw ptt type
	{
		TRX_ptt_soft = false;
		CW_key_serial = false;
		return;
	}

	bool TRX_new_ptt_hard = !HAL_GPIO_ReadPin(PTT_IN_GPIO_Port, PTT_IN_Pin);
	if (TRX_ptt_hard != TRX_new_ptt_hard) {
		if (TRX.Auto_Input_Switch) {
			if (CurrentVFO->Mode == TRX_MODE_DIGI_L || CurrentVFO->Mode == TRX_MODE_DIGI_U || CurrentVFO->Mode == TRX_MODE_RTTY || CurrentVFO->Mode == TRX_MODE_IQ) {
				TRX.InputType_DIGI = TRX_INPUT_MIC;
			} else {
				TRX.InputType_MAIN = TRX_INPUT_MIC;
			}
		}

		TRX_ptt_hard = TRX_new_ptt_hard;
		TRX_ptt_soft = false;
		CW_key_serial = false;
		LCD_UpdateQuery.StatusInfoGUIRedraw = true;
		FPGA_NeedSendParams = true;
		TRX_Restart_Mode();
	}
	if (TRX_ptt_soft != TRX_old_ptt_soft) {
		if (TRX.Auto_Input_Switch) {
			if (CurrentVFO->Mode == TRX_MODE_DIGI_L || CurrentVFO->Mode == TRX_MODE_DIGI_U || CurrentVFO->Mode == TRX_MODE_RTTY || CurrentVFO->Mode == TRX_MODE_IQ) {
				TRX.InputType_DIGI = TRX_INPUT_USB;
			} else {
				TRX.InputType_MAIN = TRX_INPUT_USB;
			}
		}

		TRX_old_ptt_soft = TRX_ptt_soft;
		LCD_UpdateQuery.StatusInfoGUIRedraw = true;
		FPGA_NeedSendParams = true;
		TRX_Restart_Mode();
	}
}
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
